MRCDPLS/FdD_Equipo_07/Proyecto/MóduloMecánico/Certificados/Marcelo Alarcon Camones/CertificadosUnidos-Marcelo.pdf

Marcelo Alarcón

Introduction to Sketching

April 28, 2026

Marcelo Alarcón

Introduction to Part Studios

April 28, 2026

Marcelo Alarcón

April 28, 2026

Introduction to Onshape Assemblies

Marcelo Alarcón

April 28, 2026

Detailed Drawings

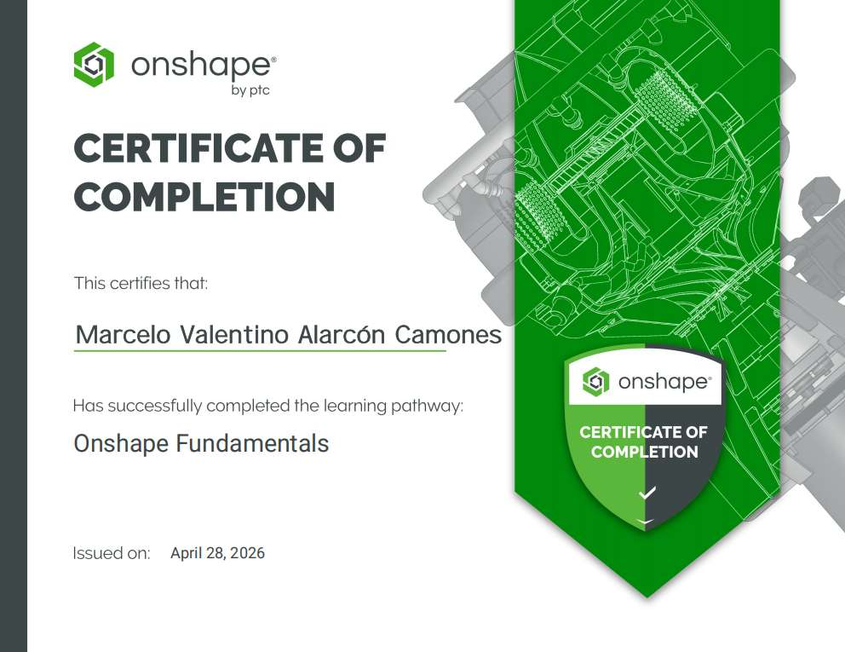
[picture p44: page 5]
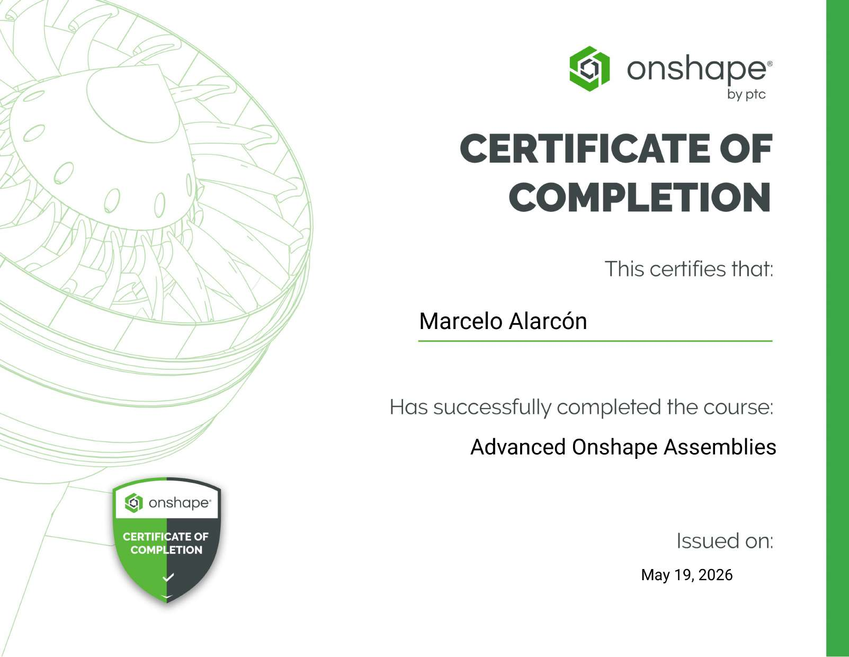
[picture p45: page 6]
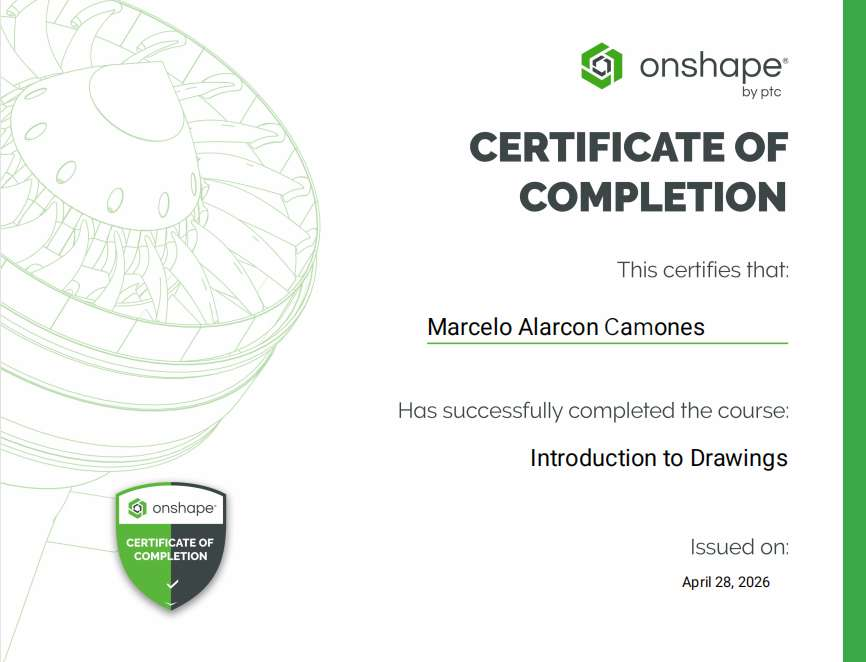
[picture p46: page 7]
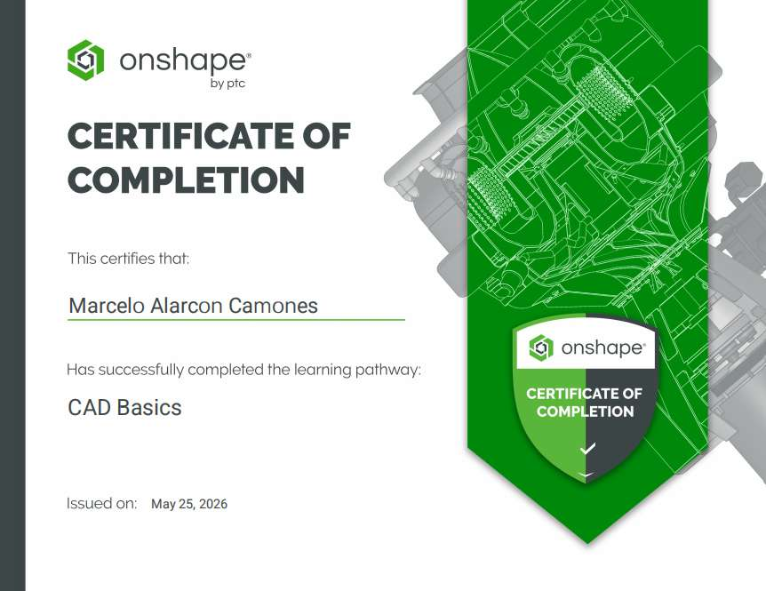
[picture p47: page 8]
