MRCDPLS/FdD_Equipo_07/Proyecto/MóduloMecánico/Certificados/Mariluz Quispe Garcia/CertificadosUnidos-Mariluz.pdf

Mariluz Quispe Garcia

Introduction to Sketching

April 28, 2026

Mariluz Quispe Garcia

Introduction to Part Studios

April 28, 2026

Mariluz Quispe Garcia

April 28, 2026

Introduction to Onshape Assemblies

Mariluz Quispe Garcia

April 28, 2026

Detailed Drawings

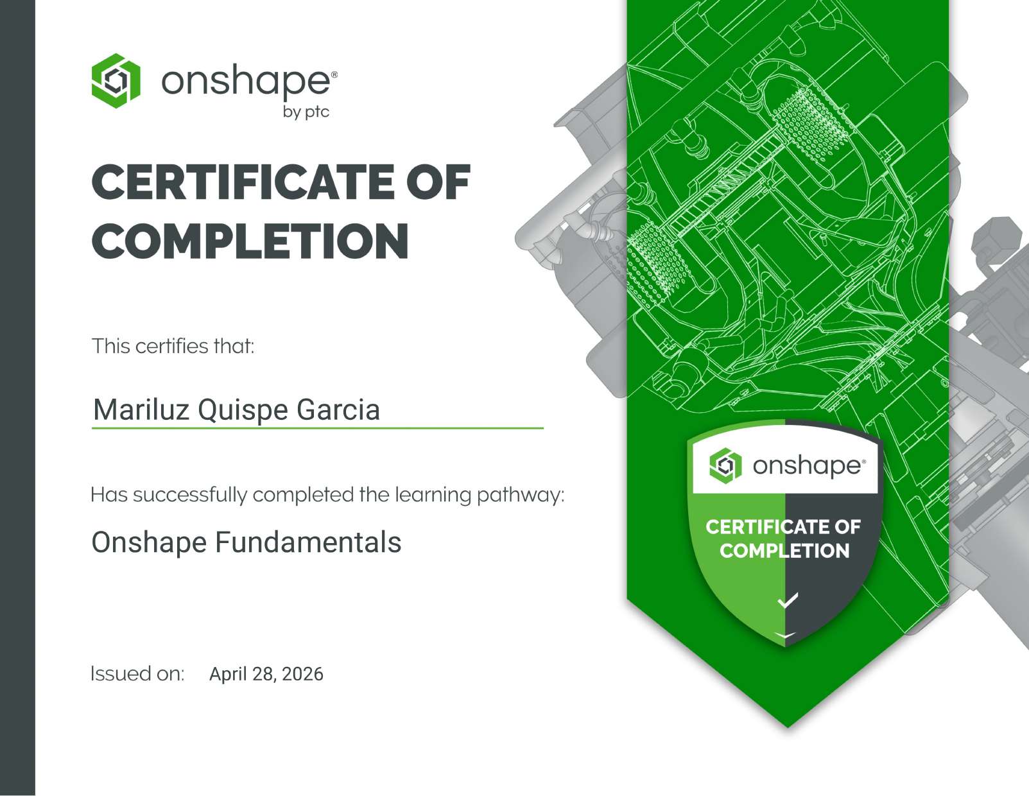
[picture p48: page 5]
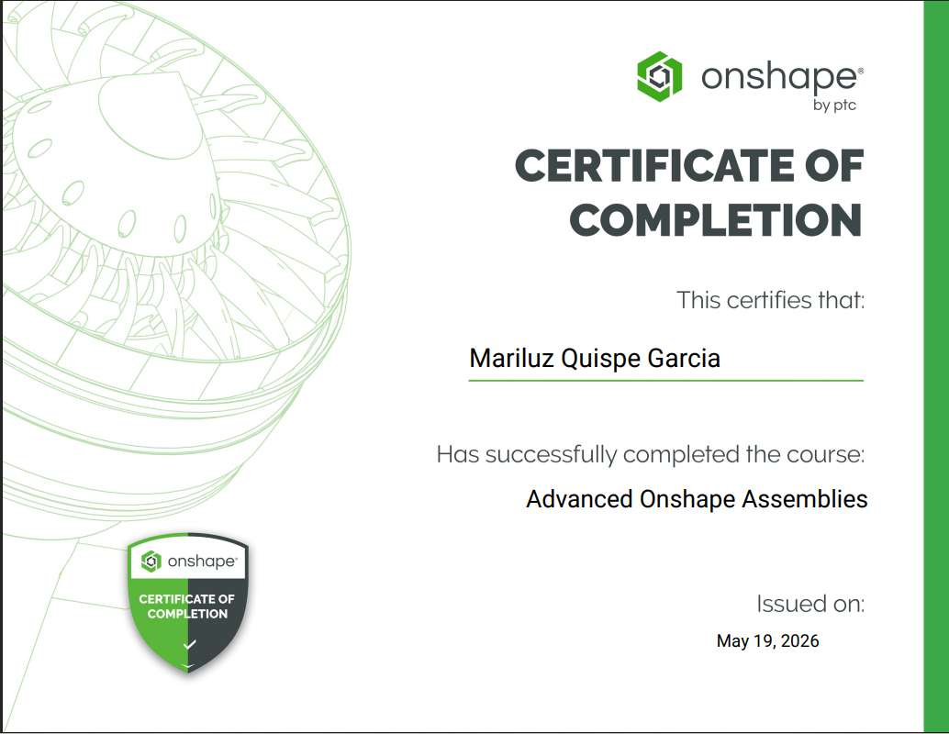
[picture p49: page 6]

Mariluz Quispe Garcia

April 28, 2026

Introduction to Drawings

Mariluz Quispe Garcia

CAD Basics

May 25, 2026
