MRCDPLS/FdD_Equipo_07/Proyecto/MóduloMecánico/Certificados/Rebeca Cerdan Dongo/CertificadosUnidos-Rebeca.pdf

Rebeca Milagros Cerdan Dongo

Introduction to Sketching

April 28, 2026

Rebeca Milagros Cerdan Dongo

Introduction to Part Studios

April 28, 2026

Rebeca Milagros Cerdan Dongo

April 28, 2026

Introduction to Onshape Assemblies

Rebeca Milagros Cerdan Dongo

April 28, 2026

Detailed Drawings

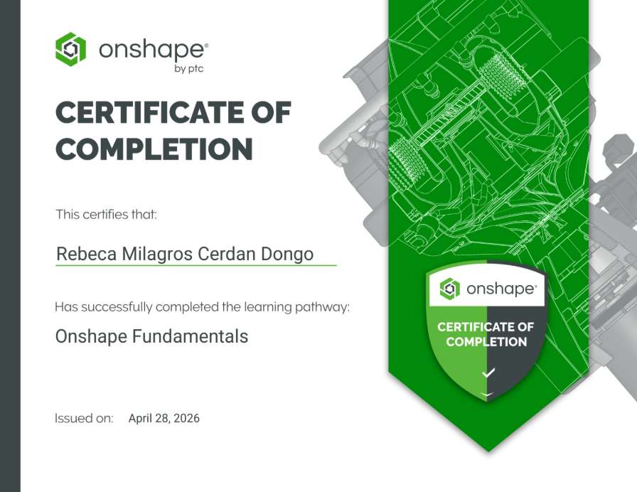
[picture p50: page 5]
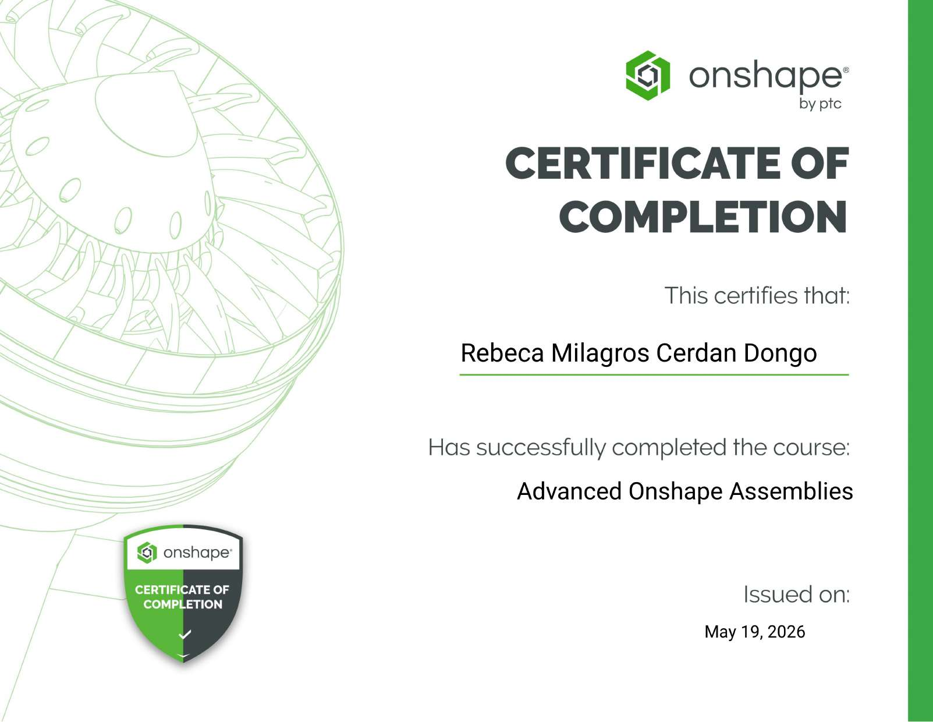
[picture p51: page 6]

Rebeca Milagros Cerdan Dongo

May 25, 2026

Introduction to Drawings

Rebeca Milagros Cerdan Dongo

CAD Basics

May 25, 2026
