MRCDPLS/FdD_Equipo_07/Proyecto/MóduloMecánico/Certificados/Yakori Fernandez Rimarachin/CertificadosUnidos-Yakori.pdf

Yakori Siclali Fernandez Rimarachin

Introduction to Sketching

April 28, 2026

Yakori Siclali Fernandez Rimarachin

Introduction to Part Studios

April 28, 2026

Yakori Siclali Fernandez Rimarachin

April 28, 2026

Introduction to Onshape Assemblies

Yakori Siclali Fernandez Rimarachin

April 28, 2026

Detailed Drawings

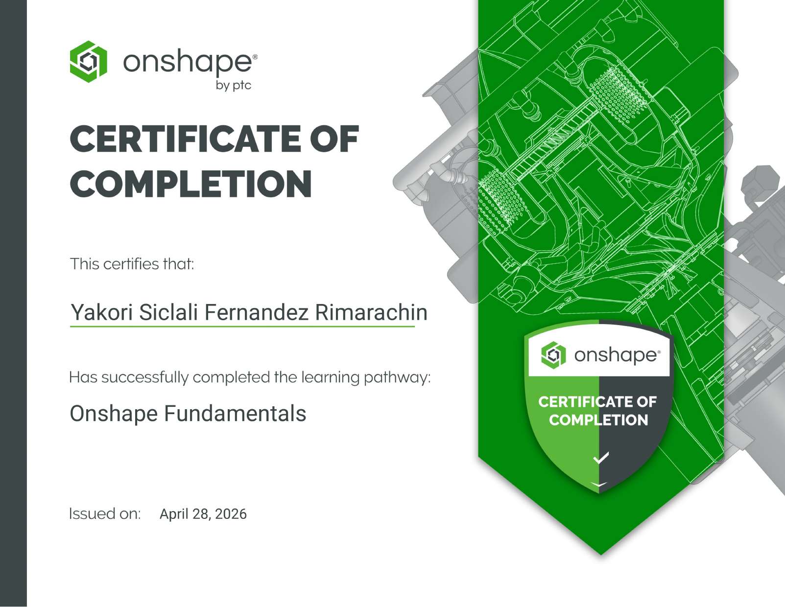
[picture p52: page 5]
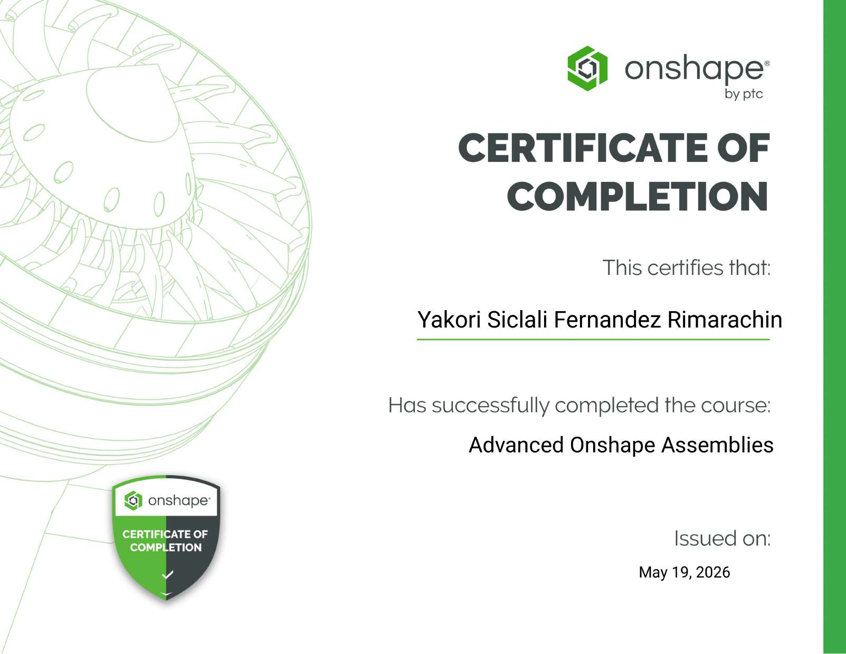
[picture p53: page 6]

Yakori Siclali Fernandez Rimarachin

May 25, 2026

Introduction to Drawings

Yakori Siclali Fernandez Rimarachin

CAD Basics

May 25, 2026
