MRCDPLS/FdD_Equipo_07/FundDiseño/Presentaciones de Proyecto/AVANCE DE PROYECTO 1.pdf

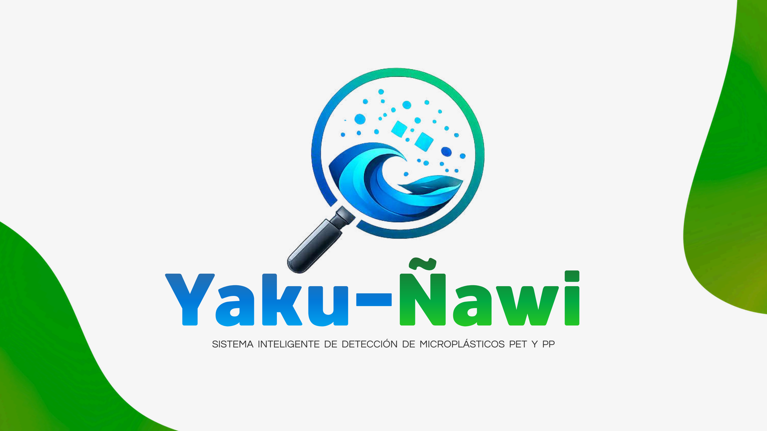
[picture p150: page 1]

# Yaku-Ñawi

## SISTEMA INTELIGENTE DE DETECCIÓN DE MICROPLÁSTICOS PET Y PP


# PROBLEMÁTICA

# La acumulación de microplásticos en cuerpos de agua amenaza los

ecosistemas acuáticos y la salud humana.

millones | 40 %

# De los residuos plásticos no recibe una gestión adecuada

## De toneladas de plástico se liberan al ambiente cada año

80 %

# Más del

# de las muestras en playas peruanas contienen microplásticos

52

residuos-noticia/#google_vignette

https://gestion.pe/mundo/cada-ano-se-liberan-mas-de-52-millones-detoneladas-de-plasticos-al-medioambiente-desechos-reino-unido-basura-

Geyer R, Jambeck JR, Law KL. Production, use, and fate of all plastics ever made. Sci Adv. 2017;3(7):e1700782. doi:10.1126/sciadv.1700782 https://observatorio.ceplan.gob.pe/ficha/t53

# TECNOLOGÍA EXISTENTE


# ANÁLISIS DE PATENTES EXISTENTES

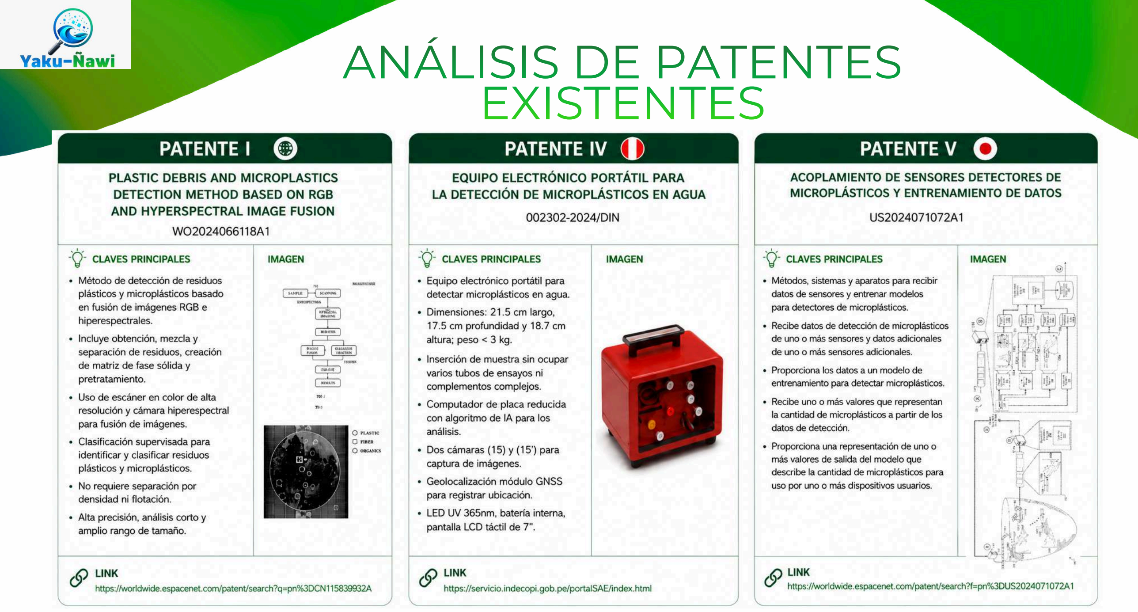
[picture p151: page 4]

# INVESTIGACIÓN ACADÉMICA

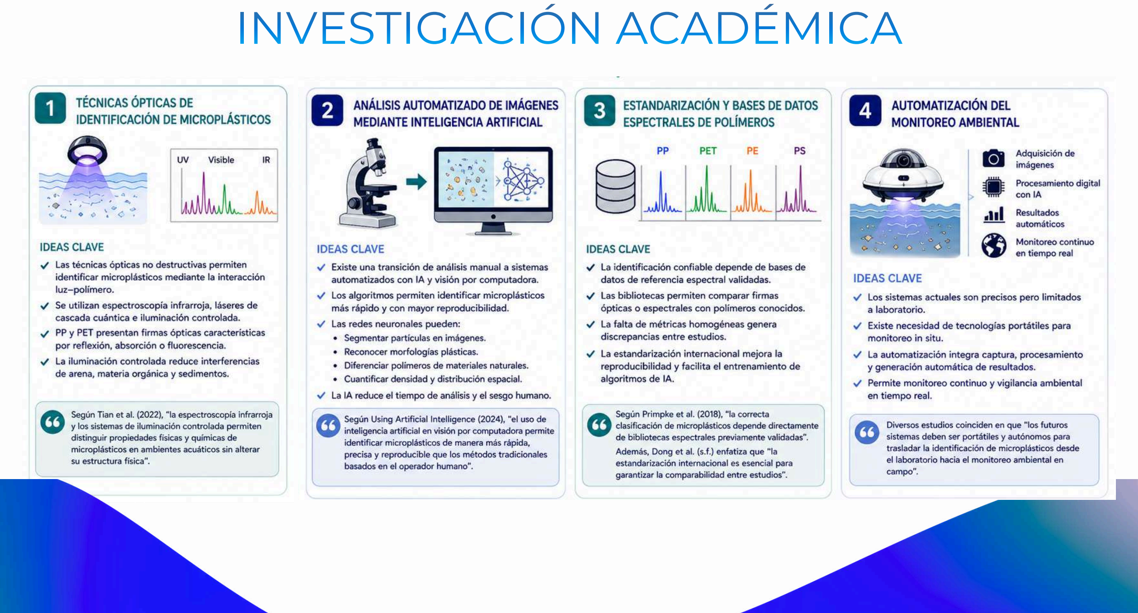
[picture p152: page 5]

# TESIS DE REPOSITORIOS


# Identificación automática de microplásticos

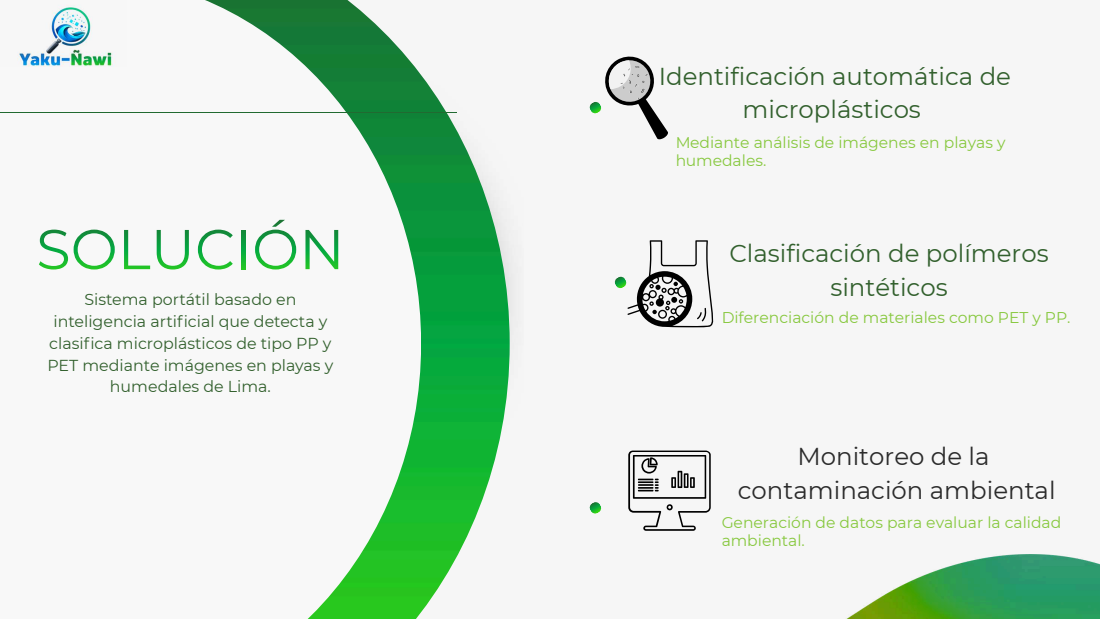
[picture p153: page 7]
SOLUCIÓN; sintéticos

Mediante análisis de imágenes en playas y
humedales.

Clasificación de polímeros

Sistema portátil basado en
inteligencia artificial que detecta y
clasifica microplásticos de tipo PP y
PET mediante imágenes en playas y

Diferenciación de materiales como PET y PP.

humedales de Lima.

Monitoreo de la
contaminación ambiental

Generación de datos para evaluar la calidad
ambiental.

# PROPUESTA DE VALOR

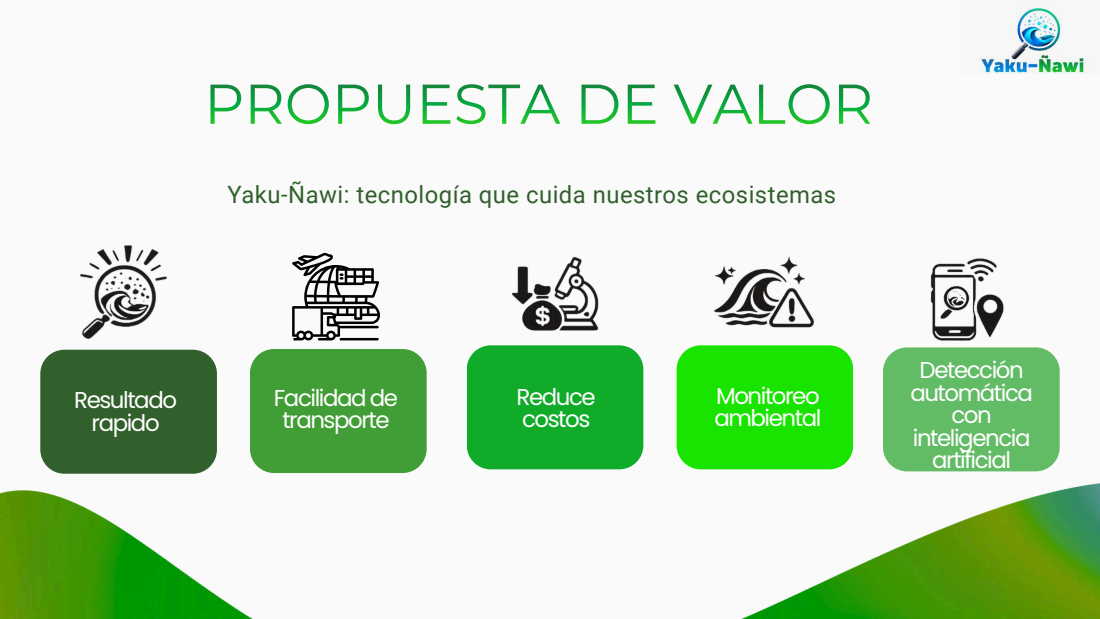
[picture p154: page 8]
Resultado rapido; Facilidadde transporte; Reduce costos; Monitoreo ambiental; Detección automática con inteligencia artificial

Yaku-Ñawi: tecnología que cuida nuestros ecosistemas

# LISTA DE EXIGENCIAS

## FUNCIÓN PRINCIPAL

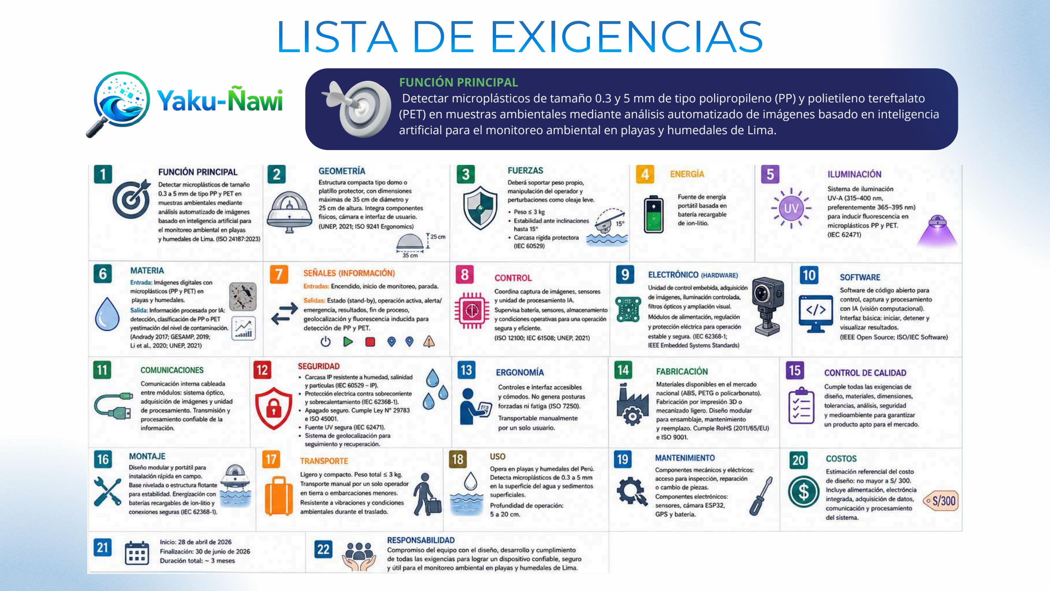
[picture p155: page 9]

Detectar microplásticos de tamaño 0.3 y 5 mm de tipo polipropileno (PP) y polietileno tereftalato (PET) en muestras ambientales mediante análisis automatizado de imágenes basado en inteligencia artificial para el monitoreo ambiental en playas y humedales de Lima.

# IDEALIZACIÓN DE PRODUCTO

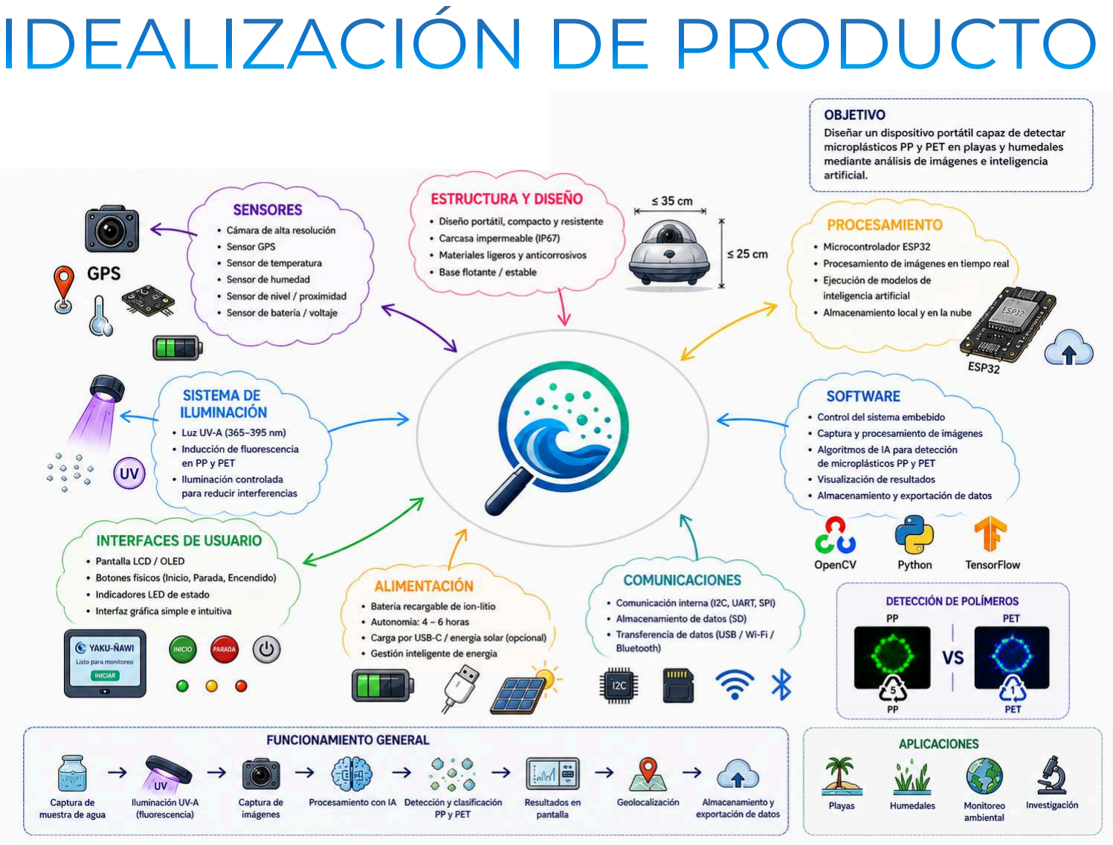
[picture p156: page 10]

# ESTRUCTURA DE FUNCIONES

# Caja Negra (Black Box)

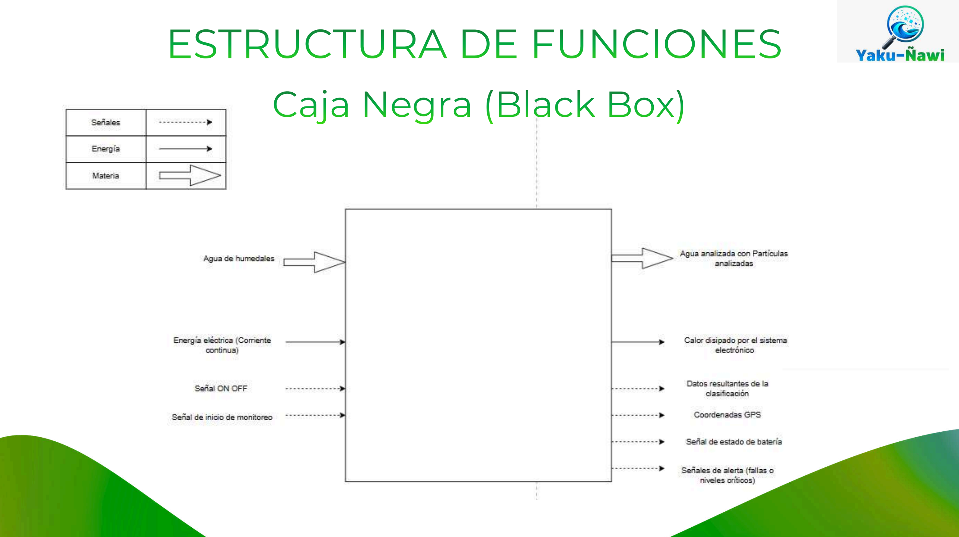
[picture p157: page 11]

# Secuencia de Operaciones

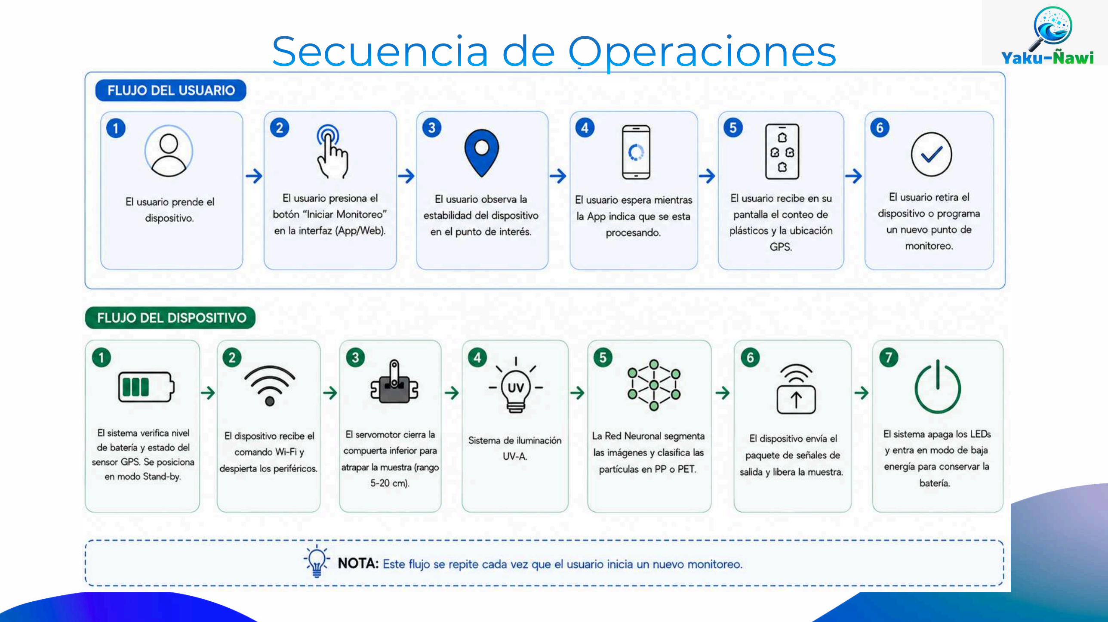
[picture p158: page 12]

# Caja Blanca

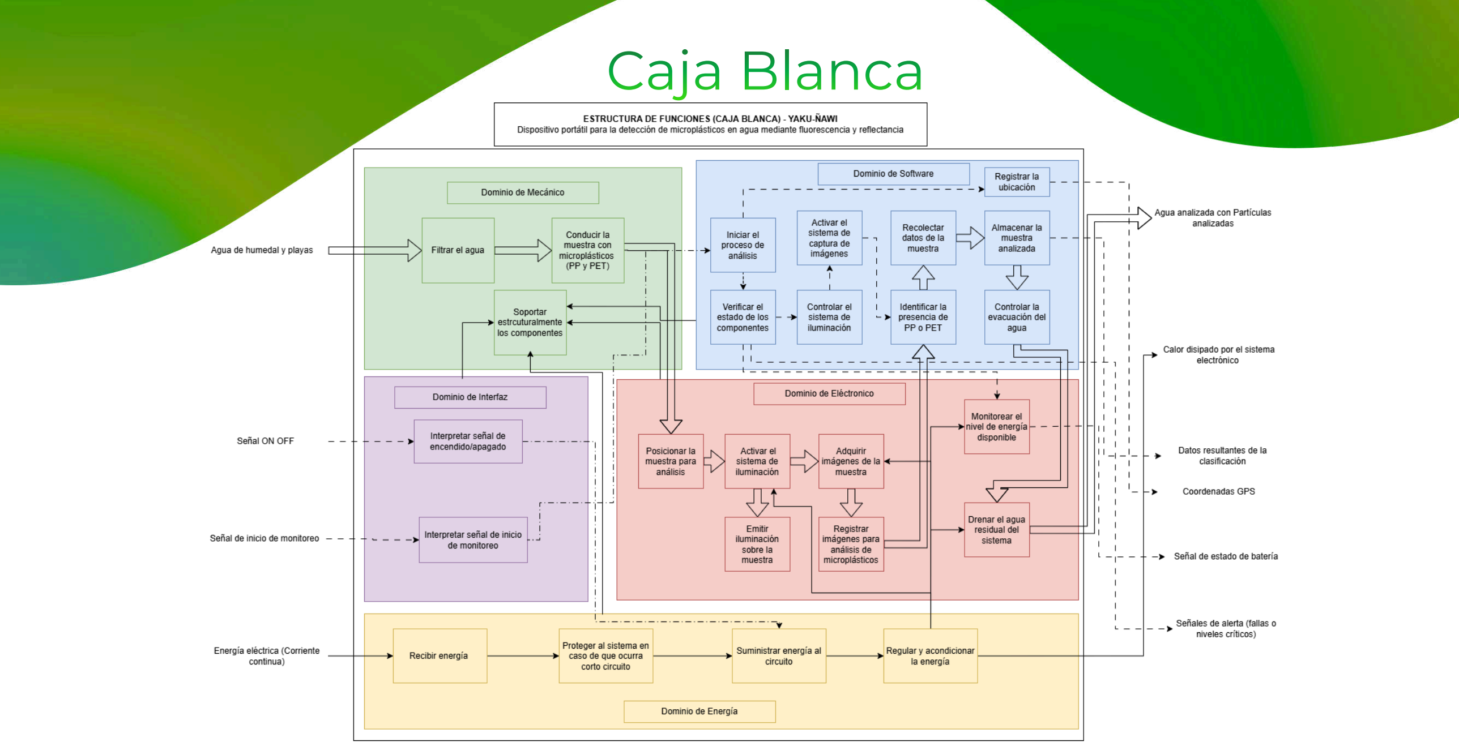
[picture p159: page 13]

# Estructura de Funciones Integradas

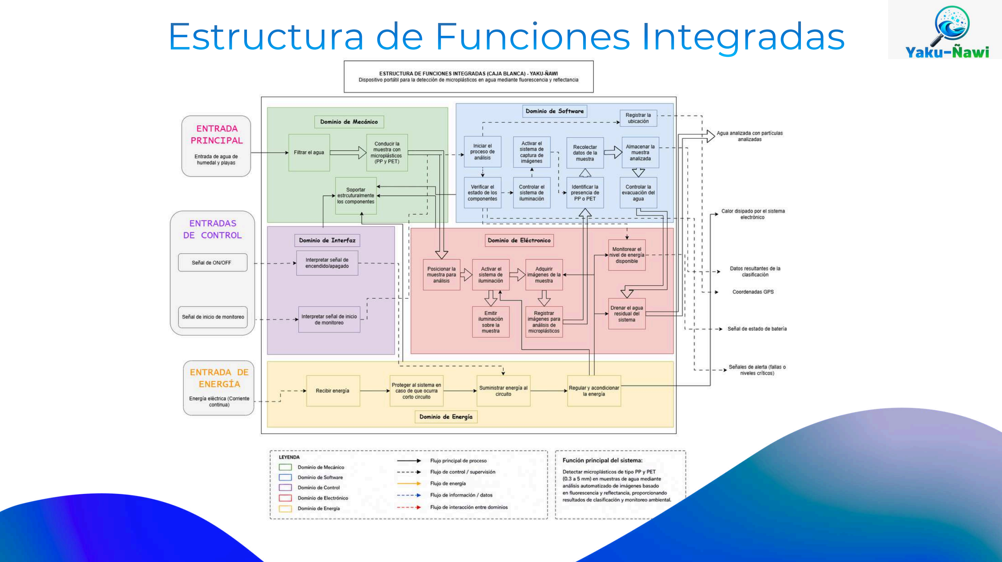
[picture p160: page 14]
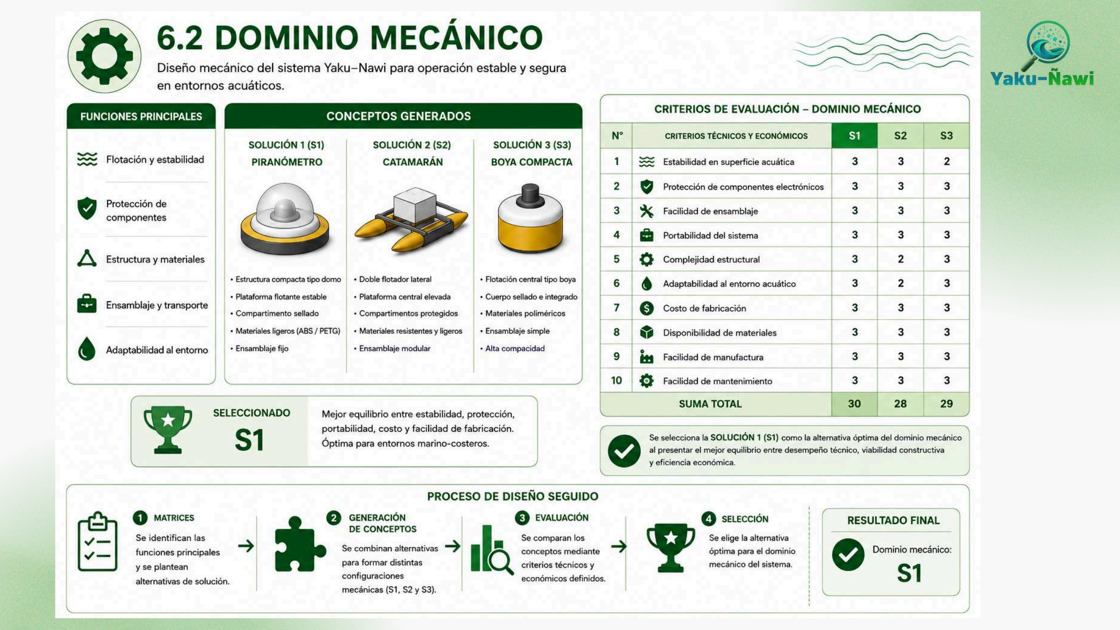
[picture p161: page 16]
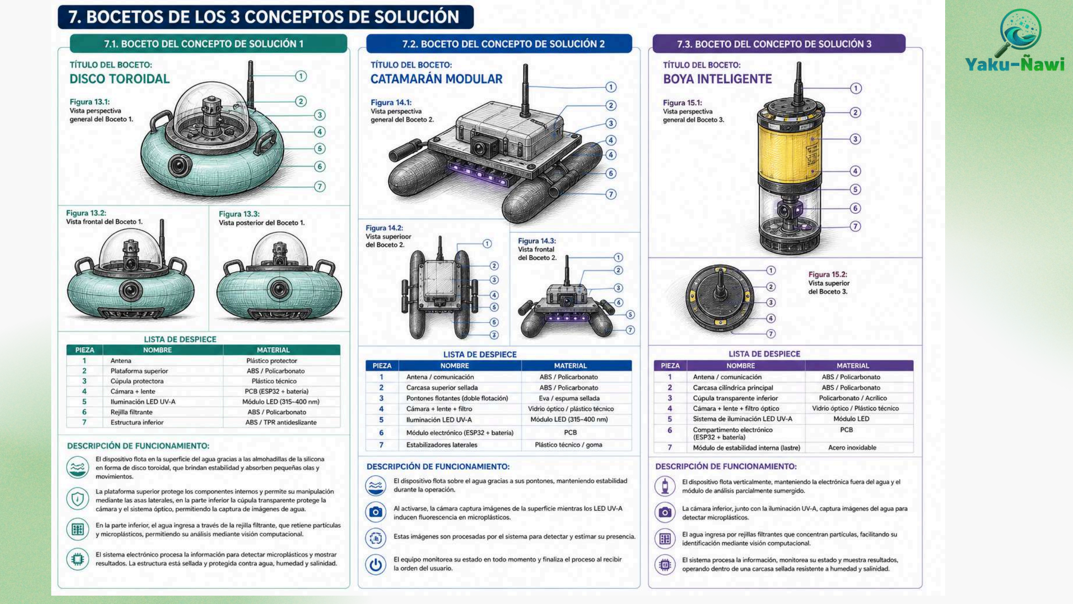
[picture p162: page 20]
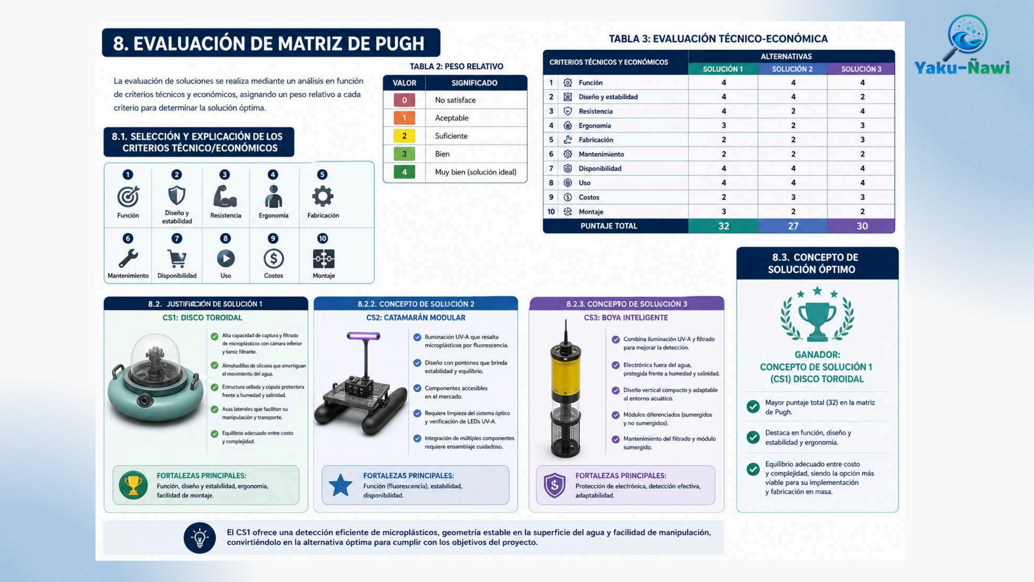
[picture p163: page 21]

# PÚBLICO OBJETIVO

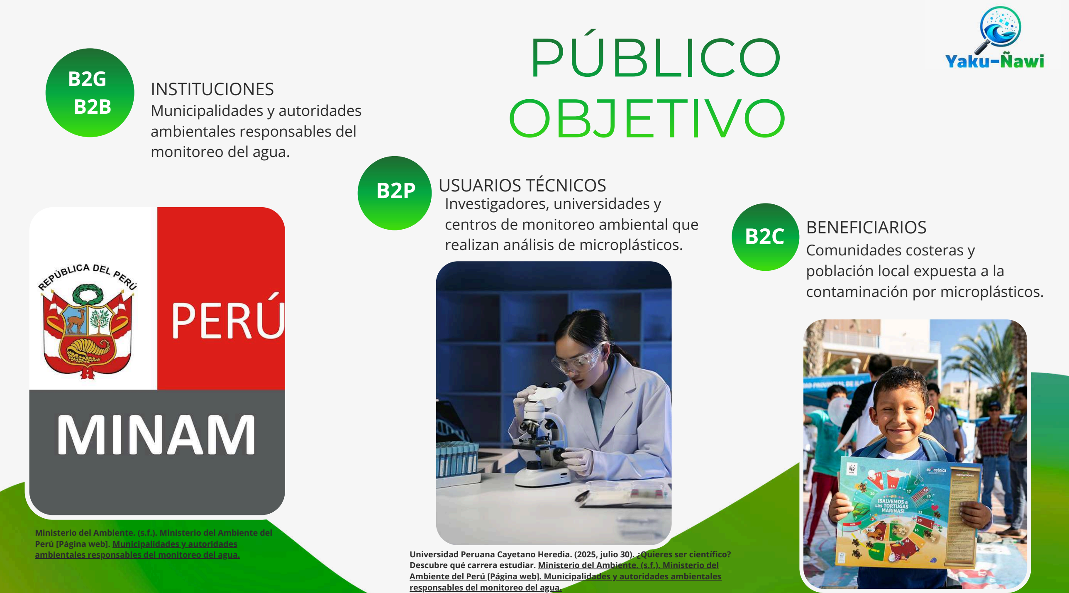
[picture p164: page 22]

# INSTITUCIONES B2G

B2B Municipalidades y autoridades ambientales responsables del monitoreo del agua.

B2P

# Investigadores, universidades y centros de monitoreo ambiental que

realizan análisis de microplásticos.

# USUARIOS TÉCNICOS

# BENEFICIARIOS

# Comunidades costeras y población local expuesta a la

contaminación por microplásticos.

B2C

Ministerio del Ambiente. (s.f.). Ministerio del Ambiente del
Perú [Página web]. Municipalidades y autoridades
ambientales responsables del monitoreo del agua. (https://www.gob.pe/minam) | Universidad Peruana Cayetano Heredia. (2025, julio 30). ¿Quieres ser científico?
| Descubre qué carrera estudiar. Ministerio del Ambiente. (s.f.). Ministerio del
| Ambiente del Perú [Página web]. Municipalidades y autoridades ambientales
| responsables del monitoreo del agua. (https://blogs.cayetano.edu.pe/pregrado/que-carrera-estudiar-ser-cientifico/)

# MODELO DE NEGOCIO

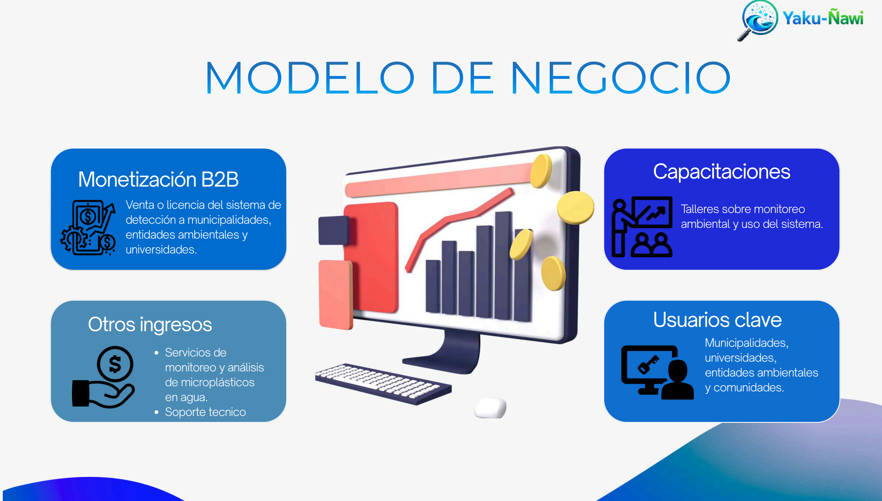
[picture p165: page 23]

Monetización B2B | Capacitaciones

# Otros ingresos

## Venta o licencia del sistema de

detección a municipalidades,

## entidades ambientales y

universidades.

## Talleres sobre monitoreo

ambiental y uso del sistema.

## Servicios de monitoreo y análisis de microplásticos

en agua.

## Soporte tecnico

# Usuarios clave

Municipalidades,
universidades,

## entidades ambientales

y comunidades.

# EQUIPO


RebecaCerdan | MarceloAlarcon | Yakori Fernandez | MariluzQuispe | BrunoEvangelista
