MRCDPLS/FdD_Equipo_07/Recursos/Patentes/Patente 4-002302-2024DIN.pdf

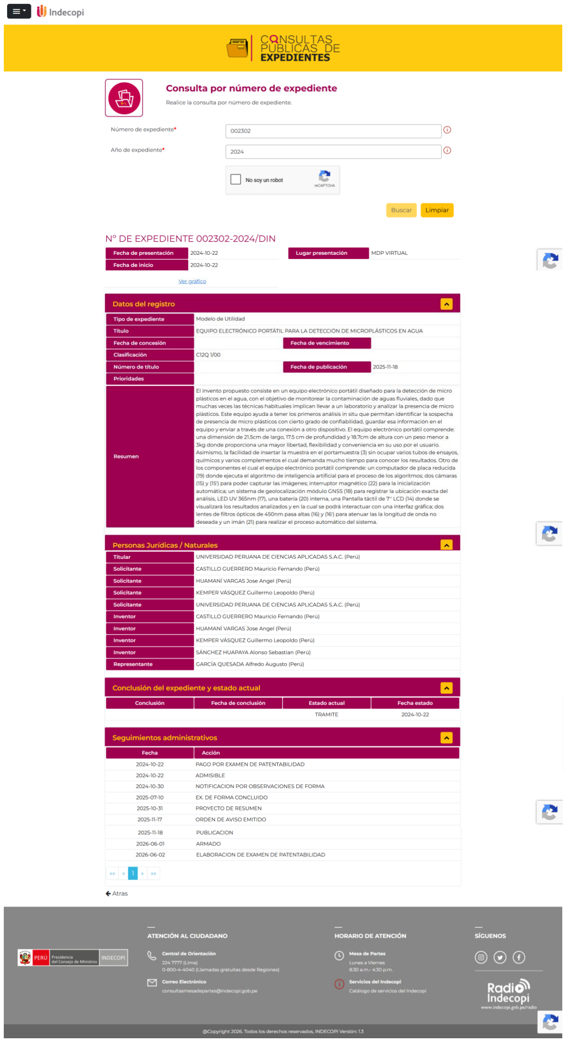
[picture p198: page 1]
