MRCDPLS/FdD_Equipo_07/Proyecto/MóduloMecánico/V3.0/Bocetos/Boceto_ YAKU ÑAWI.pdf

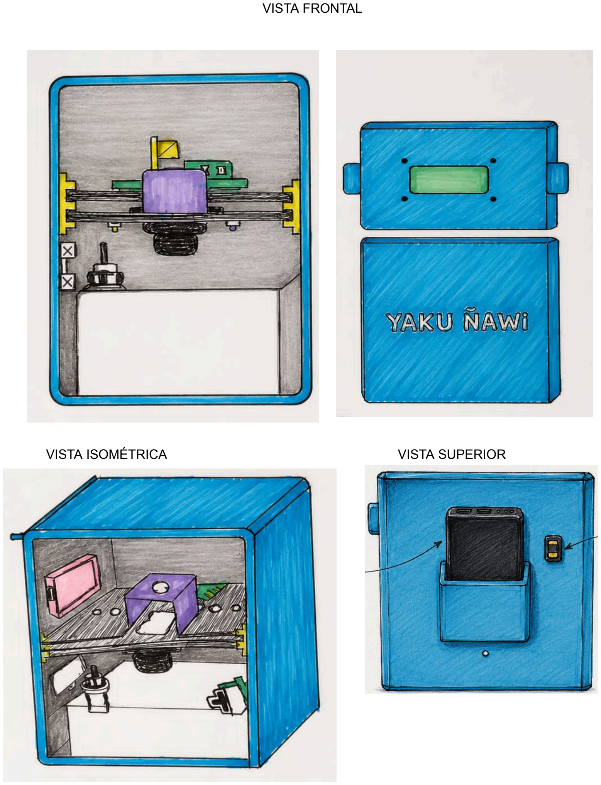
[picture p199: page 1]

VISTA FRONTAL

VISTA ISOMÉTRICA | VISTA SUPERIOR

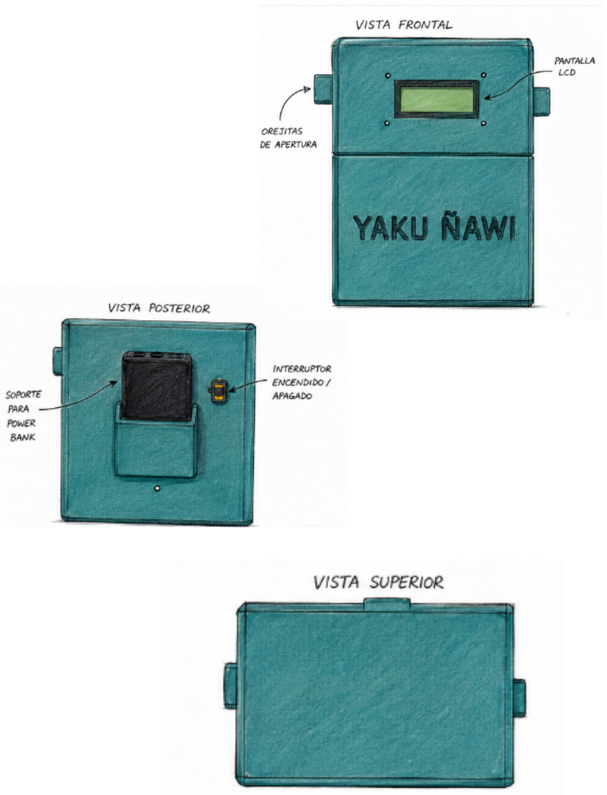
[picture p200: page 2]
