MRCDPLS/FdD_Equipo_07/Proyecto/MóduloMecánico/V2.0/Bocetos/BOCETOS VERSIÓN 2.pdf

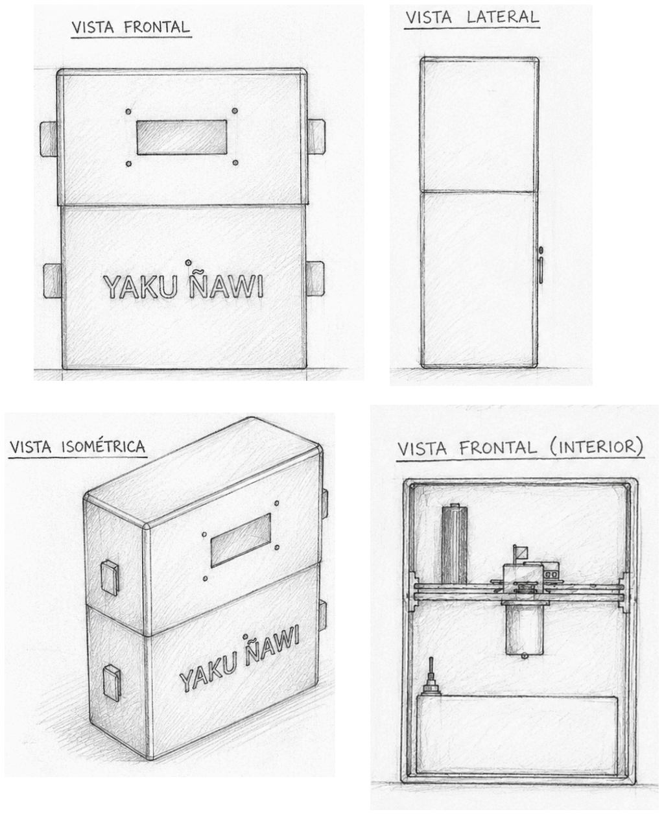
[picture p201: page 1]
