MRCDPLS/FdD_Equipo_07/Proyecto/MóduloMecánico/V1.0/Bocetos/BOCETO VERSIÓN 1.pdf

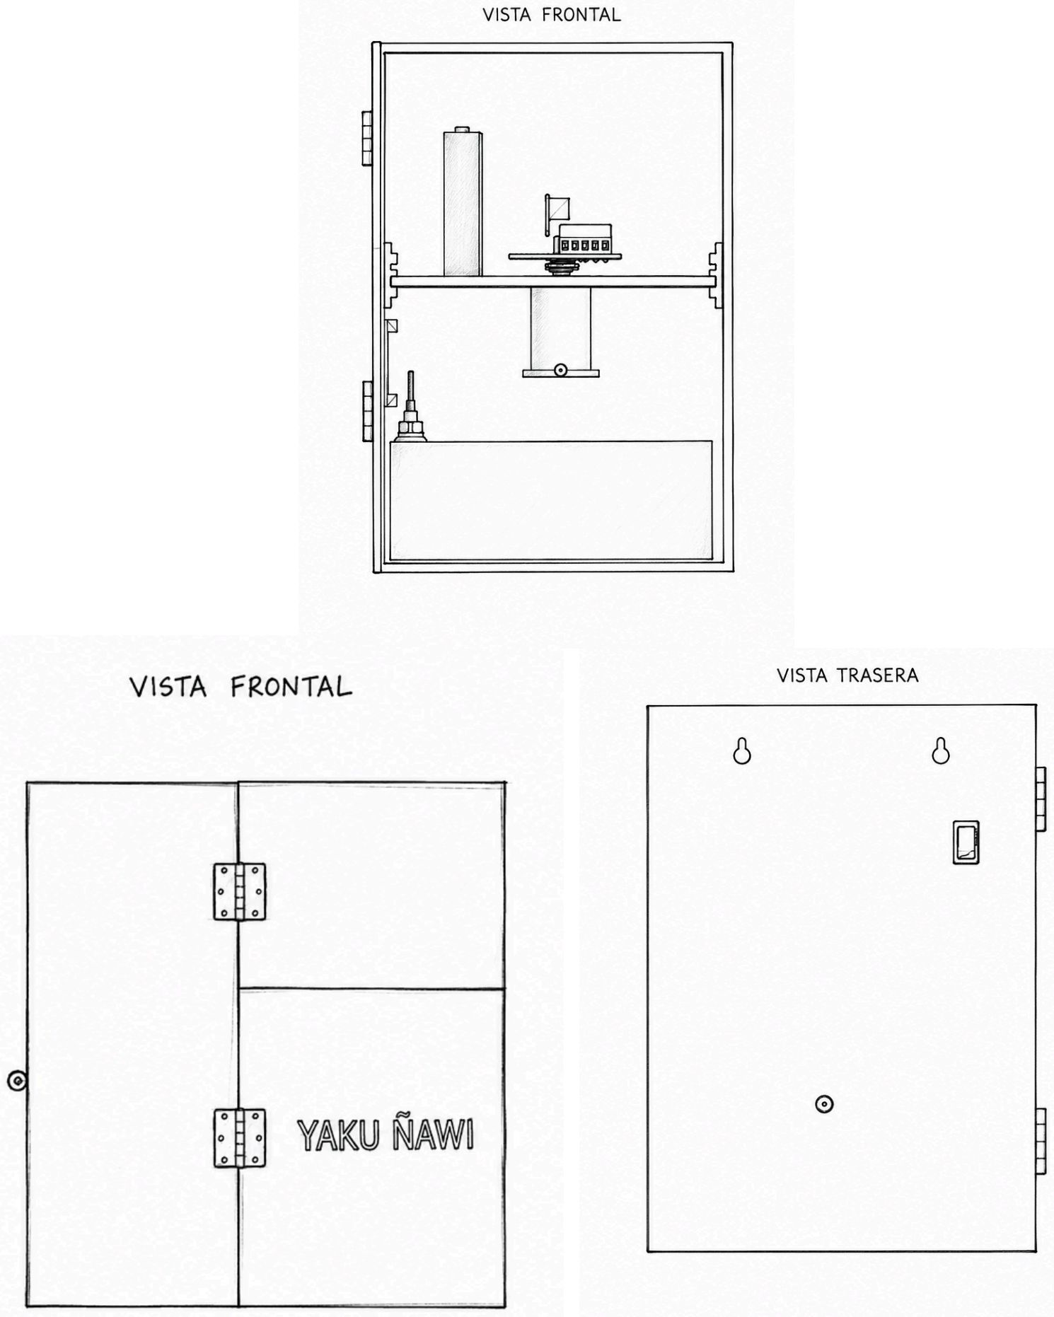
[picture p202: page 1]
