MRCDPLS/FdD_Equipo_07/Proyecto/MóduloSoftware/BoxPR_curve.png

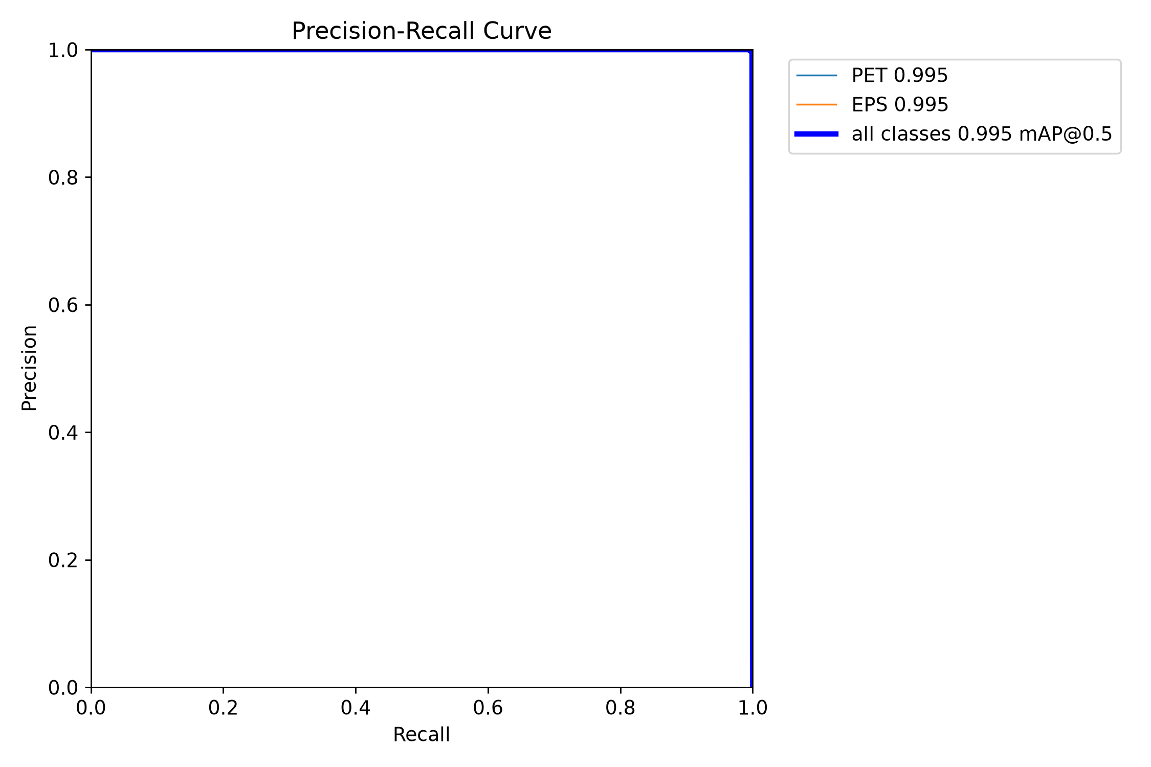
Proyecto/MóduloSoftware/BoxPR_curve.png
