MRCDPLS/FdD_Equipo_07/Proyecto/MóduloSoftware/confusion_matrix.png

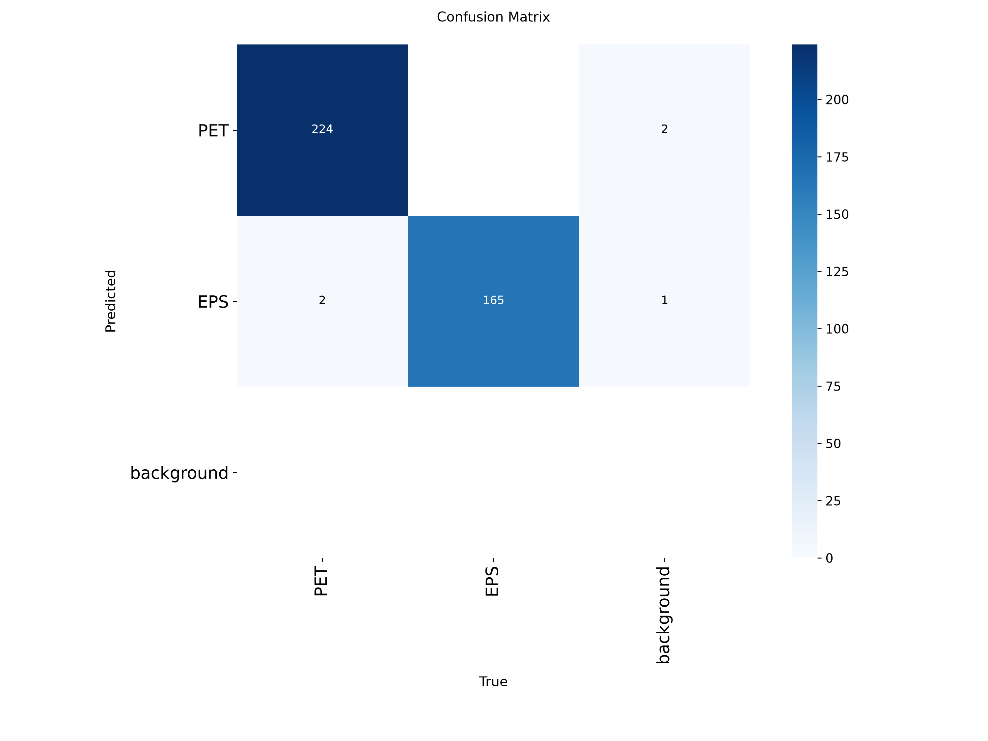
Proyecto/MóduloSoftware/confusion_matrix.png
