MRCDPLS/FdD_Equipo_07/Proyecto/MóduloSoftware/confusion_matrix_normalized.png

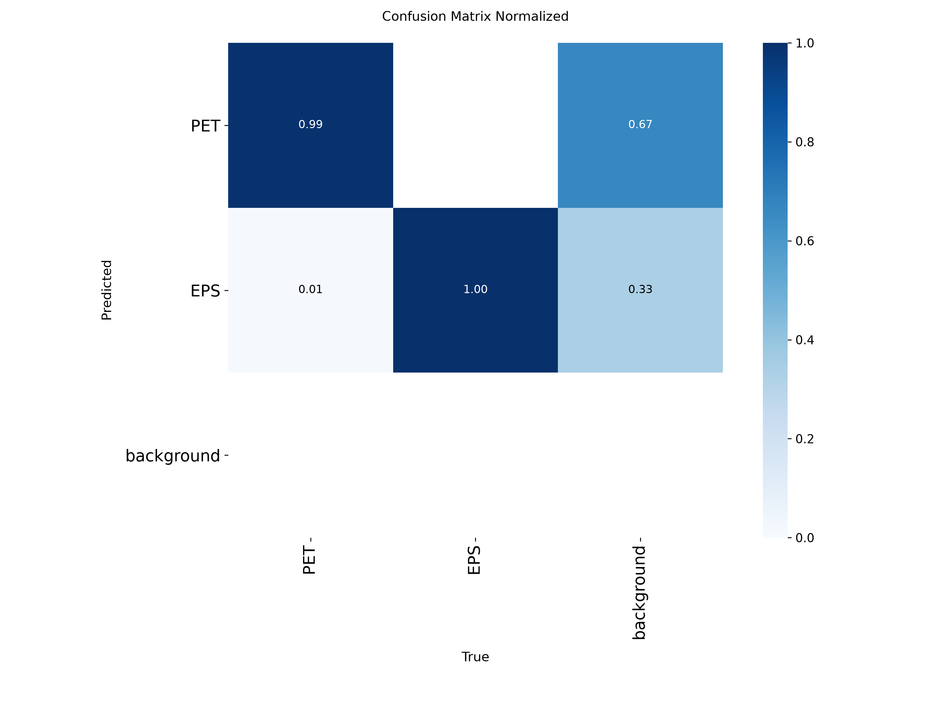
Proyecto/MóduloSoftware/confusion_matrix_normalized.png
