MRCDPLS/FdD_Equipo_07/Proyecto/MóduloSoftware/labels.jpg

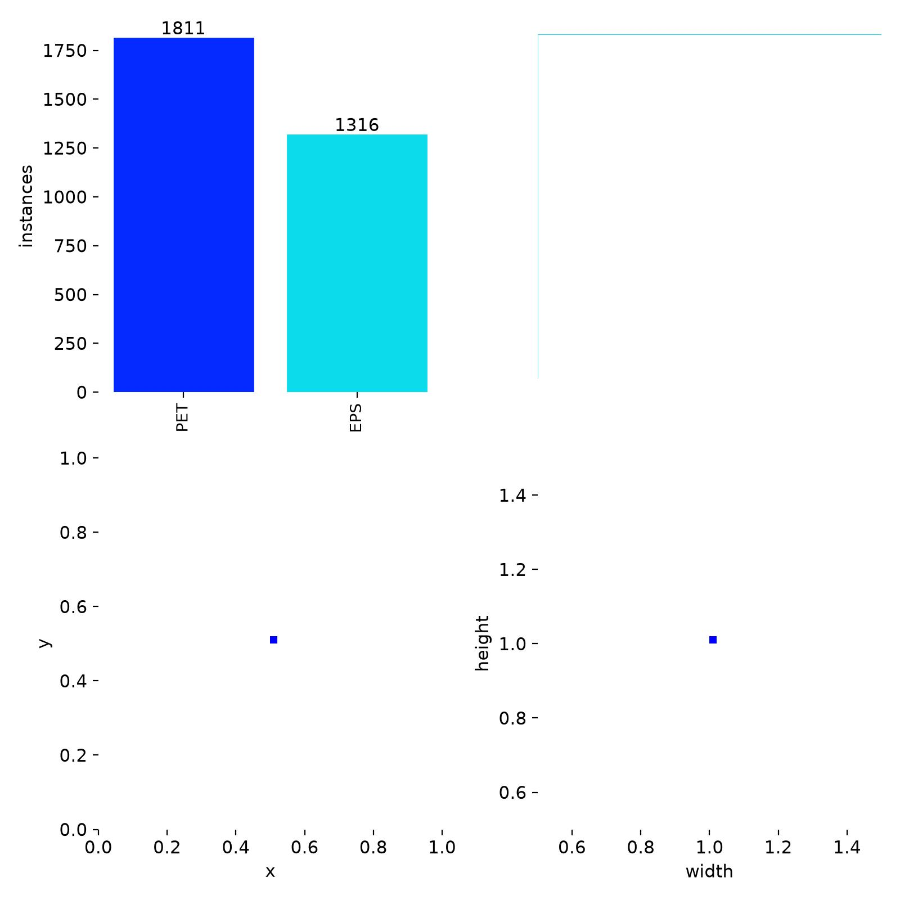
Proyecto/MóduloSoftware/labels.jpg
