MRCDPLS/FdD_Equipo_07/Proyecto/MóduloSoftware/train_batch0.jpg

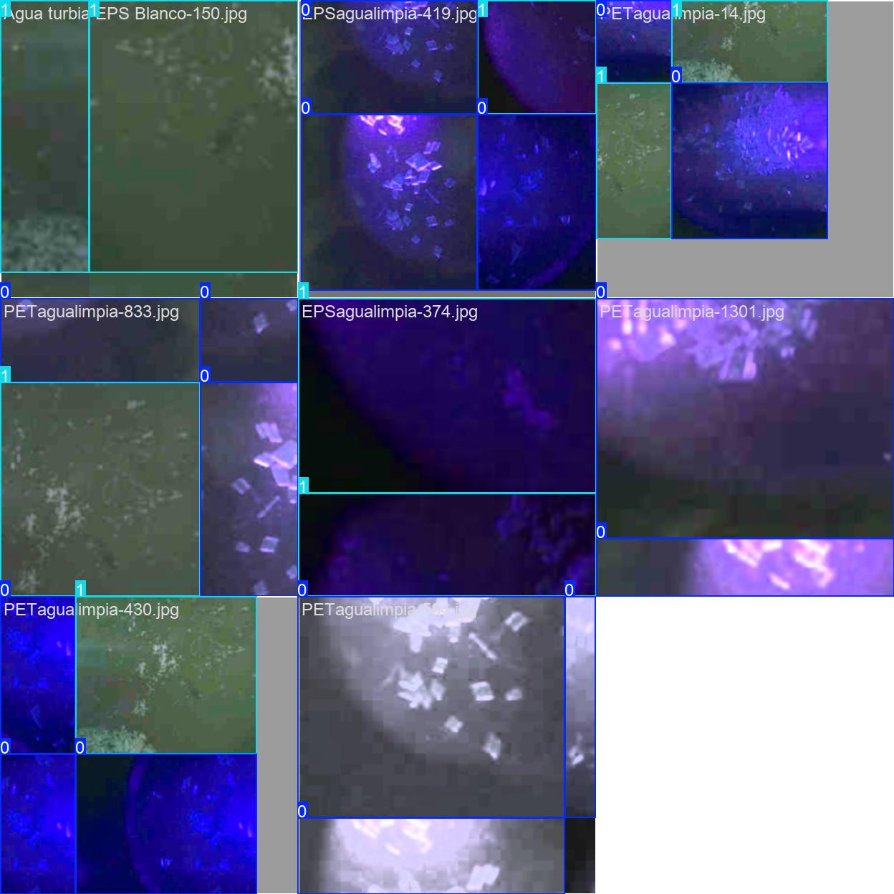
Proyecto/MóduloSoftware/train_batch0.jpg
