MRCDPLS/FdD_Equipo_07/Proyecto/MóduloSoftware/train_batch1.jpg

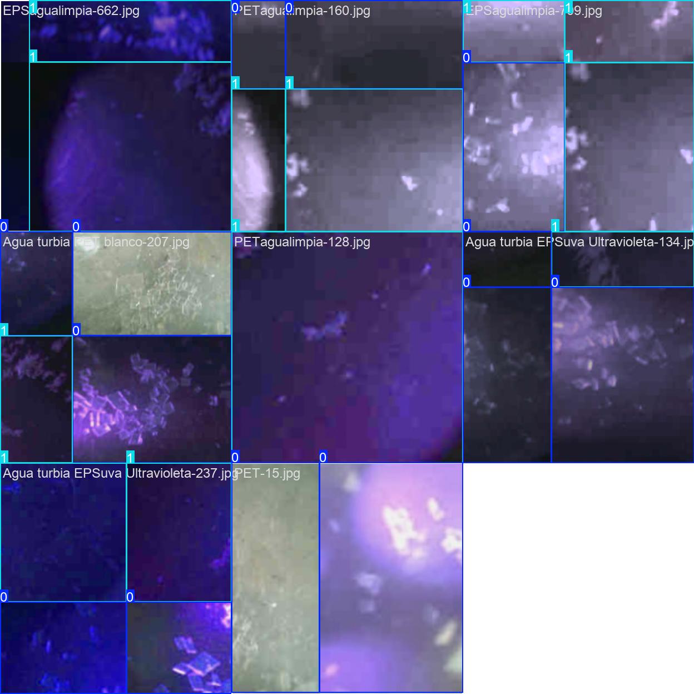
Proyecto/MóduloSoftware/train_batch1.jpg
