MRCDPLS/FdD_Equipo_07/Proyecto/MóduloSoftware/train_batch2.jpg

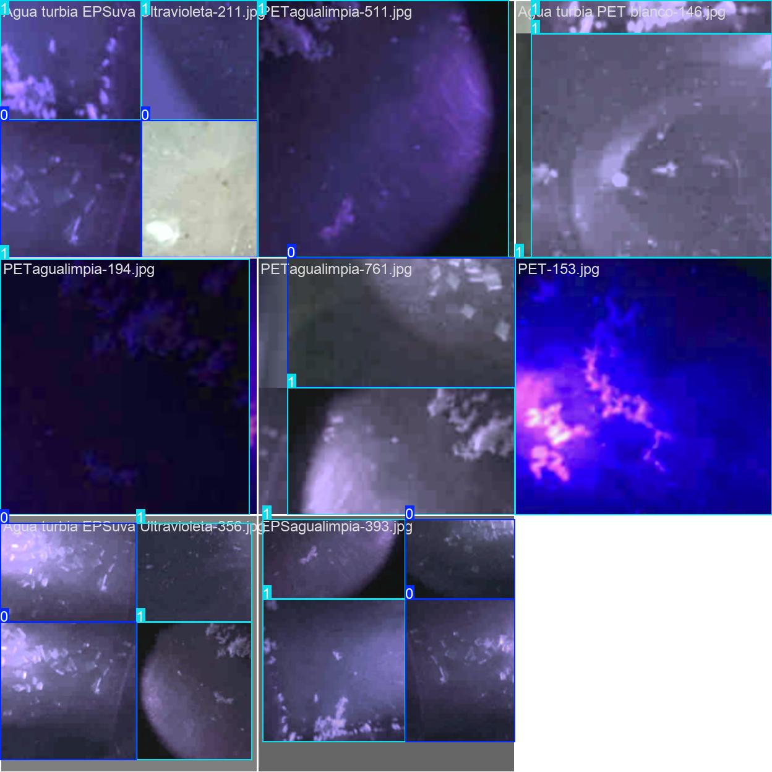
Proyecto/MóduloSoftware/train_batch2.jpg
