MRCDPLS/FdD_Equipo_07/Proyecto/MóduloSoftware/val_batch2_labels.jpg

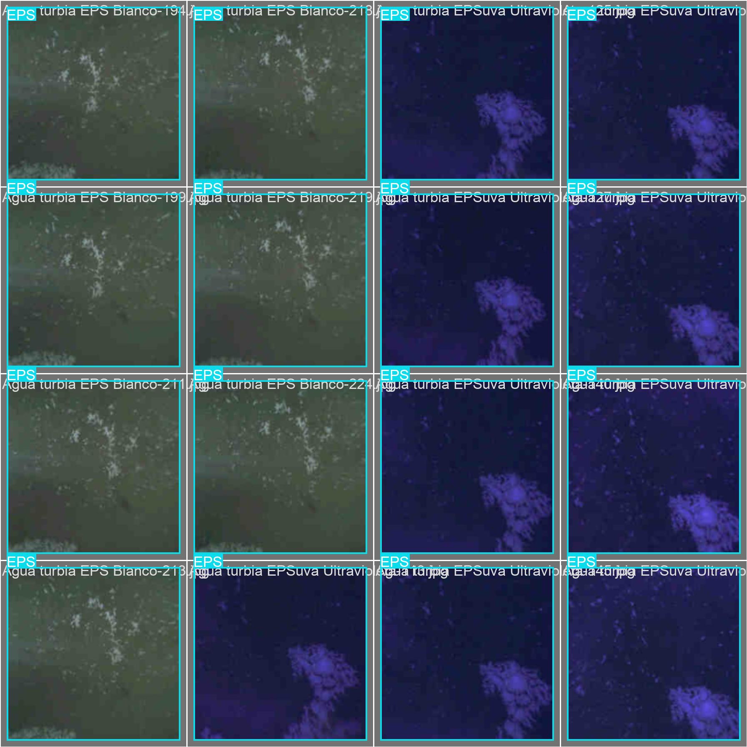
Proyecto/MóduloSoftware/val_batch2_labels.jpg
