MRCDPLS/FdD_Equipo_07/Recursos/Imágenes/CAJA_PARTE TRASERA1.jpeg

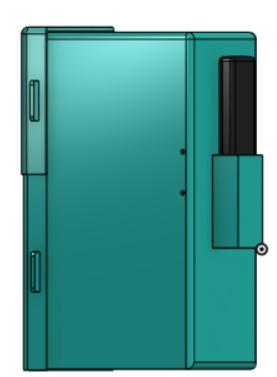
Recursos/Imágenes/CAJA_PARTE TRASERA1.jpeg
