MRCDPLS/FdD_Equipo_07/Recursos/Imágenes/CAJA_PARTE TRASERA.jpeg

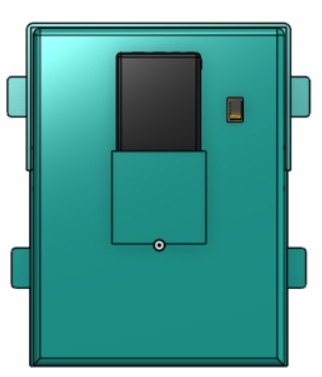
Recursos/Imágenes/CAJA_PARTE TRASERA.jpeg
