MRCDPLS/FdD_Equipo_07/Recursos/Imágenes/v3..jpeg

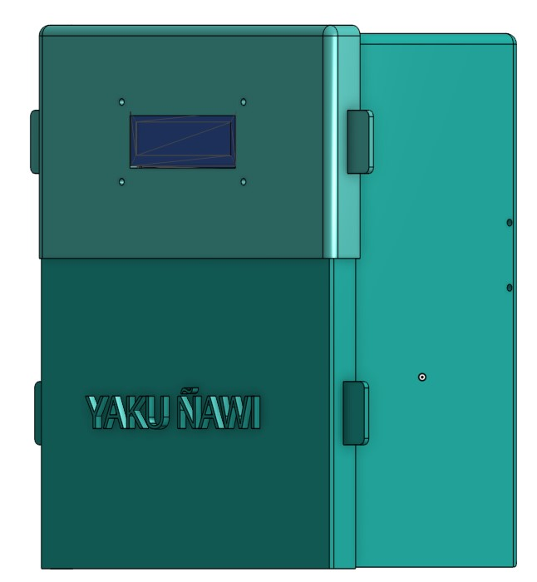
Recursos/Imágenes/v3..jpeg
