MRCDPLS/FdD_Equipo_07/Proyecto/MóduloElectrónico/VFINAL/Esquematico VFinal YAKU-ÑAWI.pdf

# CÁMARA OV3660

### MOSI

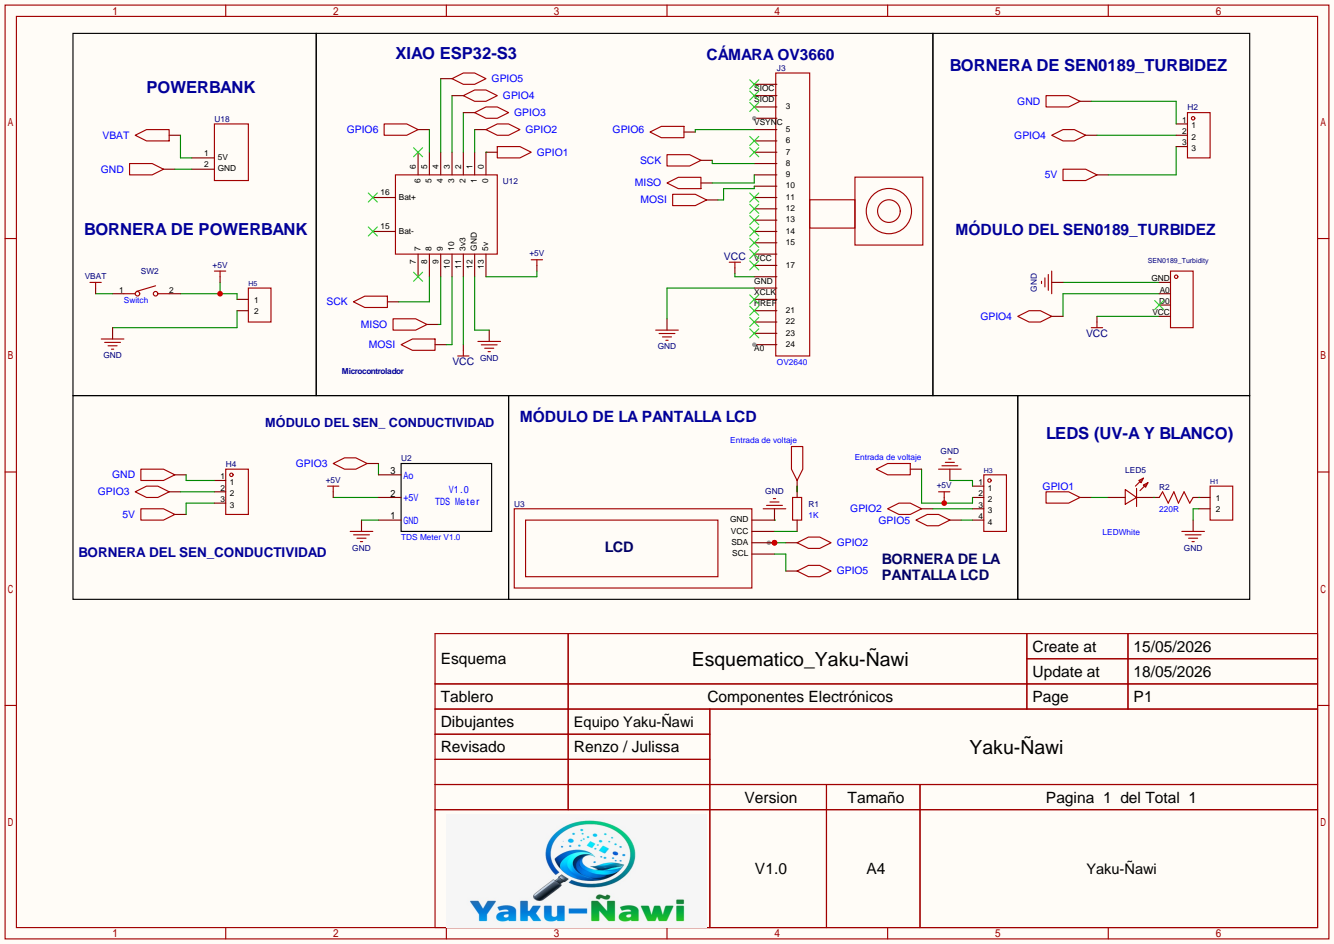
[picture p234: page 1]

MÓDULO DE LA PANTALLA LCD

LEDS (UV-A Y BLANCO) MÓDULO DEL SEN_ CONDUCTIVIDAD

Esquema | Esquematico_Yaku-Ñawi | Create at | 15/05/2026

Update at | 18/05/2026

Tablero | Componentes Electrónicos | Page | P1
Dibujantes | Equipo Yaku-Ñawi | Yaku-Ñawi
Revisado | Renzo / Julissa

Version | Tamaño | Pagina 1 del Total 1

V1.0 | A4 | Yaku-Ñawi
