MRCDPLS/FdD_Equipo_07/Proyecto/MóduloMecánico/V3.0/Onshape/Planos/V3_Cubierta de módulo de conductividad.pdf

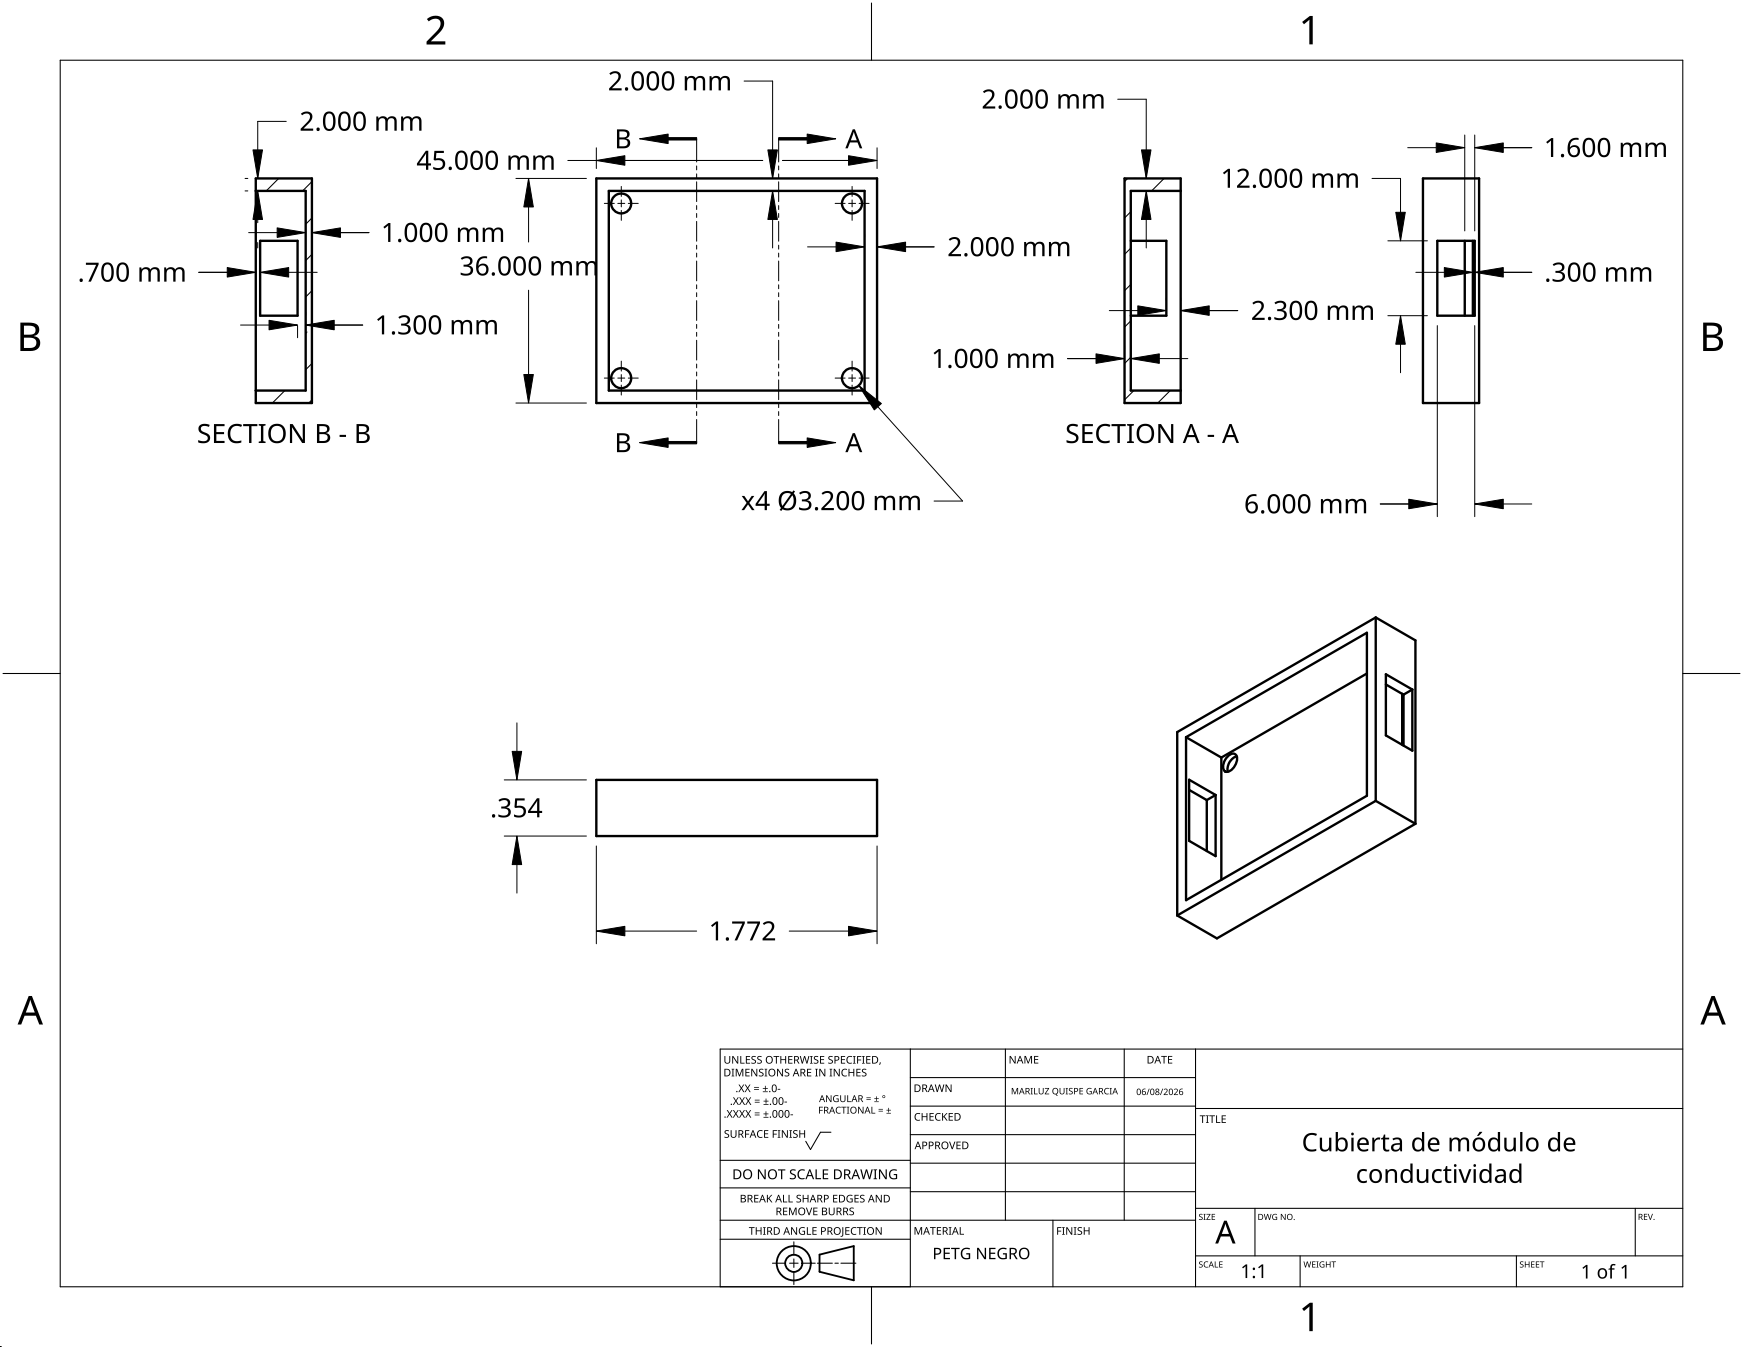
[picture p235: page 1]
