MRCDPLS/FdD_Equipo_07/Proyecto/MóduloMecánico/V3.0/Onshape/Planos/V3_Cubierta para camara.pdf

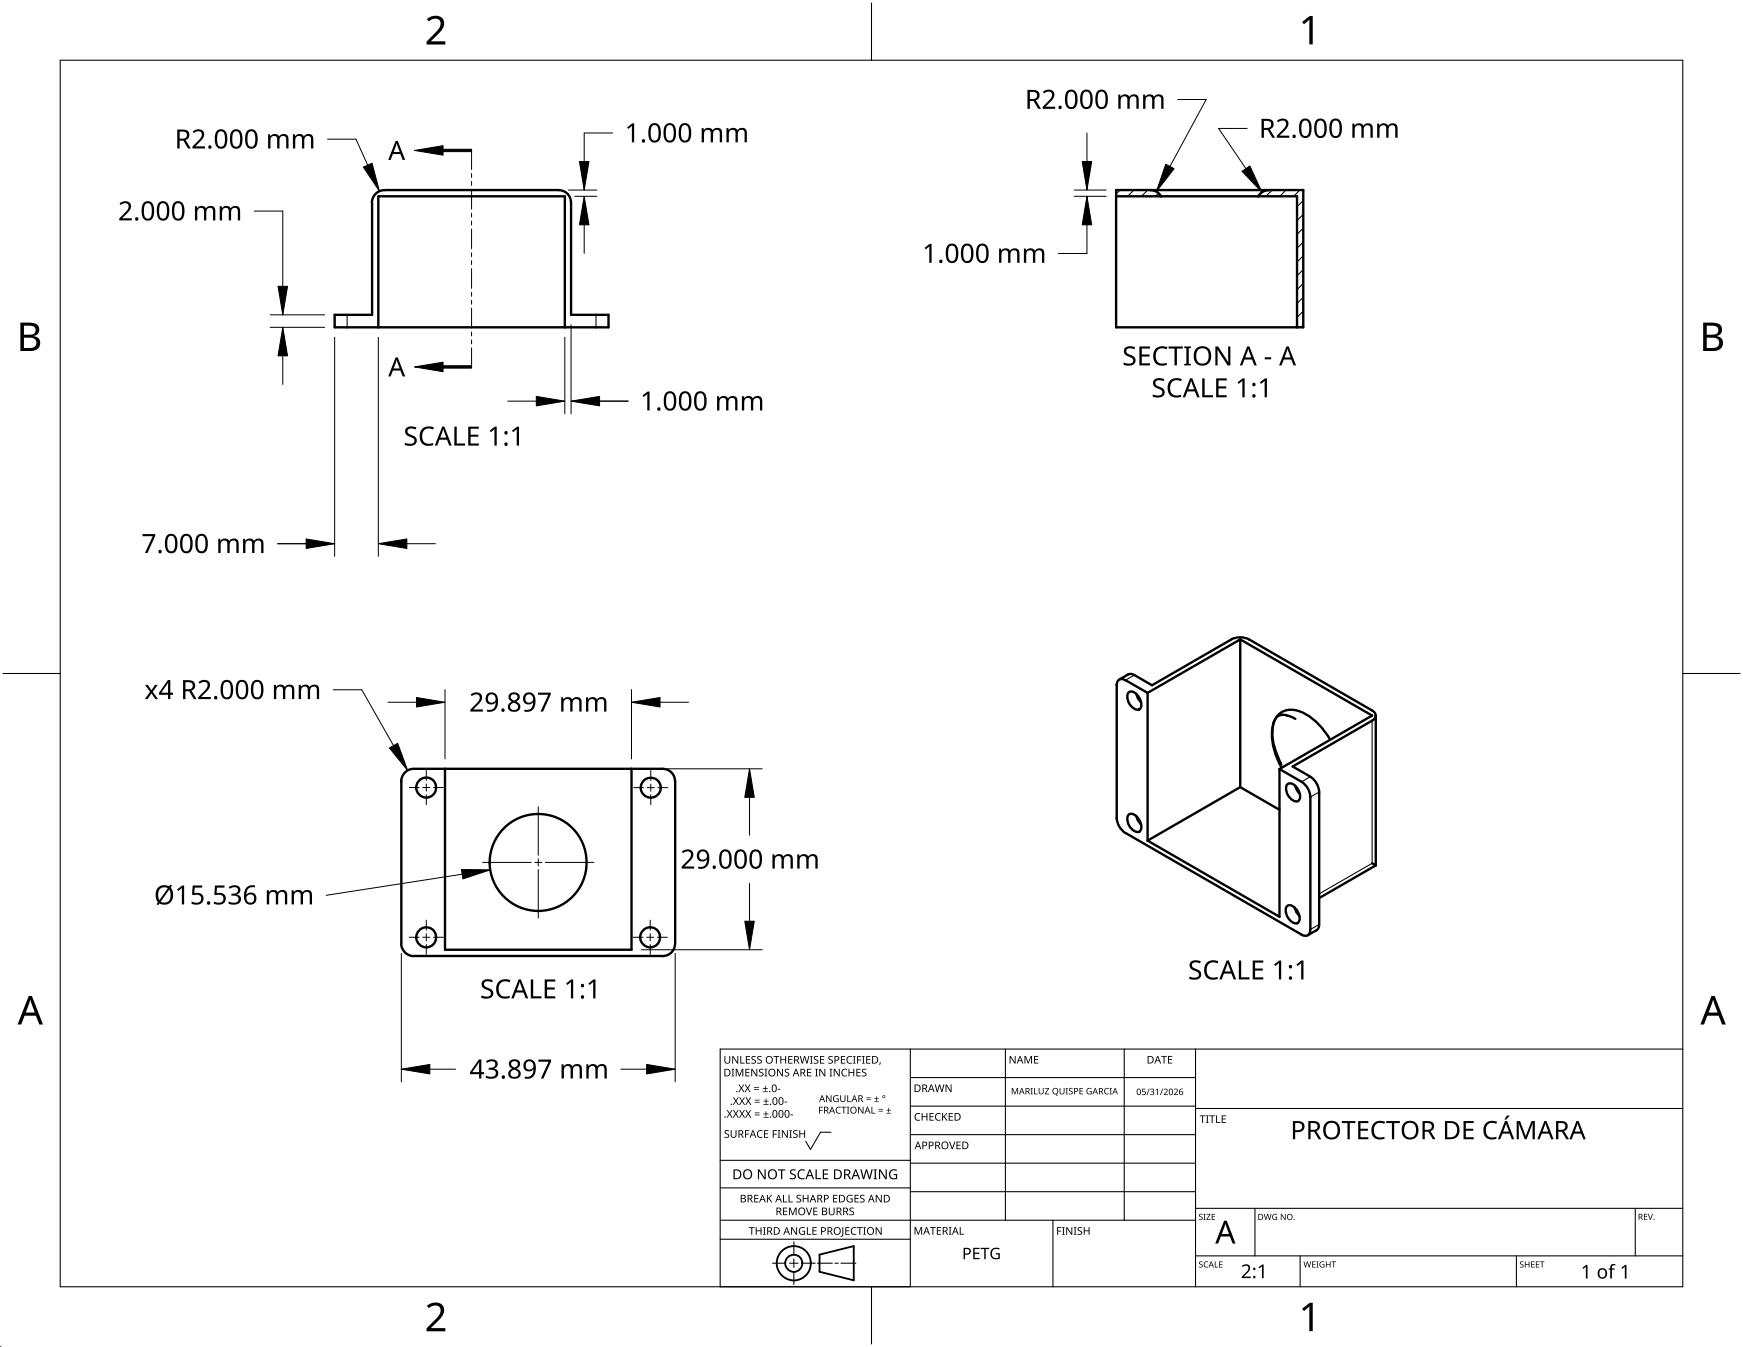
[picture p236: page 1]
