MRCDPLS/FdD_Equipo_07/Proyecto/MóduloMecánico/V3.0/Onshape/Planos/V3_Cubierta para pantalla led.pdf

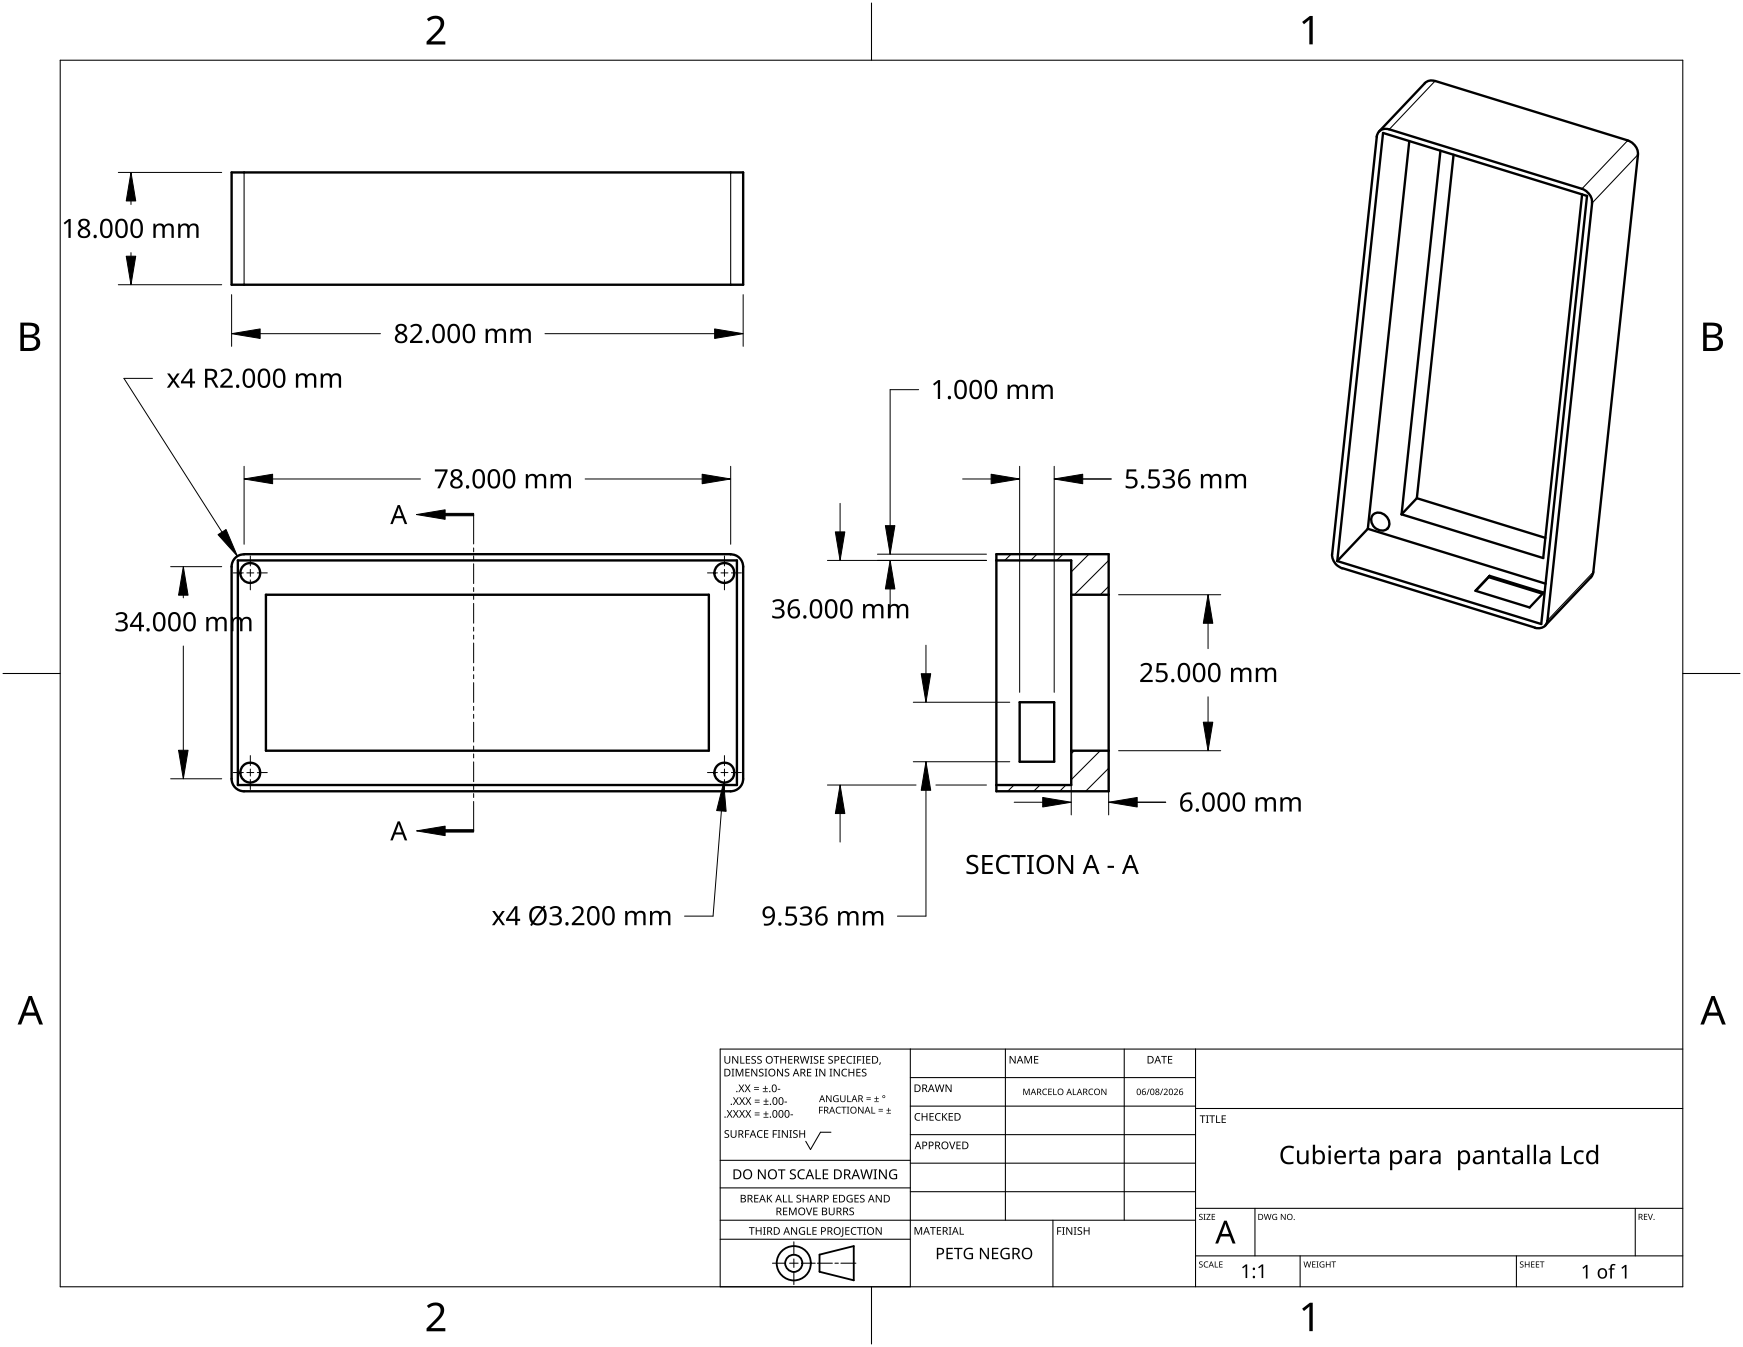
[picture p237: page 1]
