MRCDPLS/FdD_Equipo_07/Proyecto/MóduloMecánico/V3.0/Onshape/Planos/V3_placa 1.pdf

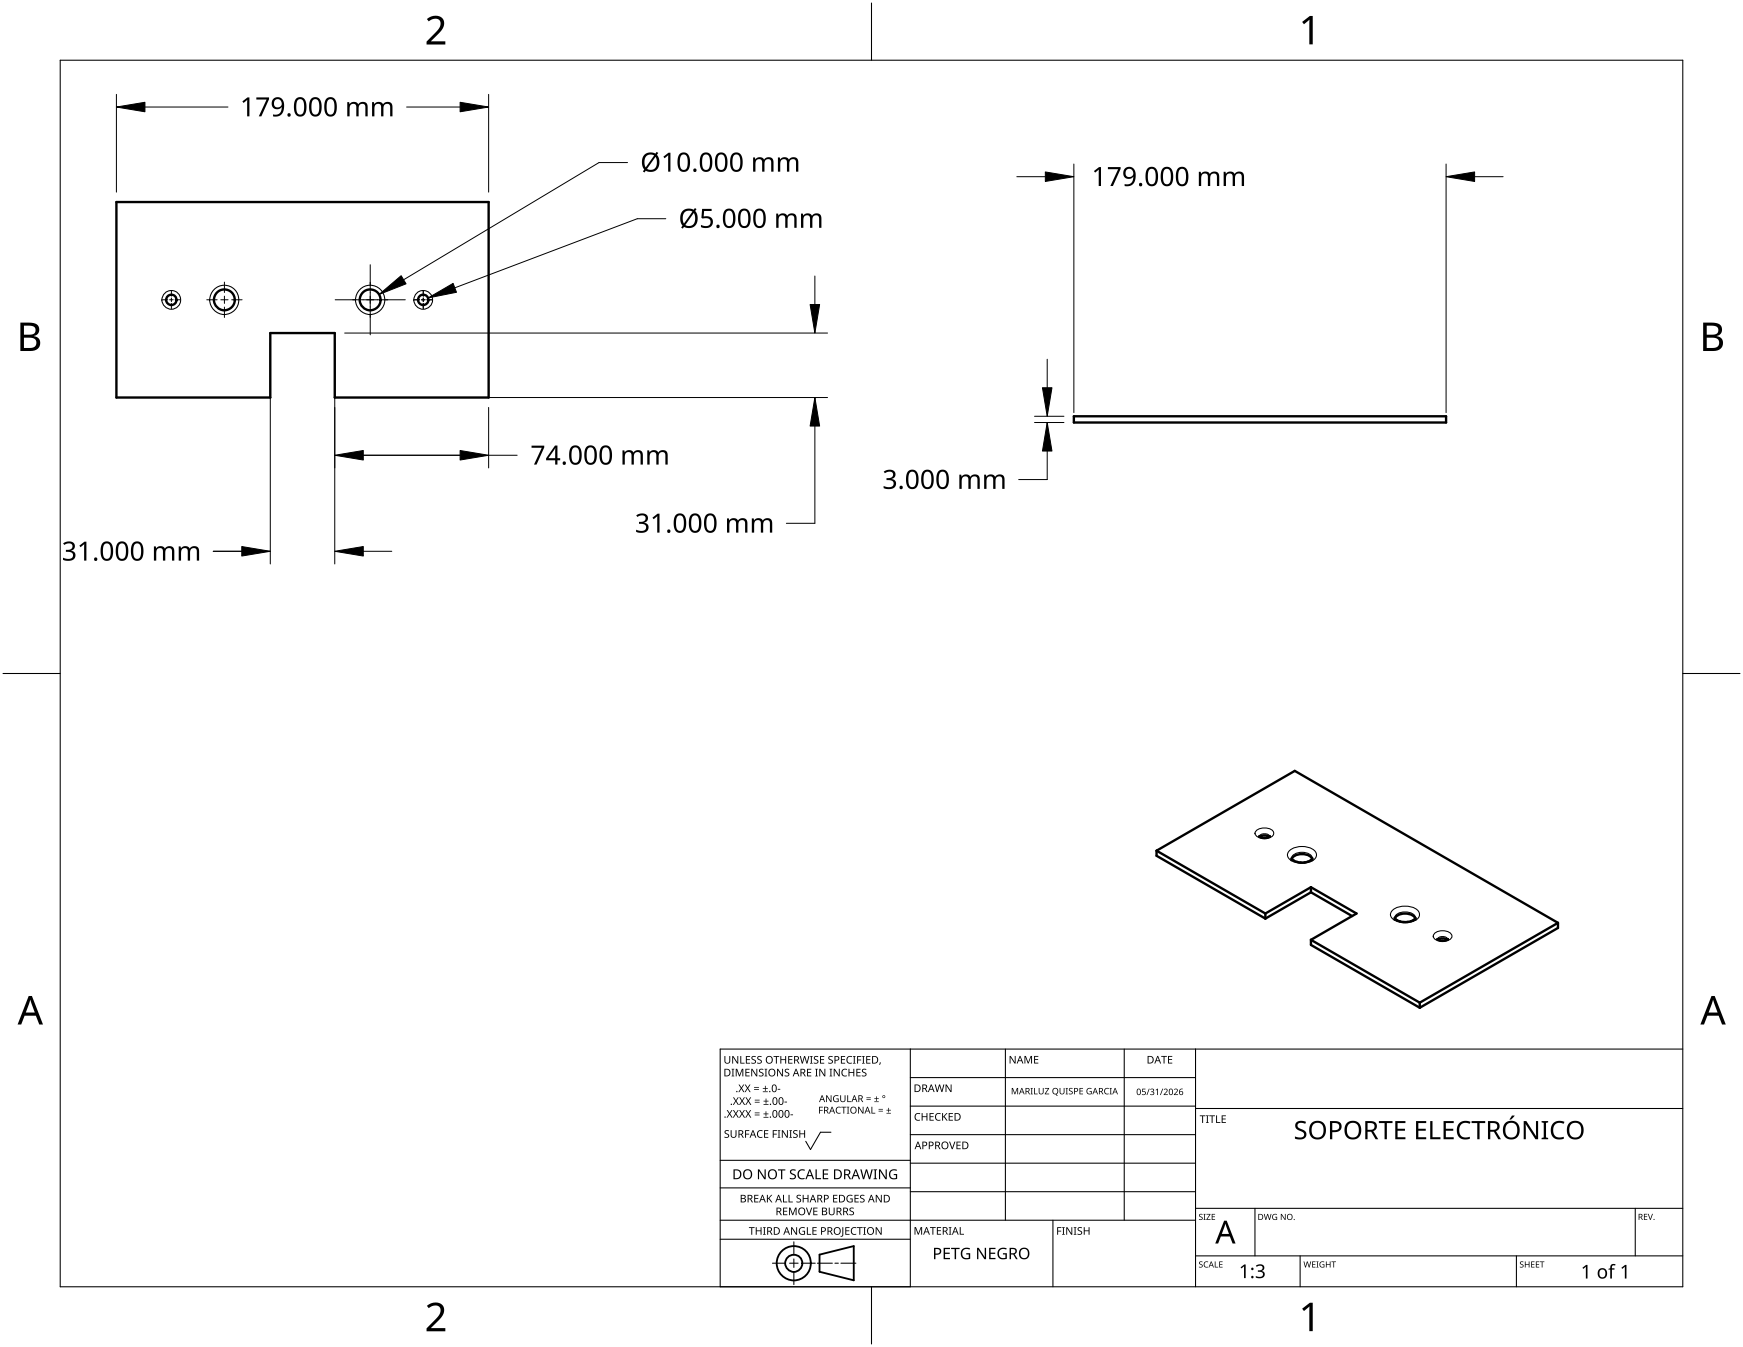
[picture p238: page 1]
