MRCDPLS/FdD_Equipo_07/Proyecto/MóduloMecánico/V3.0/Onshape/Planos/V3_Placa 2.pdf

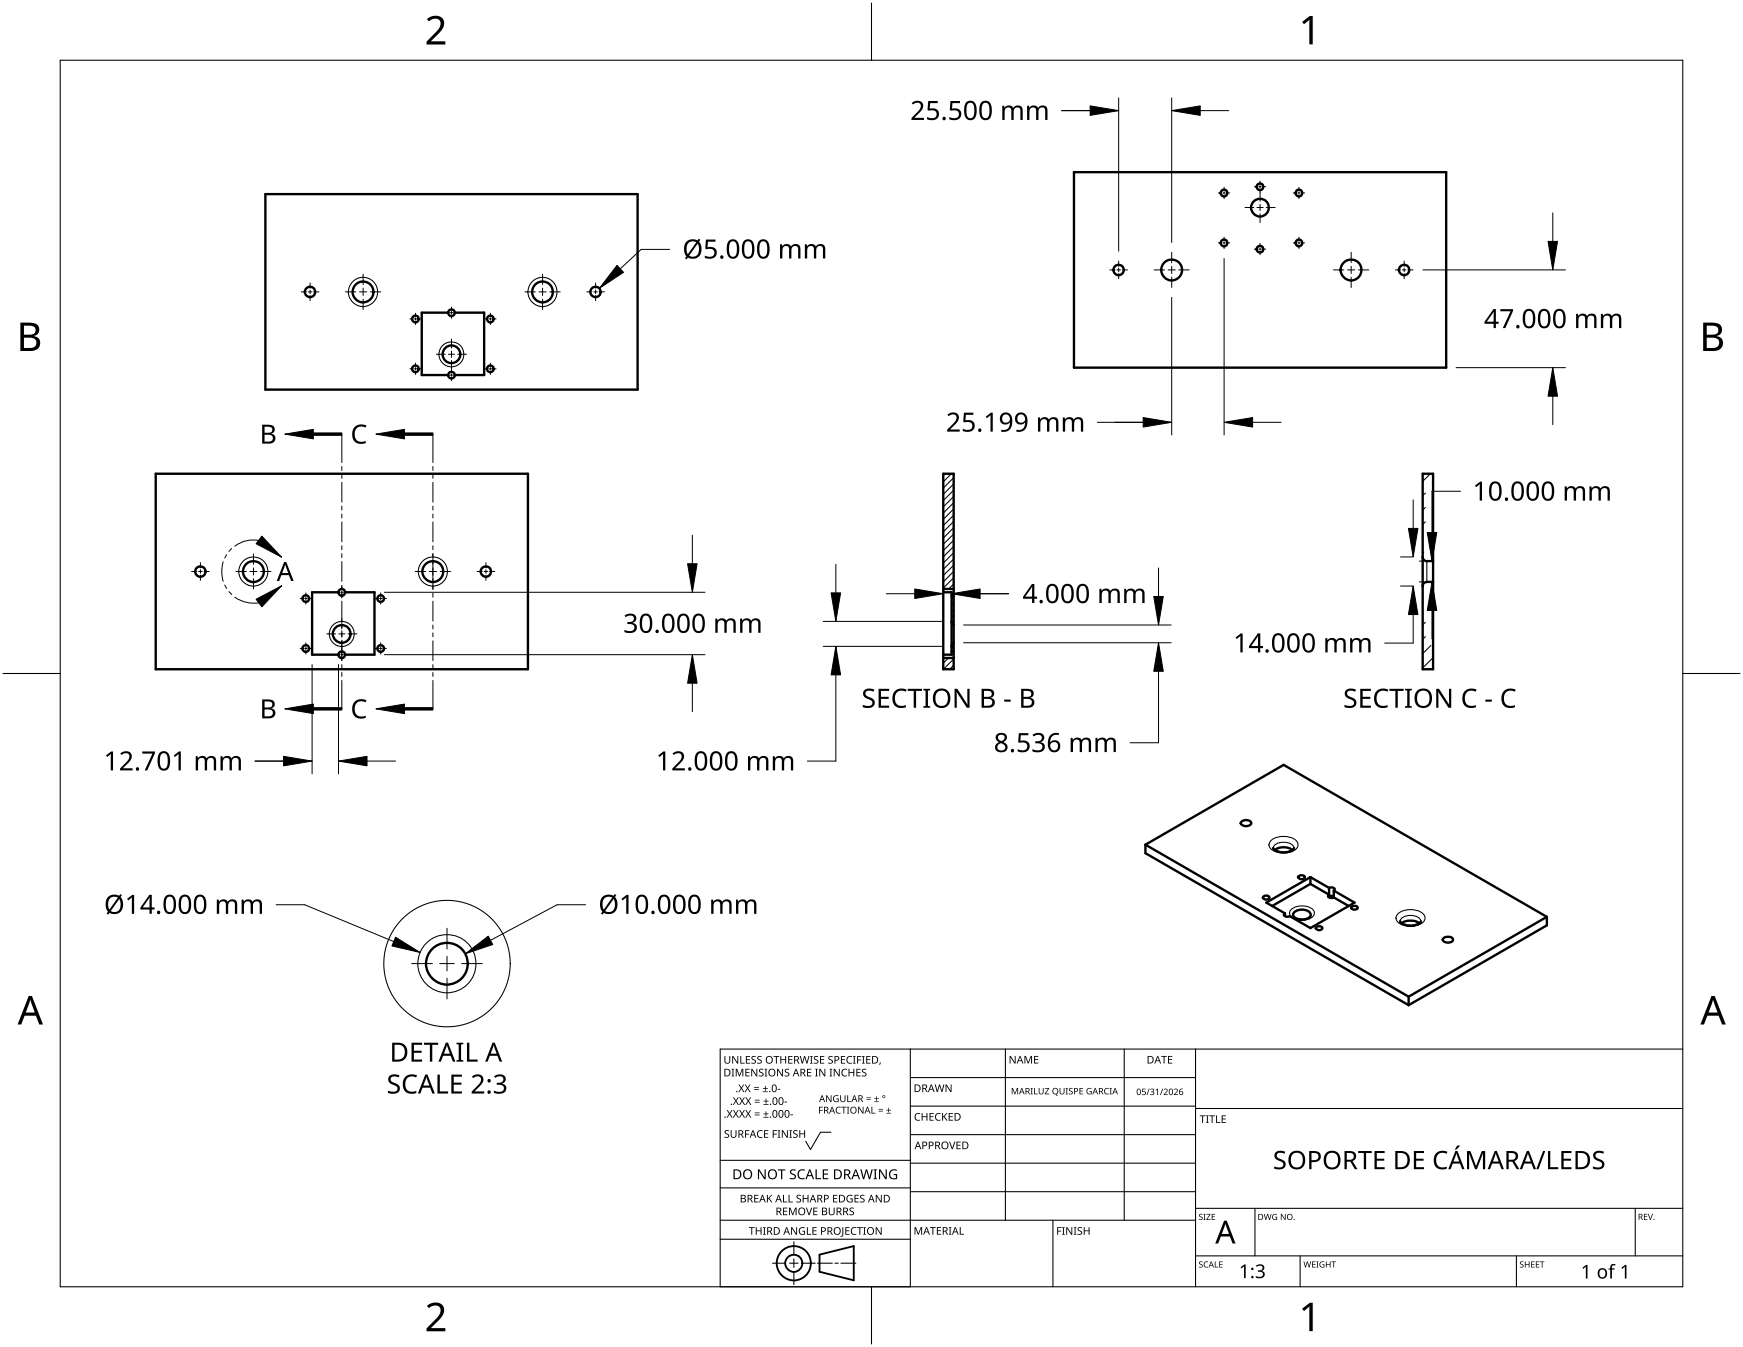
[picture p239: page 1]
