MRCDPLS/FdD_Equipo_07/Proyecto/MóduloMecánico/V3.0/Onshape/Planos/V3_Puerta superior.pdf

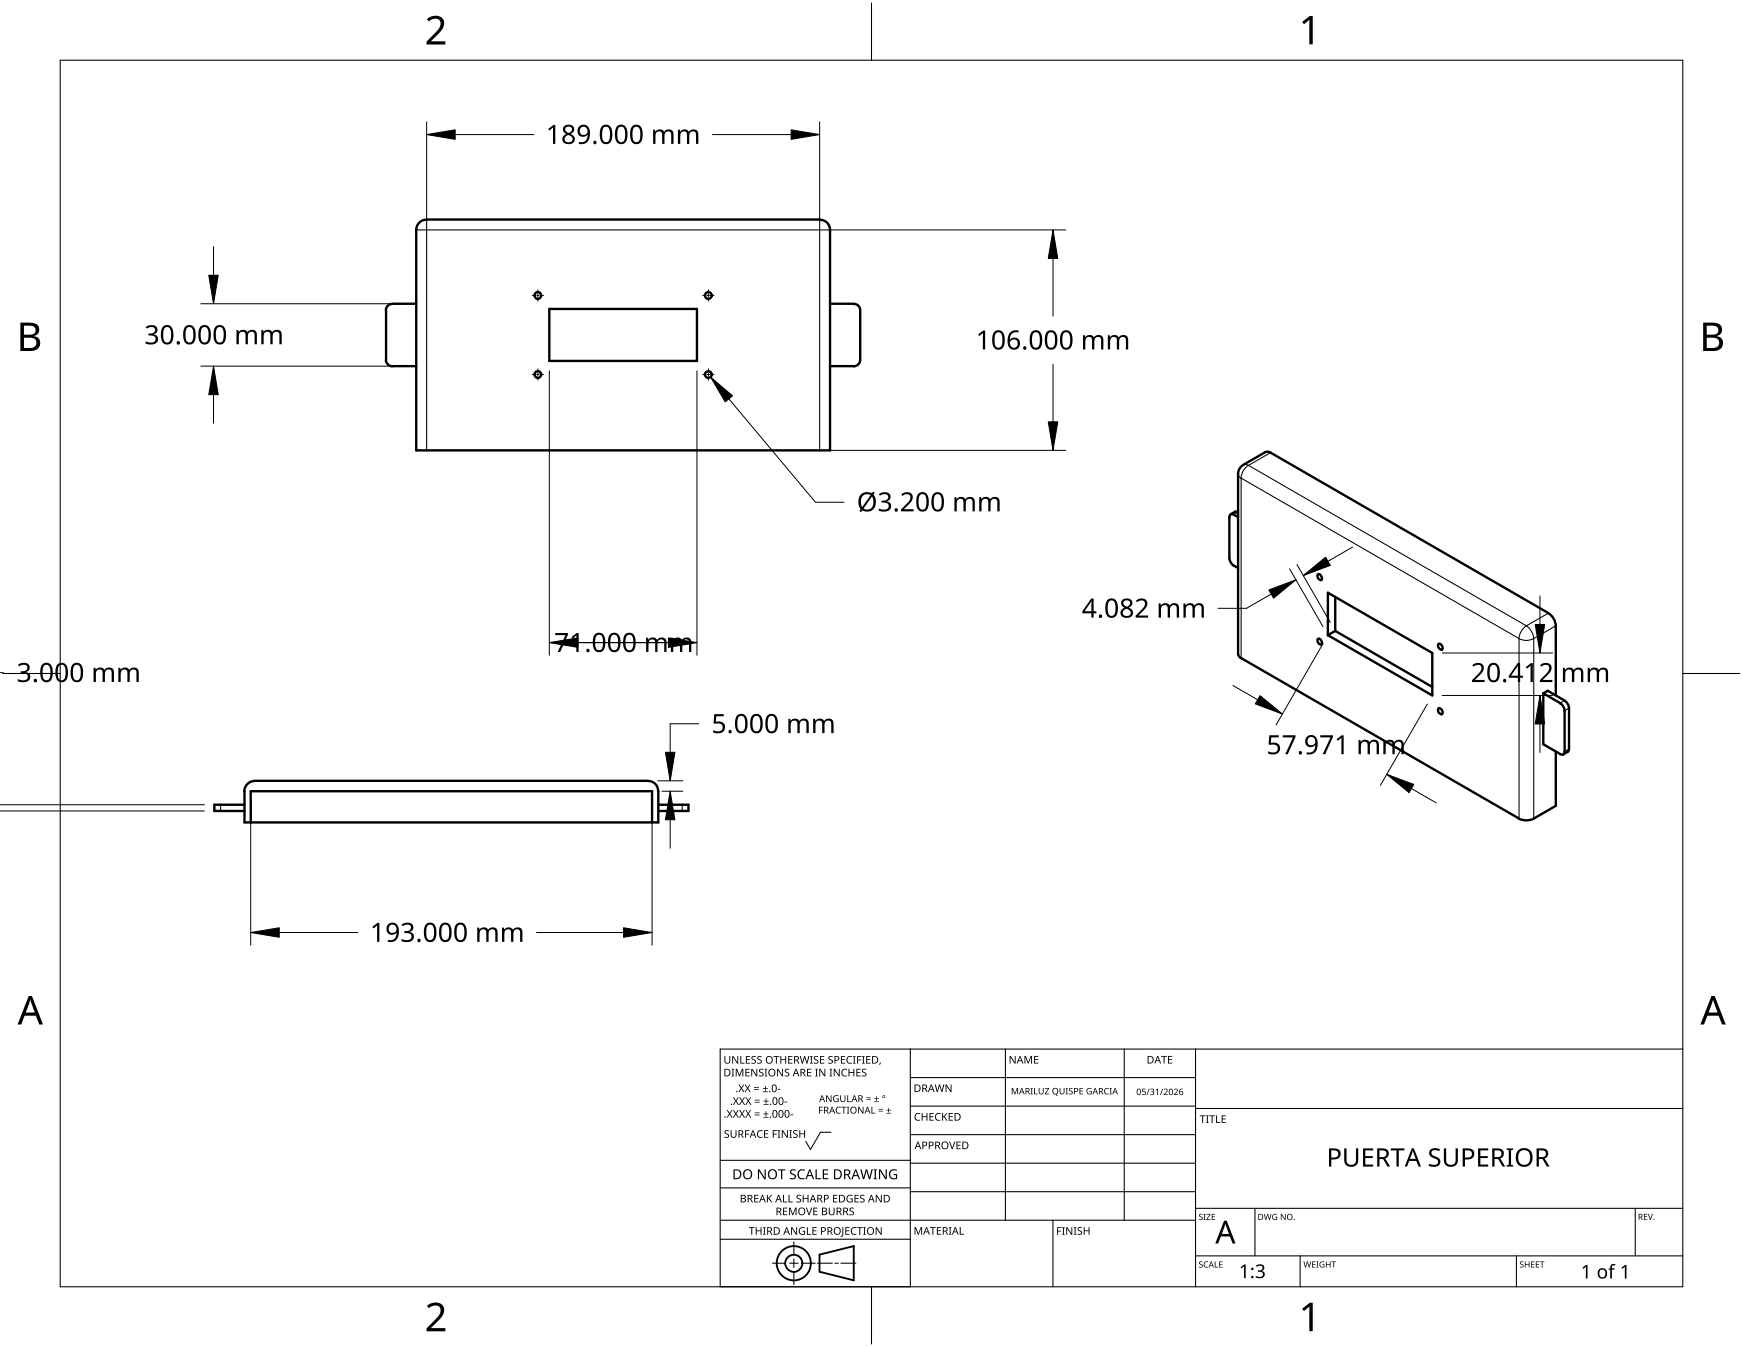
[picture p240: page 1]
