MRCDPLS/FdD_Equipo_07/Proyecto/MóduloMecánico/V3.0/Onshape/Planos/V3_Soporte de lente.pdf

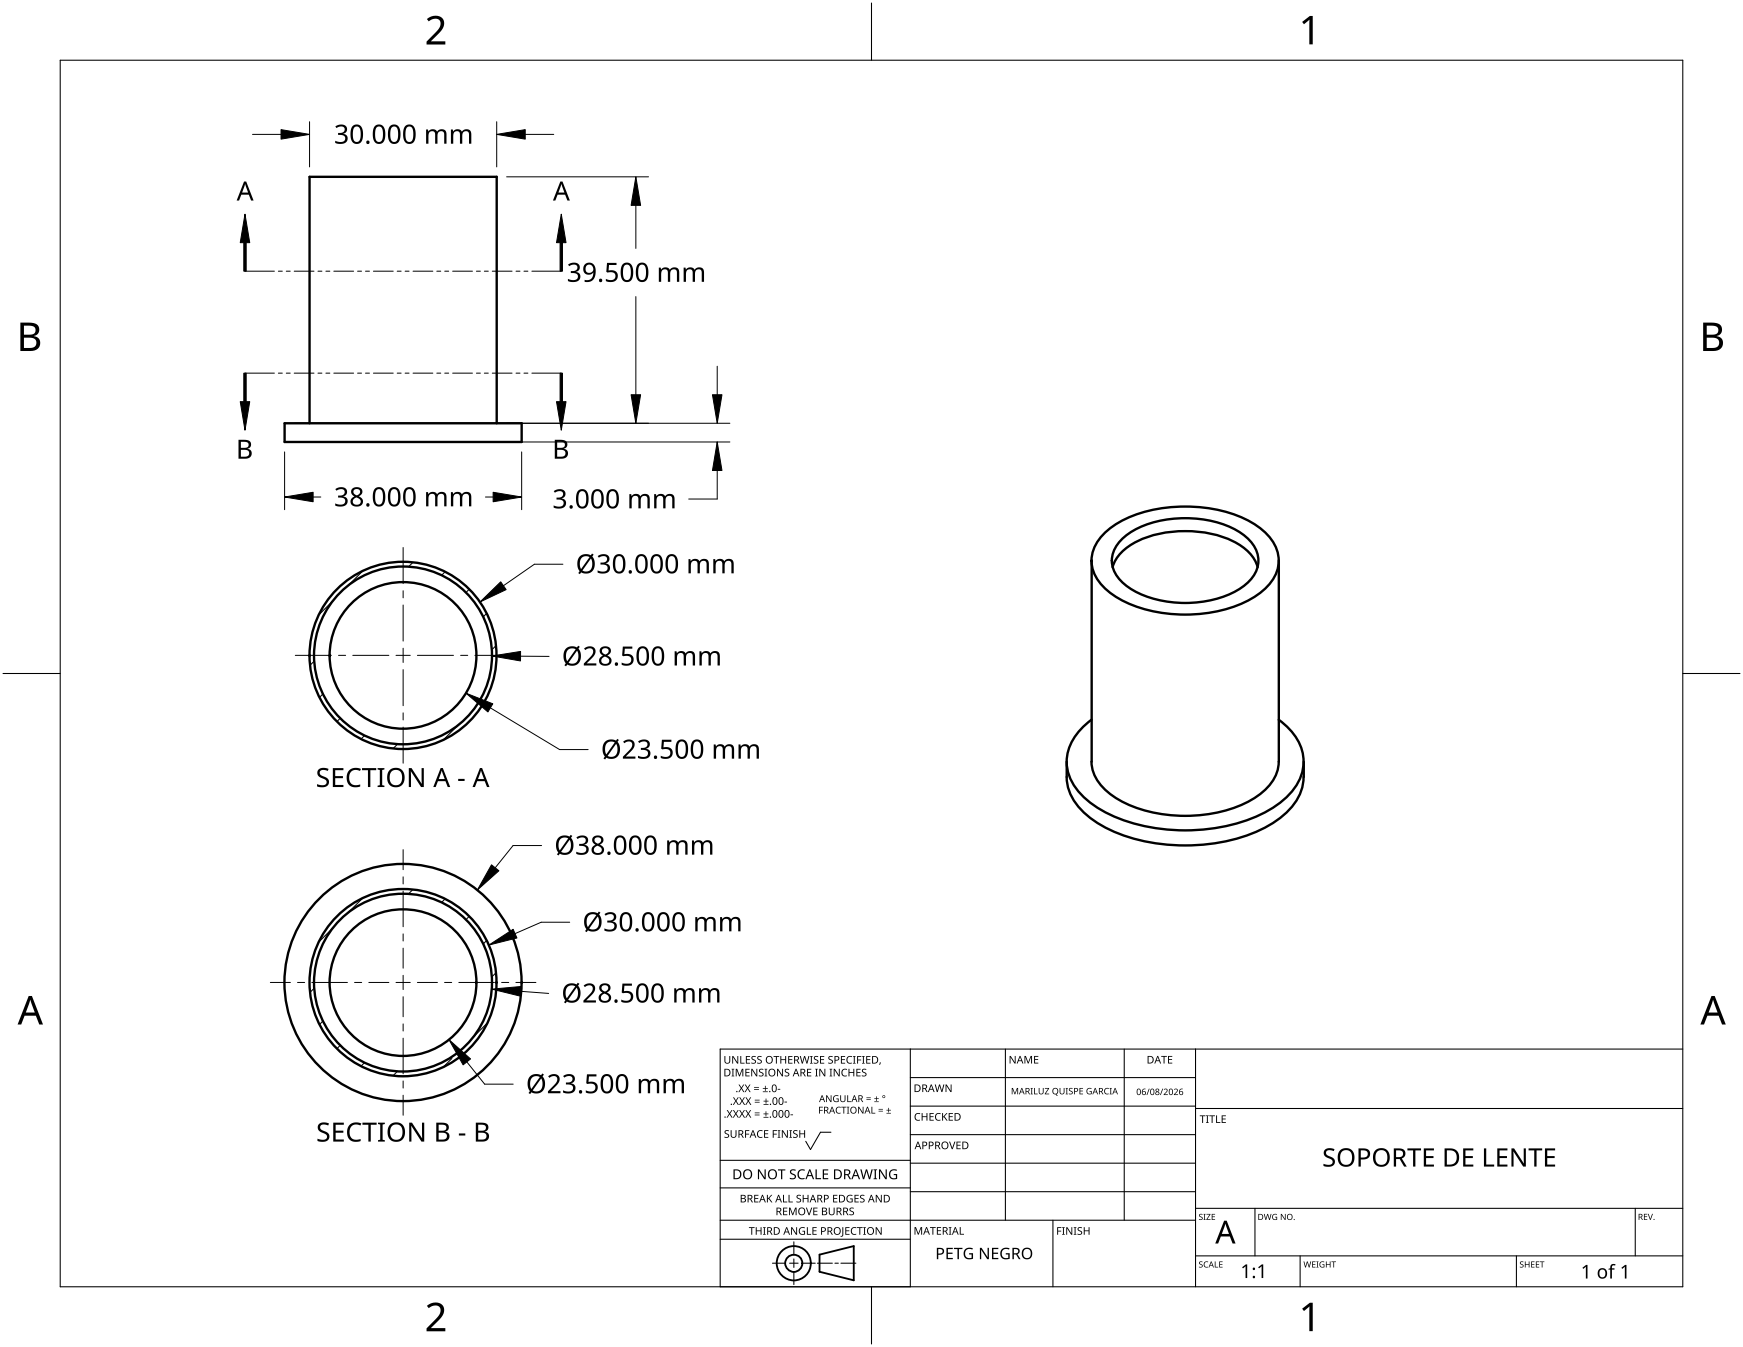
[picture p241: page 1]
