MRCDPLS/FdD_Equipo_07/Proyecto/MóduloMecánico/V3.0/Onshape/Planos/V3_Soporte de placa.pdf

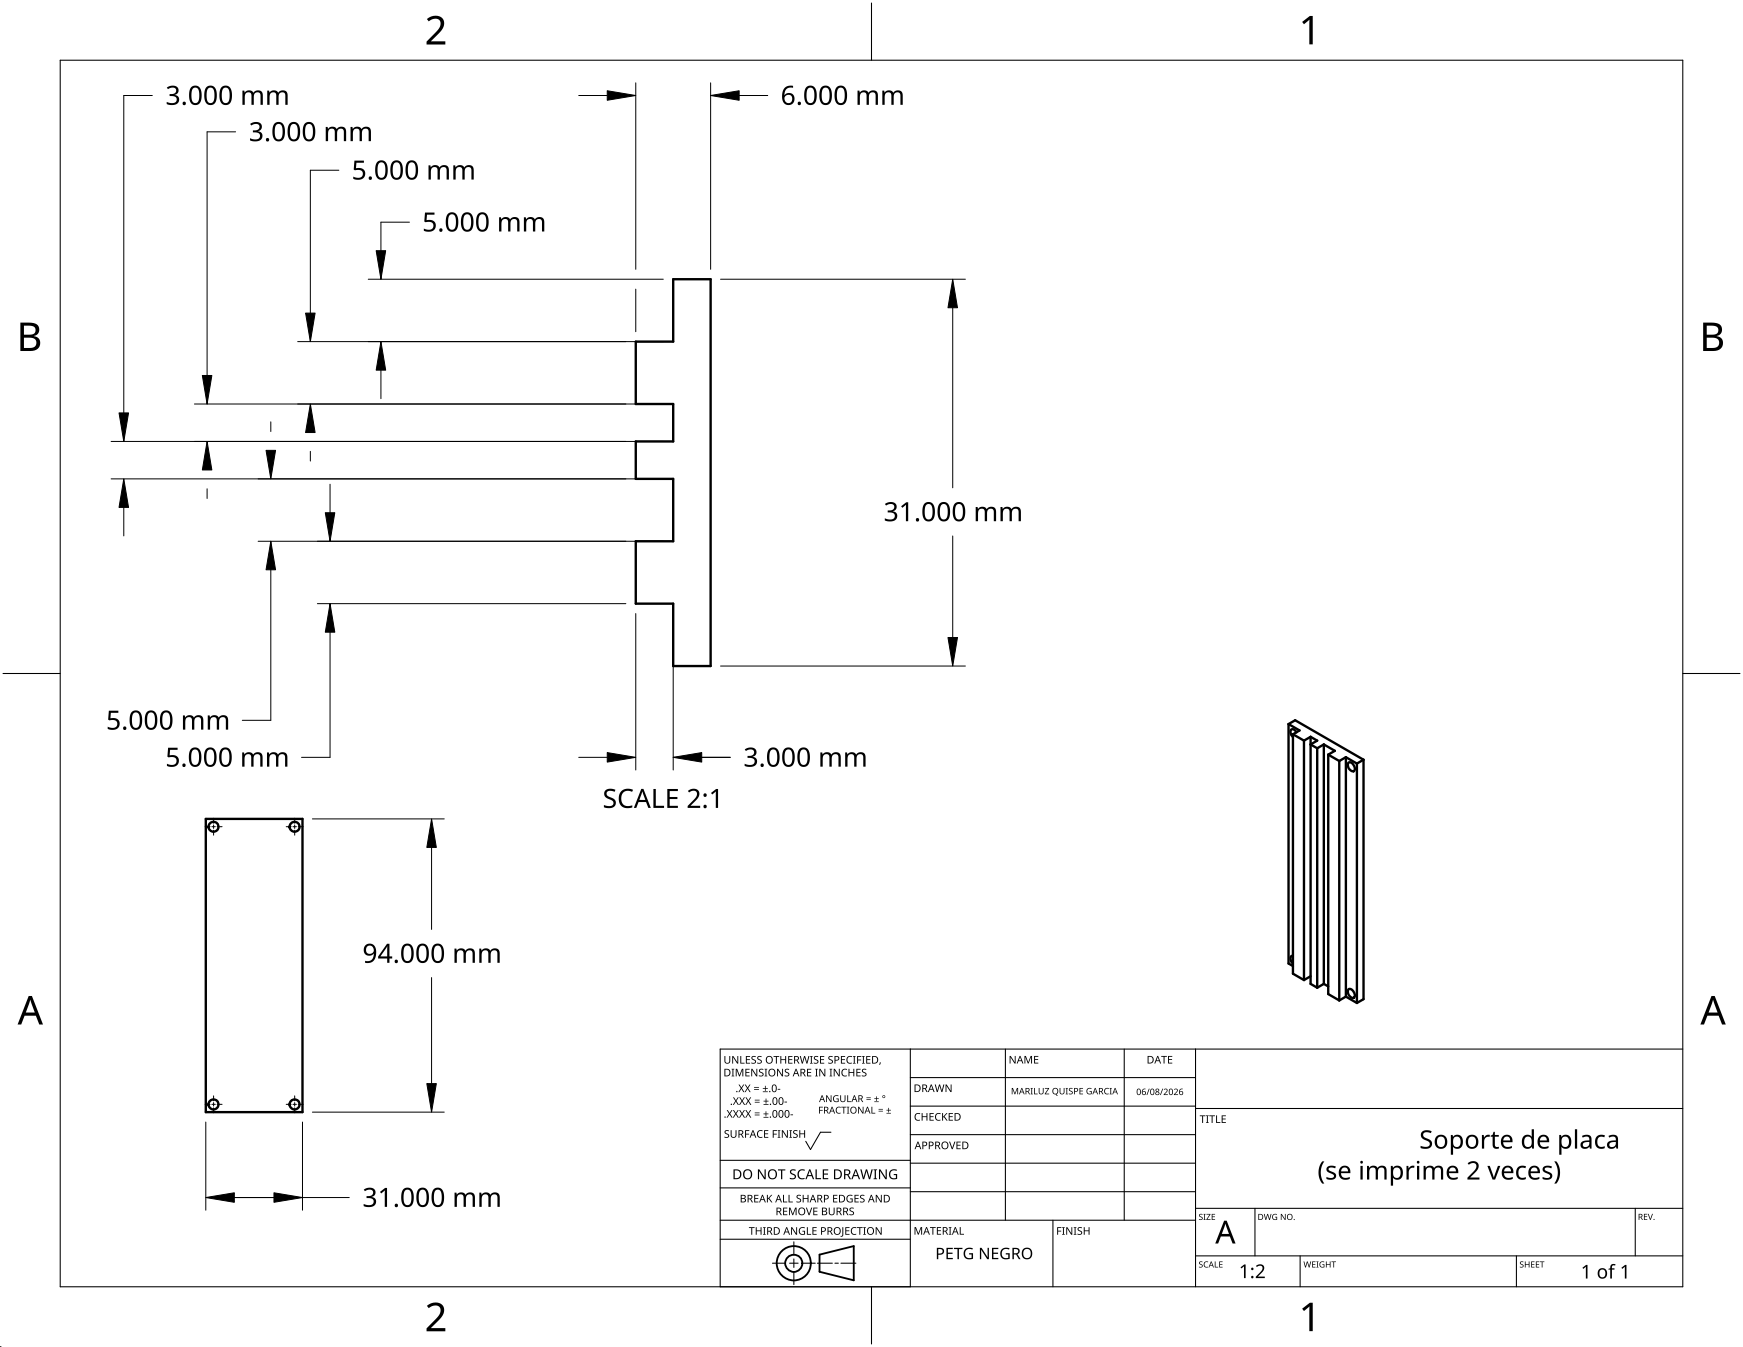
[picture p242: page 1]
