MRCDPLS/FdD_Equipo_07/Proyecto/MóduloMecánico/V3.0/Onshape/Planos/V3_Soporte para powerbank.pdf

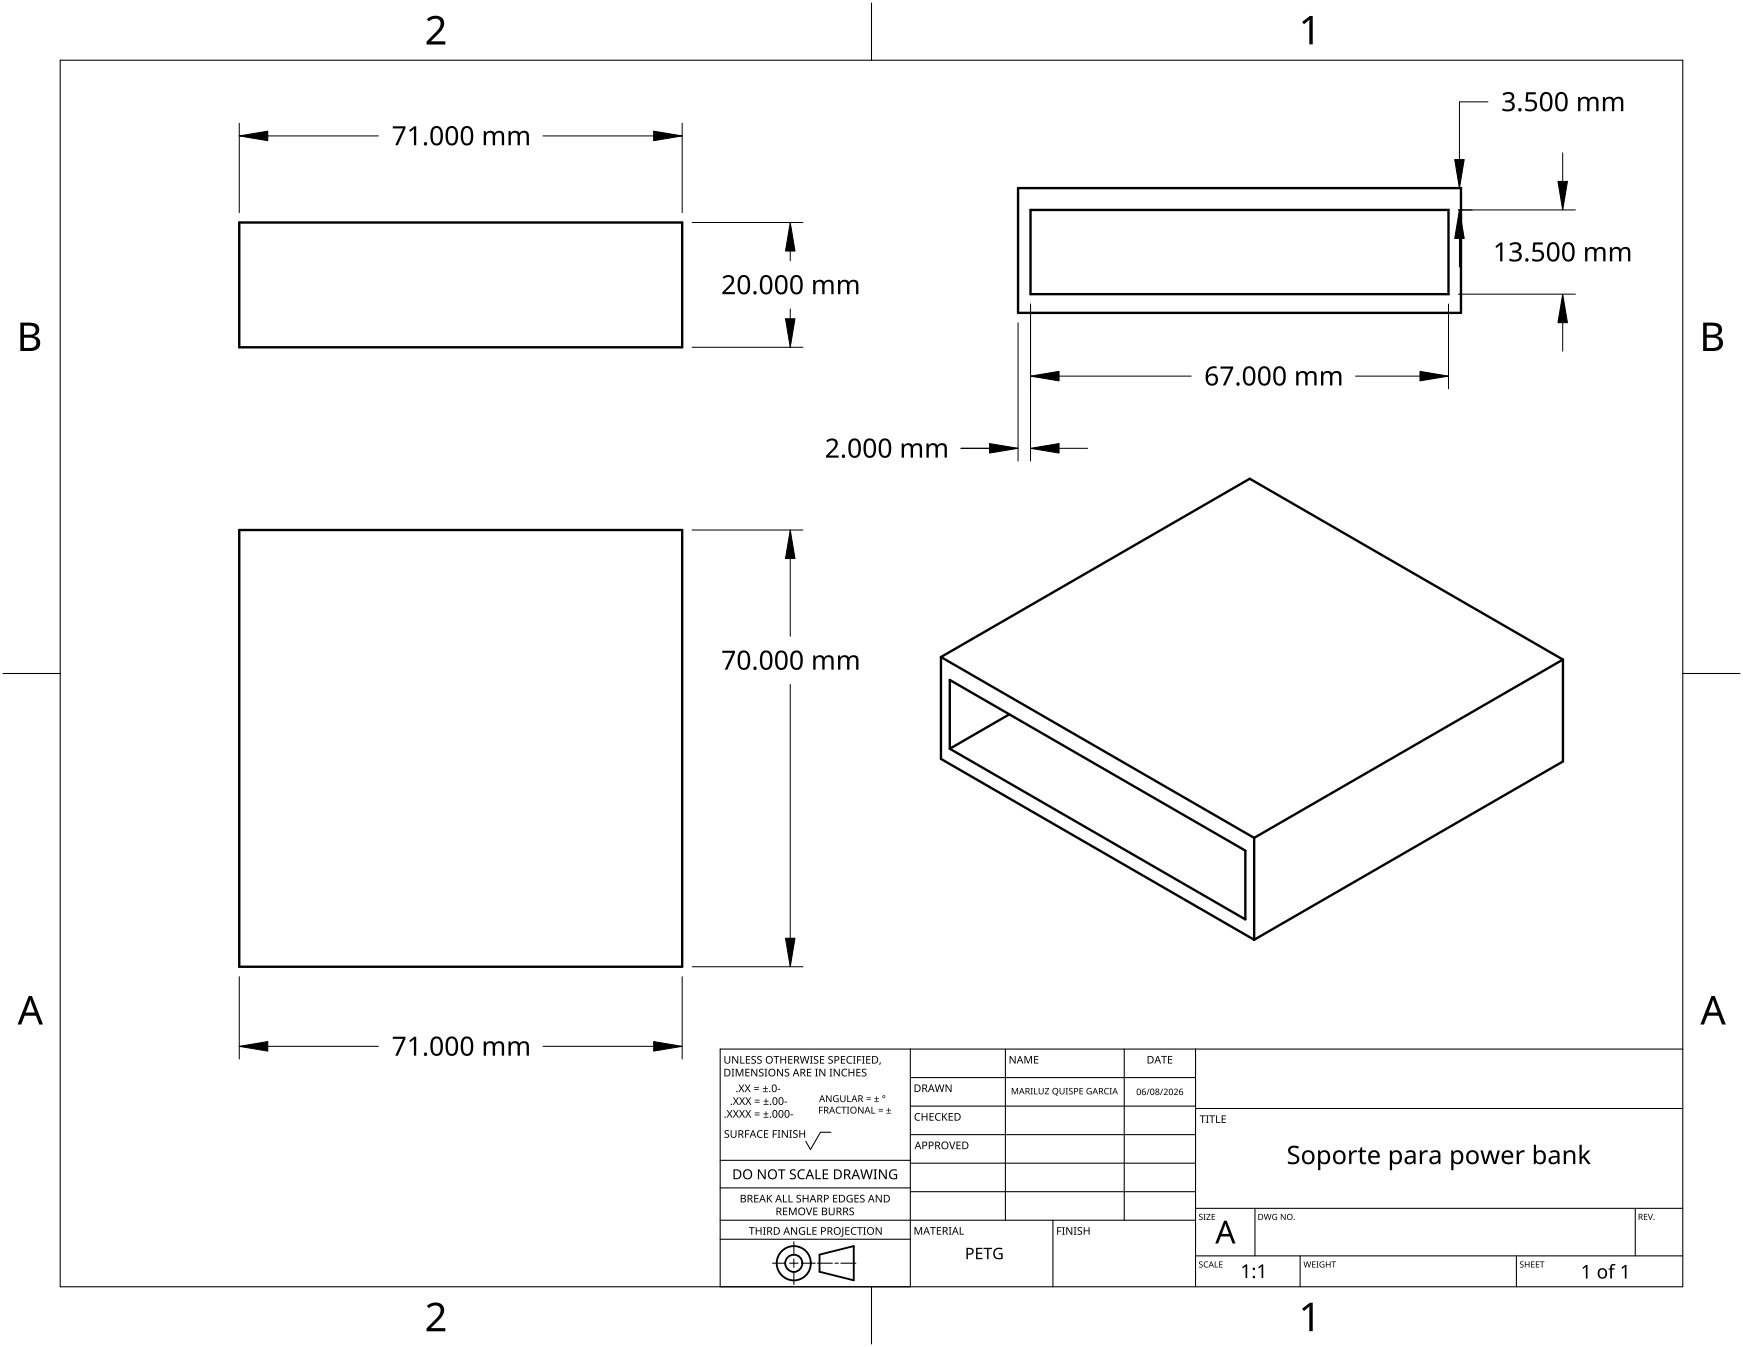
[picture p243: page 1]
