MRCDPLS/FdD_Equipo_07/Proyecto/MóduloMecánico/V3.0/Onshape/Planos/Borde_lat1_puerta_sup.pdf

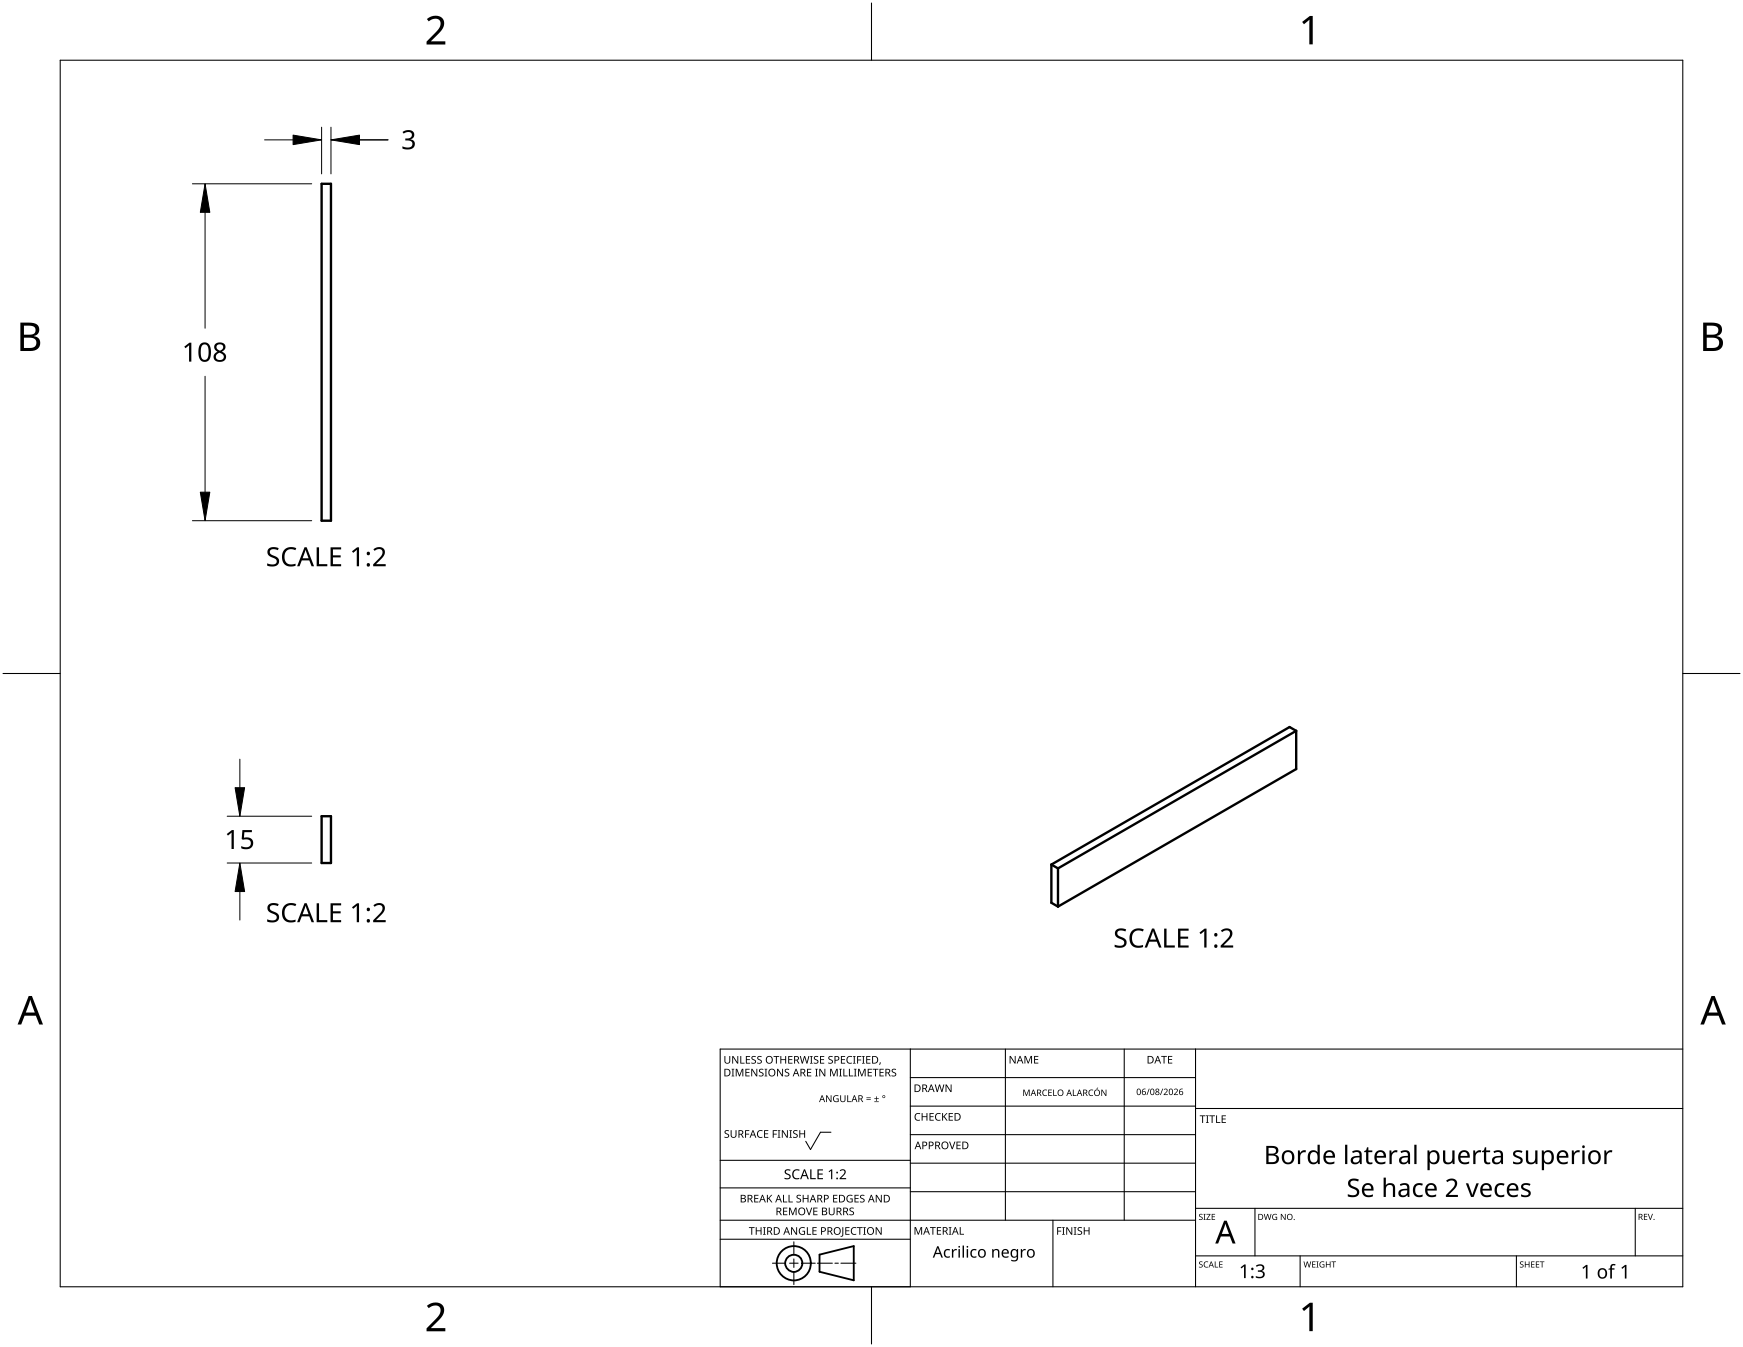
[picture p244: page 1]
