MRCDPLS/FdD_Equipo_07/Proyecto/MóduloMecánico/V3.0/Onshape/Planos/Borde_puerta_inf_1.pdf

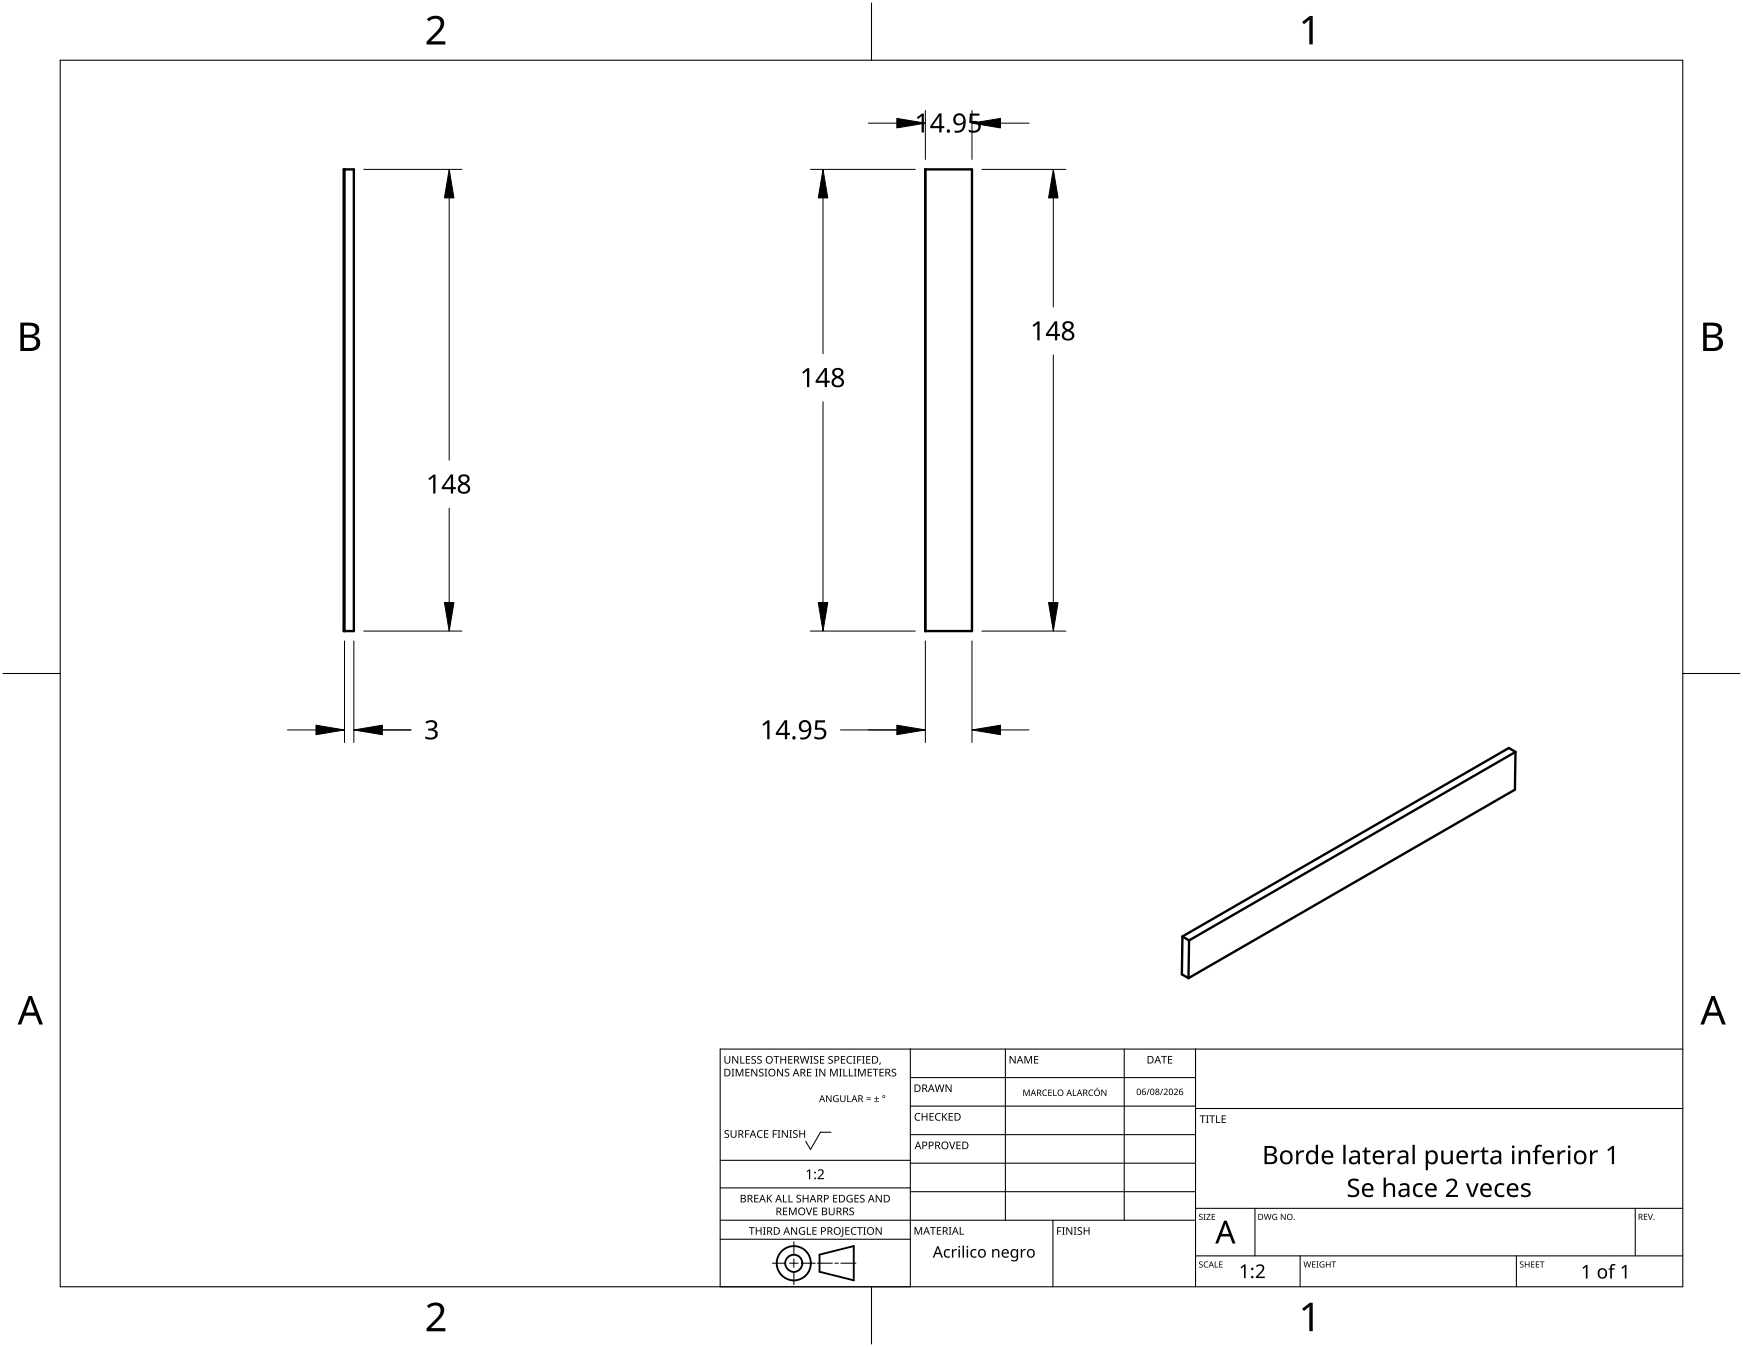
[picture p245: page 1]
