MRCDPLS/FdD_Equipo_07/Proyecto/MóduloMecánico/V3.0/Onshape/Planos/Borde_sup_puerta_sup.pdf

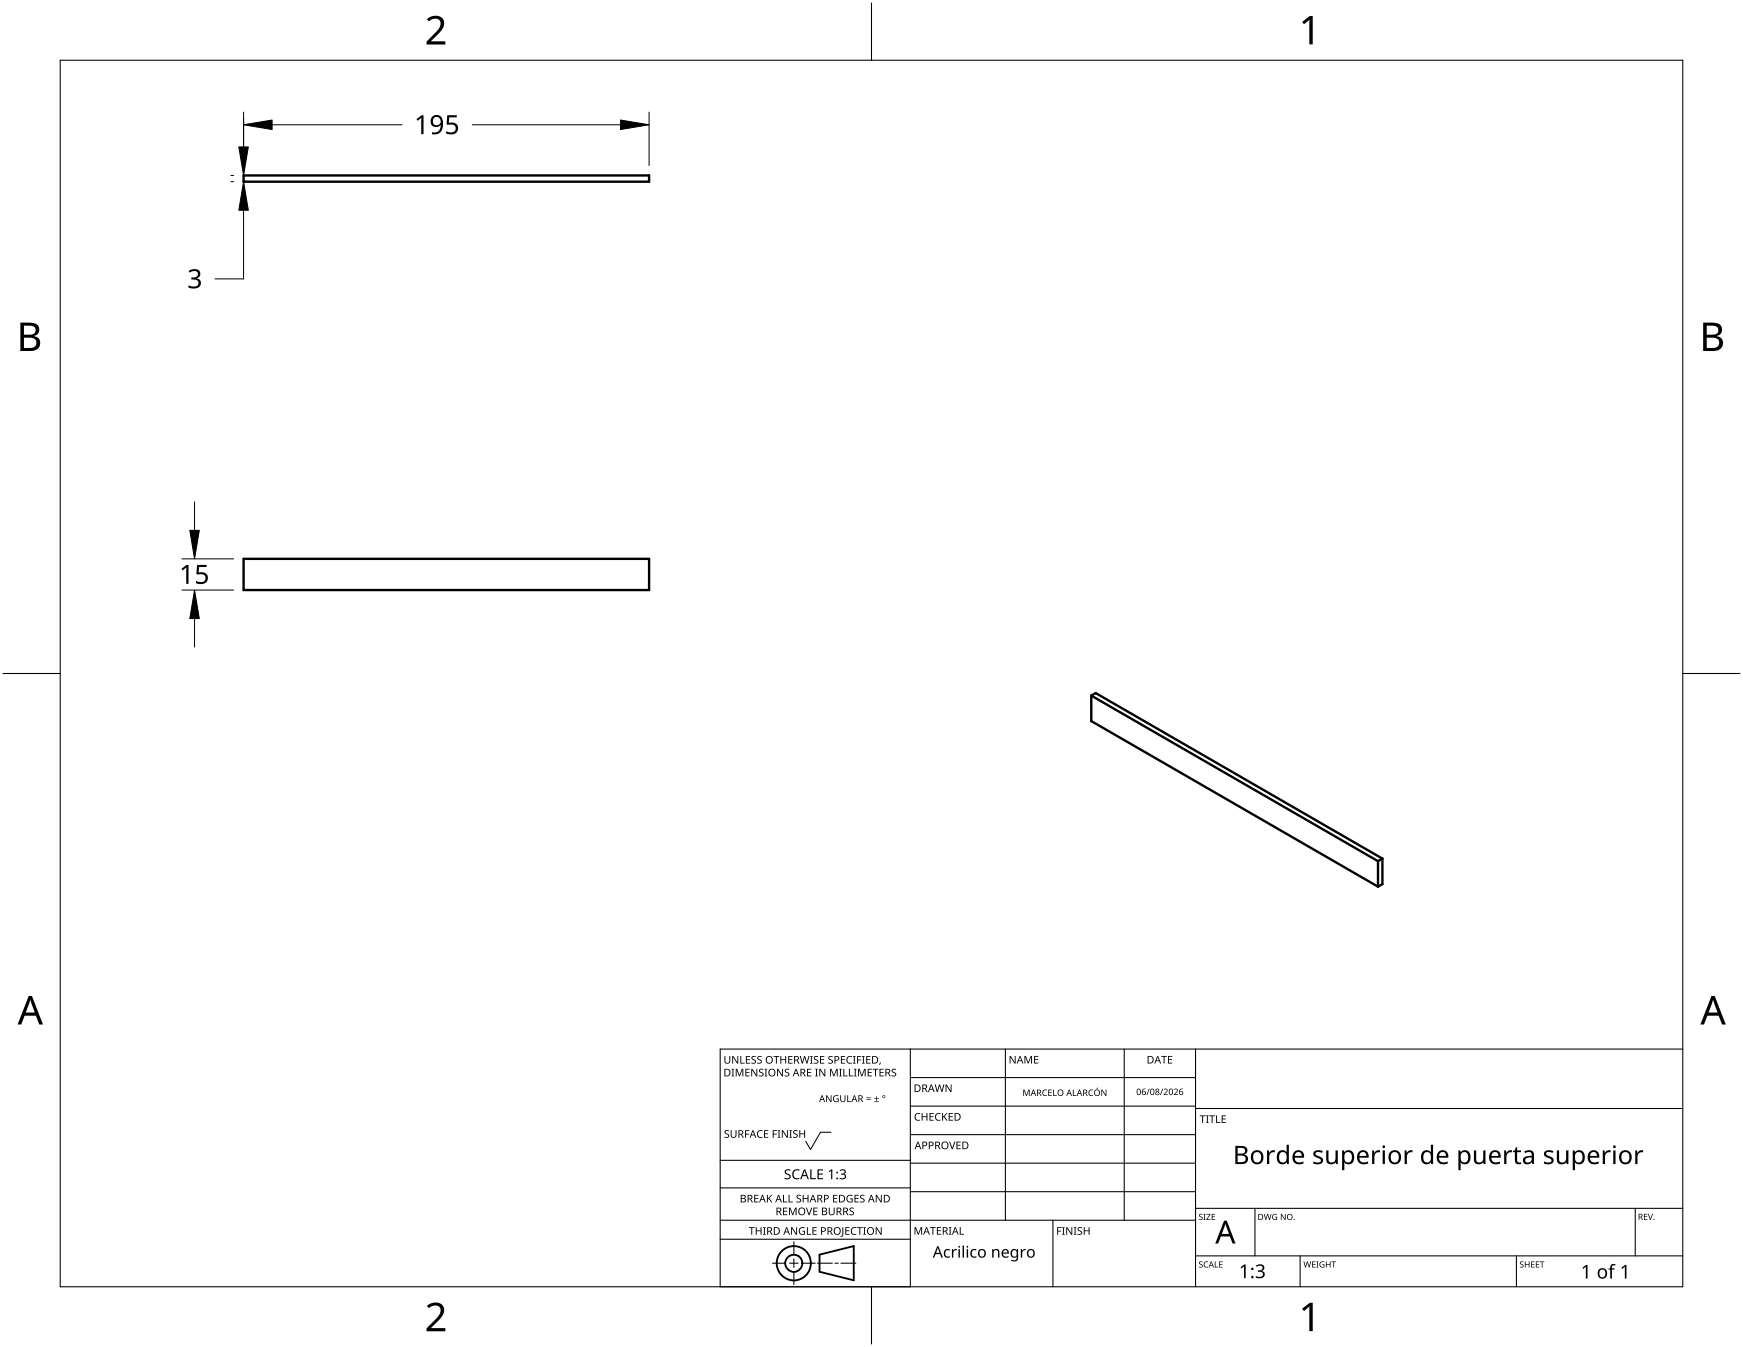
[picture p246: page 1]
