MRCDPLS/FdD_Equipo_07/Proyecto/MóduloMecánico/V3.0/Onshape/Planos/Fondo_drawing.pdf

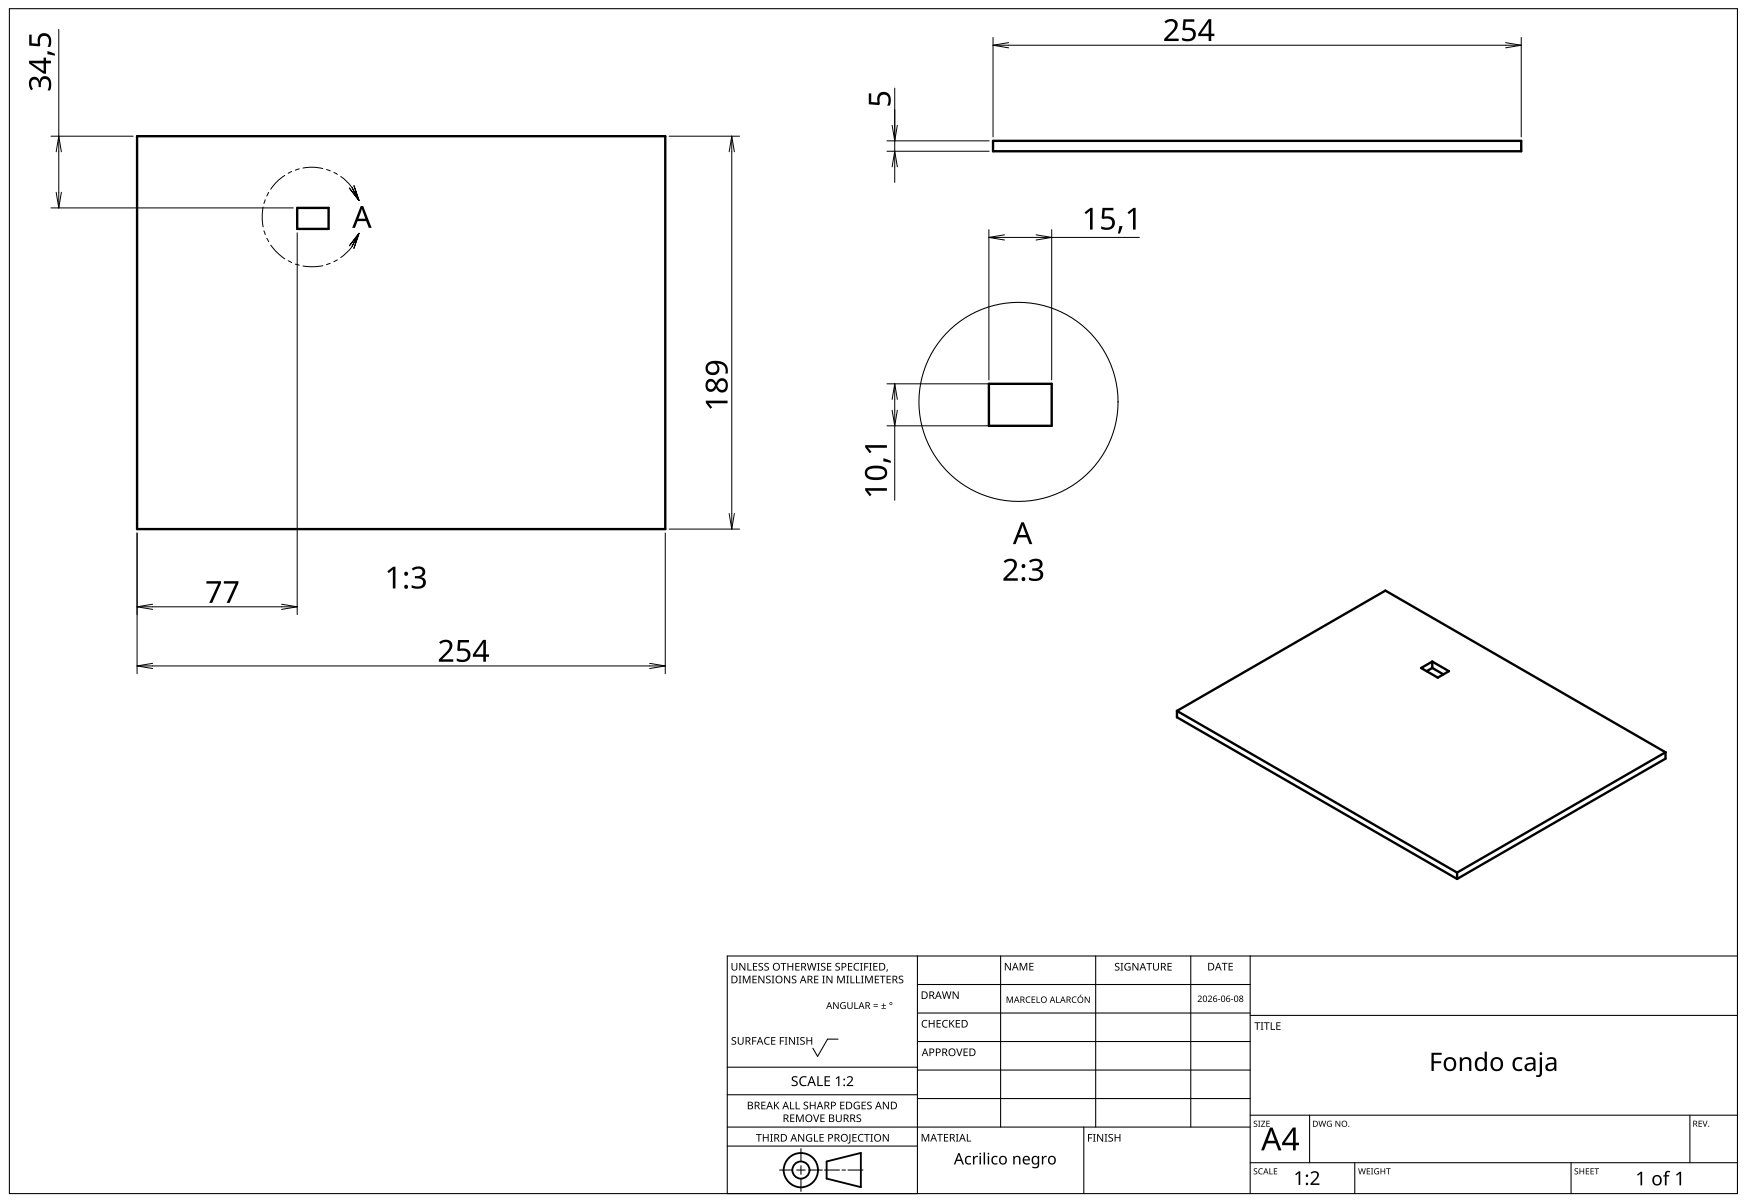
[picture p247: page 1]
