MRCDPLS/FdD_Equipo_07/Proyecto/MóduloMecánico/V3.0/Onshape/Planos/Lengueta 1.pdf

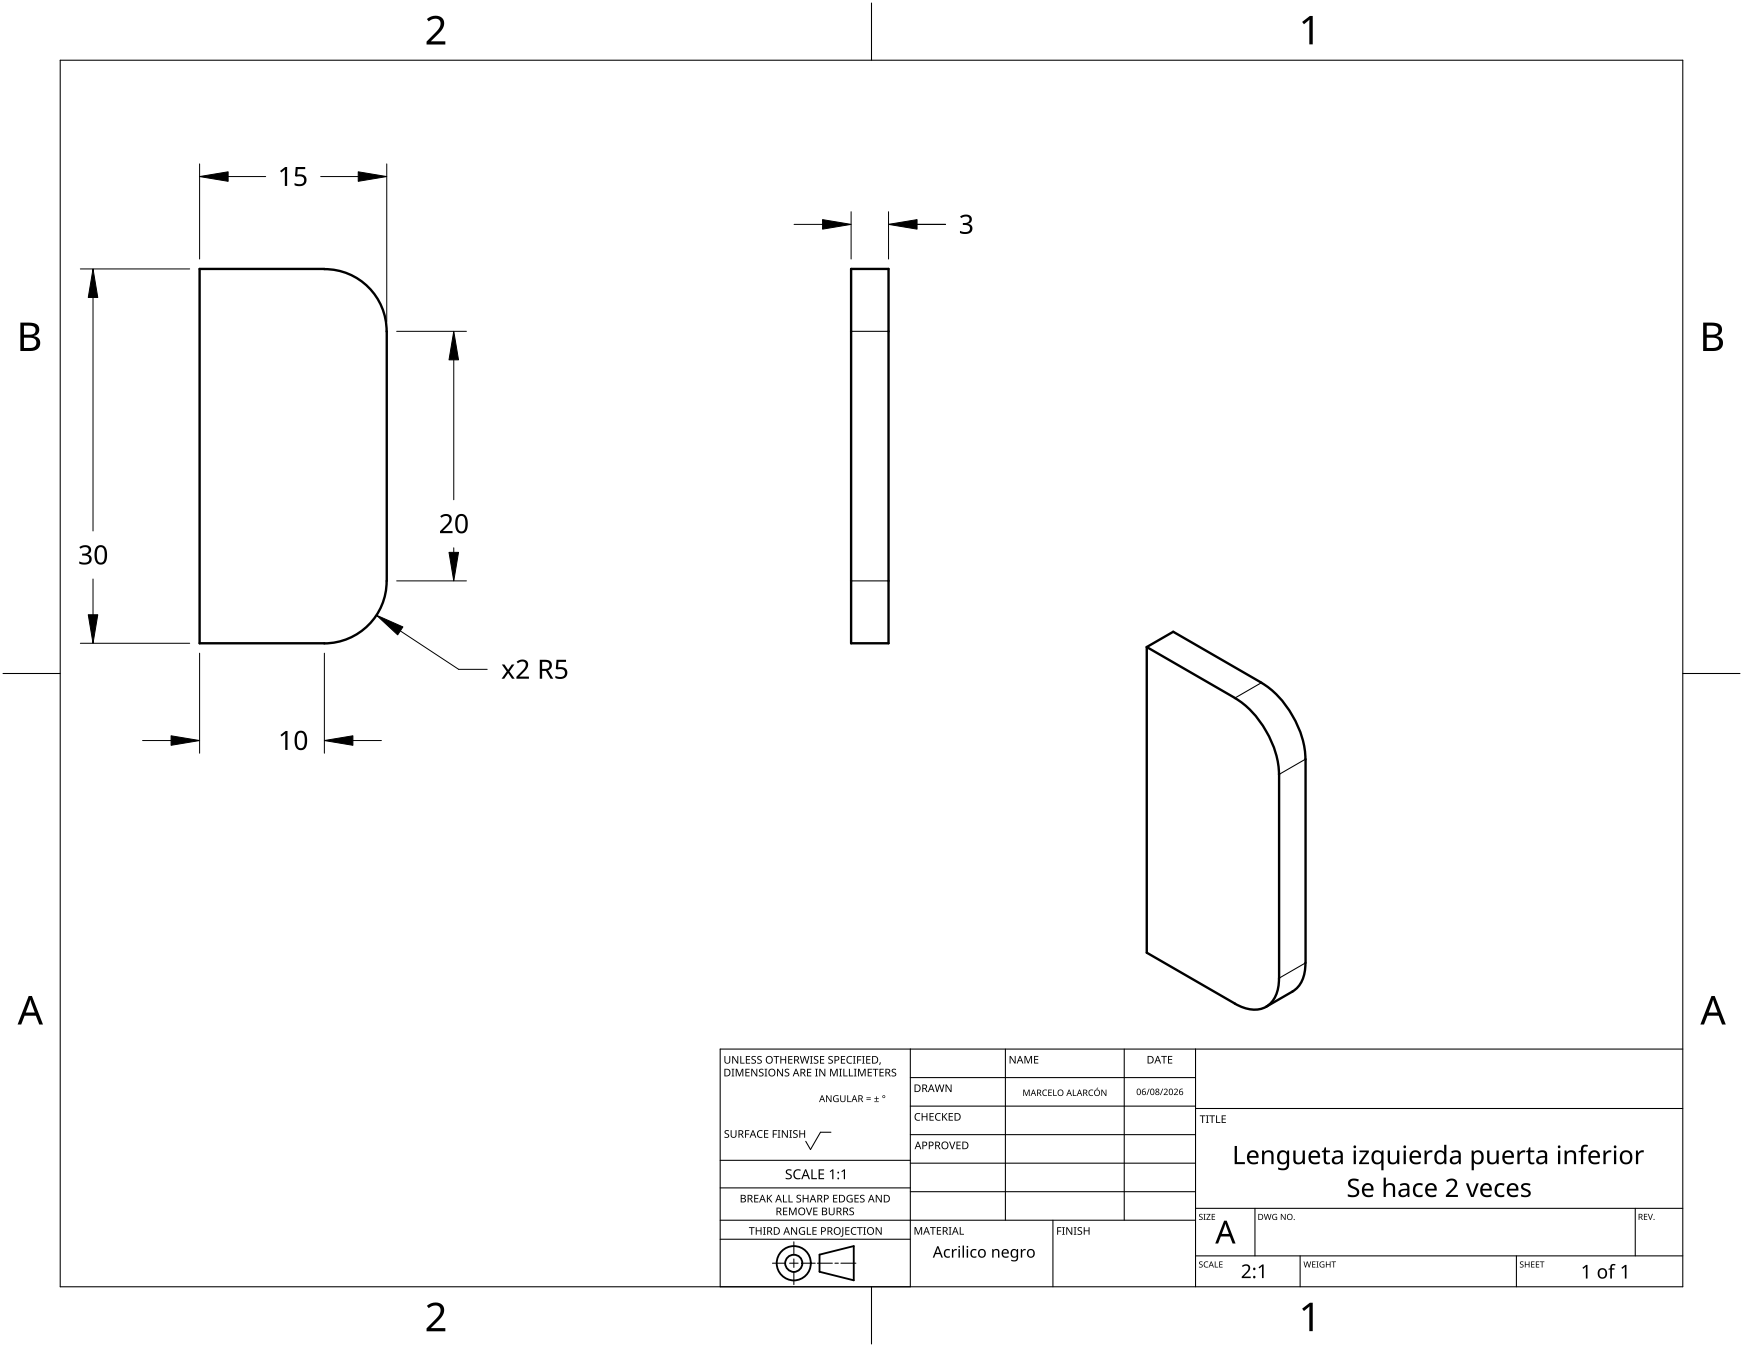
[picture p248: page 1]
