MRCDPLS/FdD_Equipo_07/Proyecto/MóduloMecánico/V3.0/Onshape/Planos/Pared superior e inf.pdf

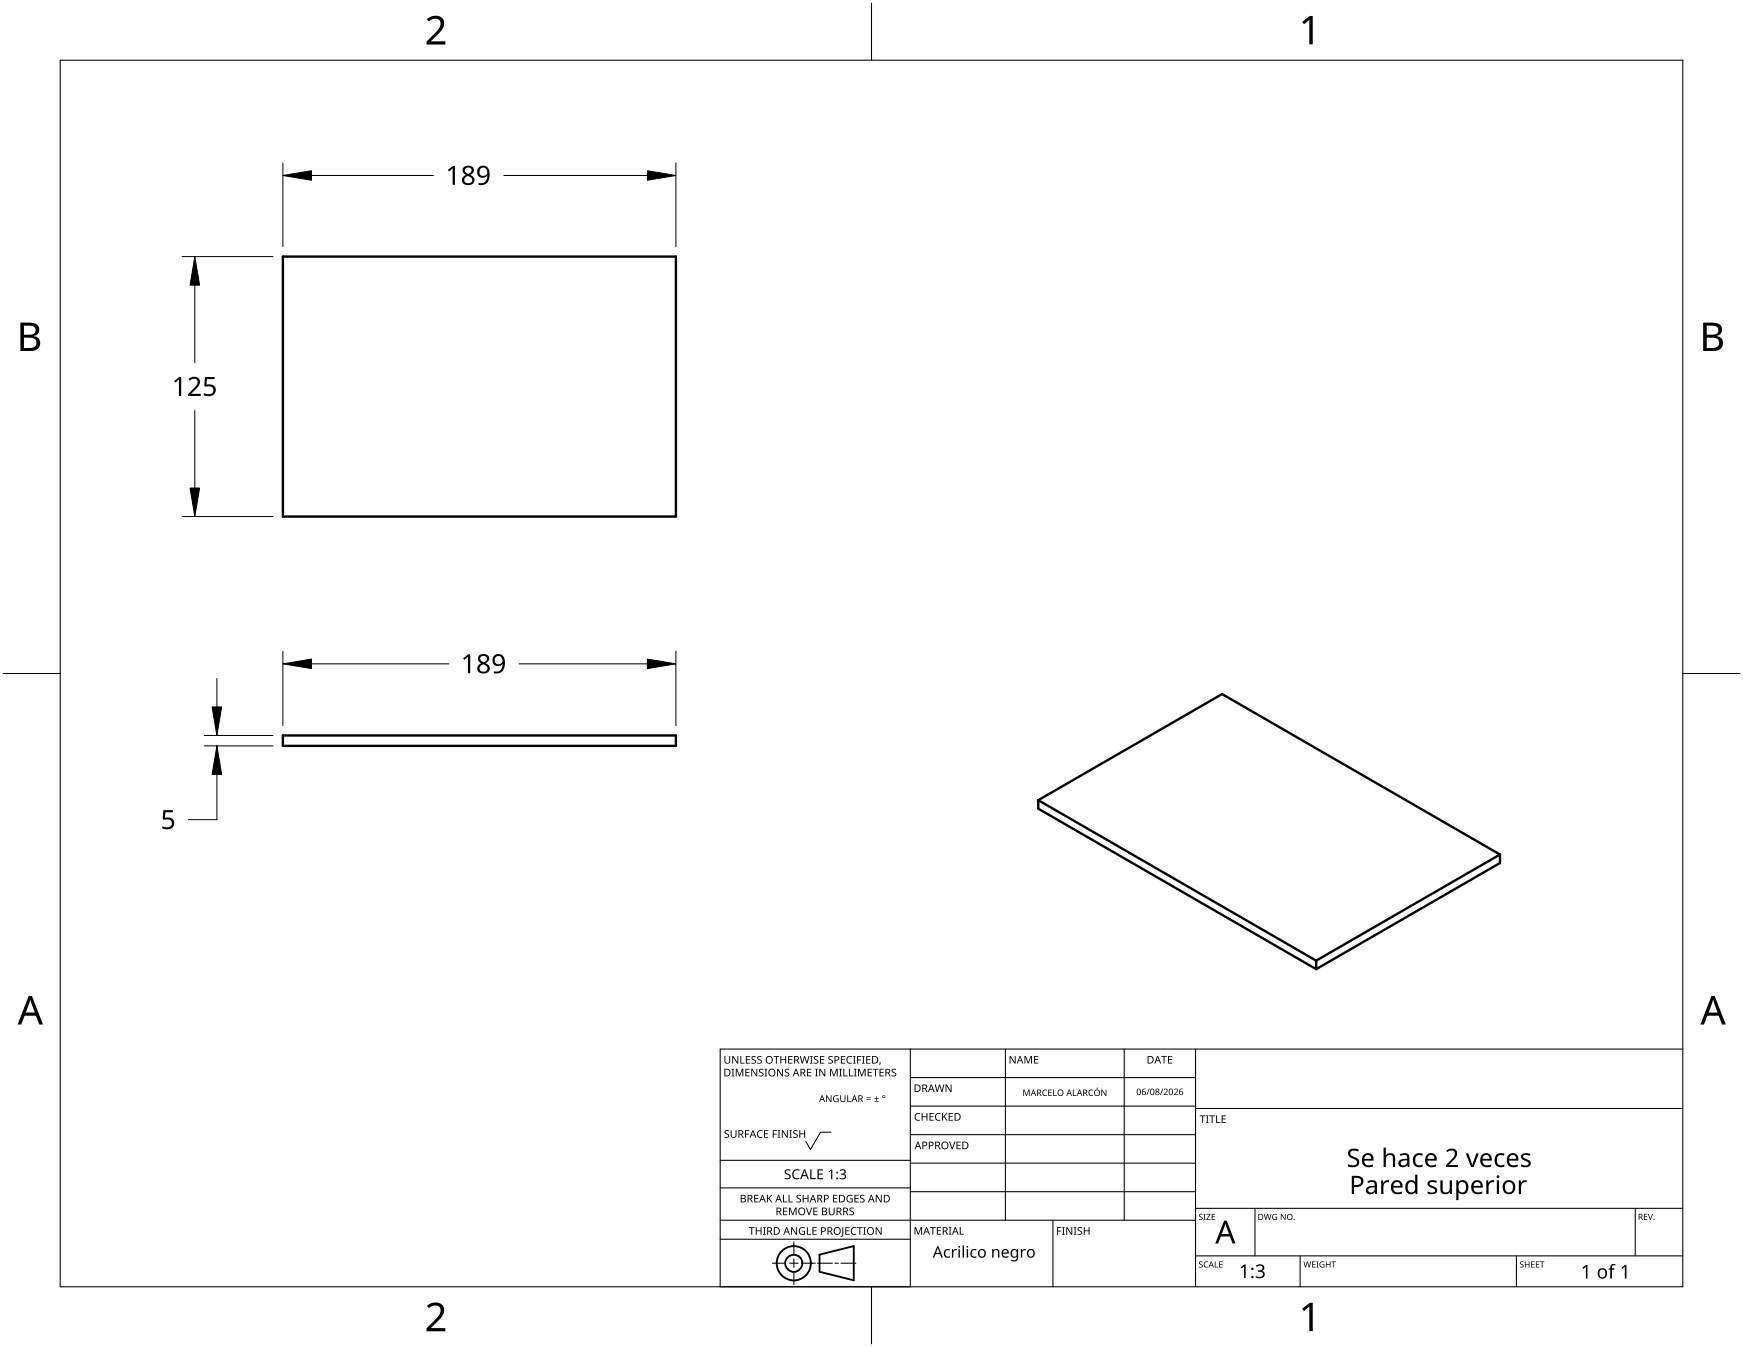
[picture p249: page 1]
