MRCDPLS/FdD_Equipo_07/Proyecto/MóduloMecánico/V3.0/Onshape/Planos/Paredes laterales.pdf

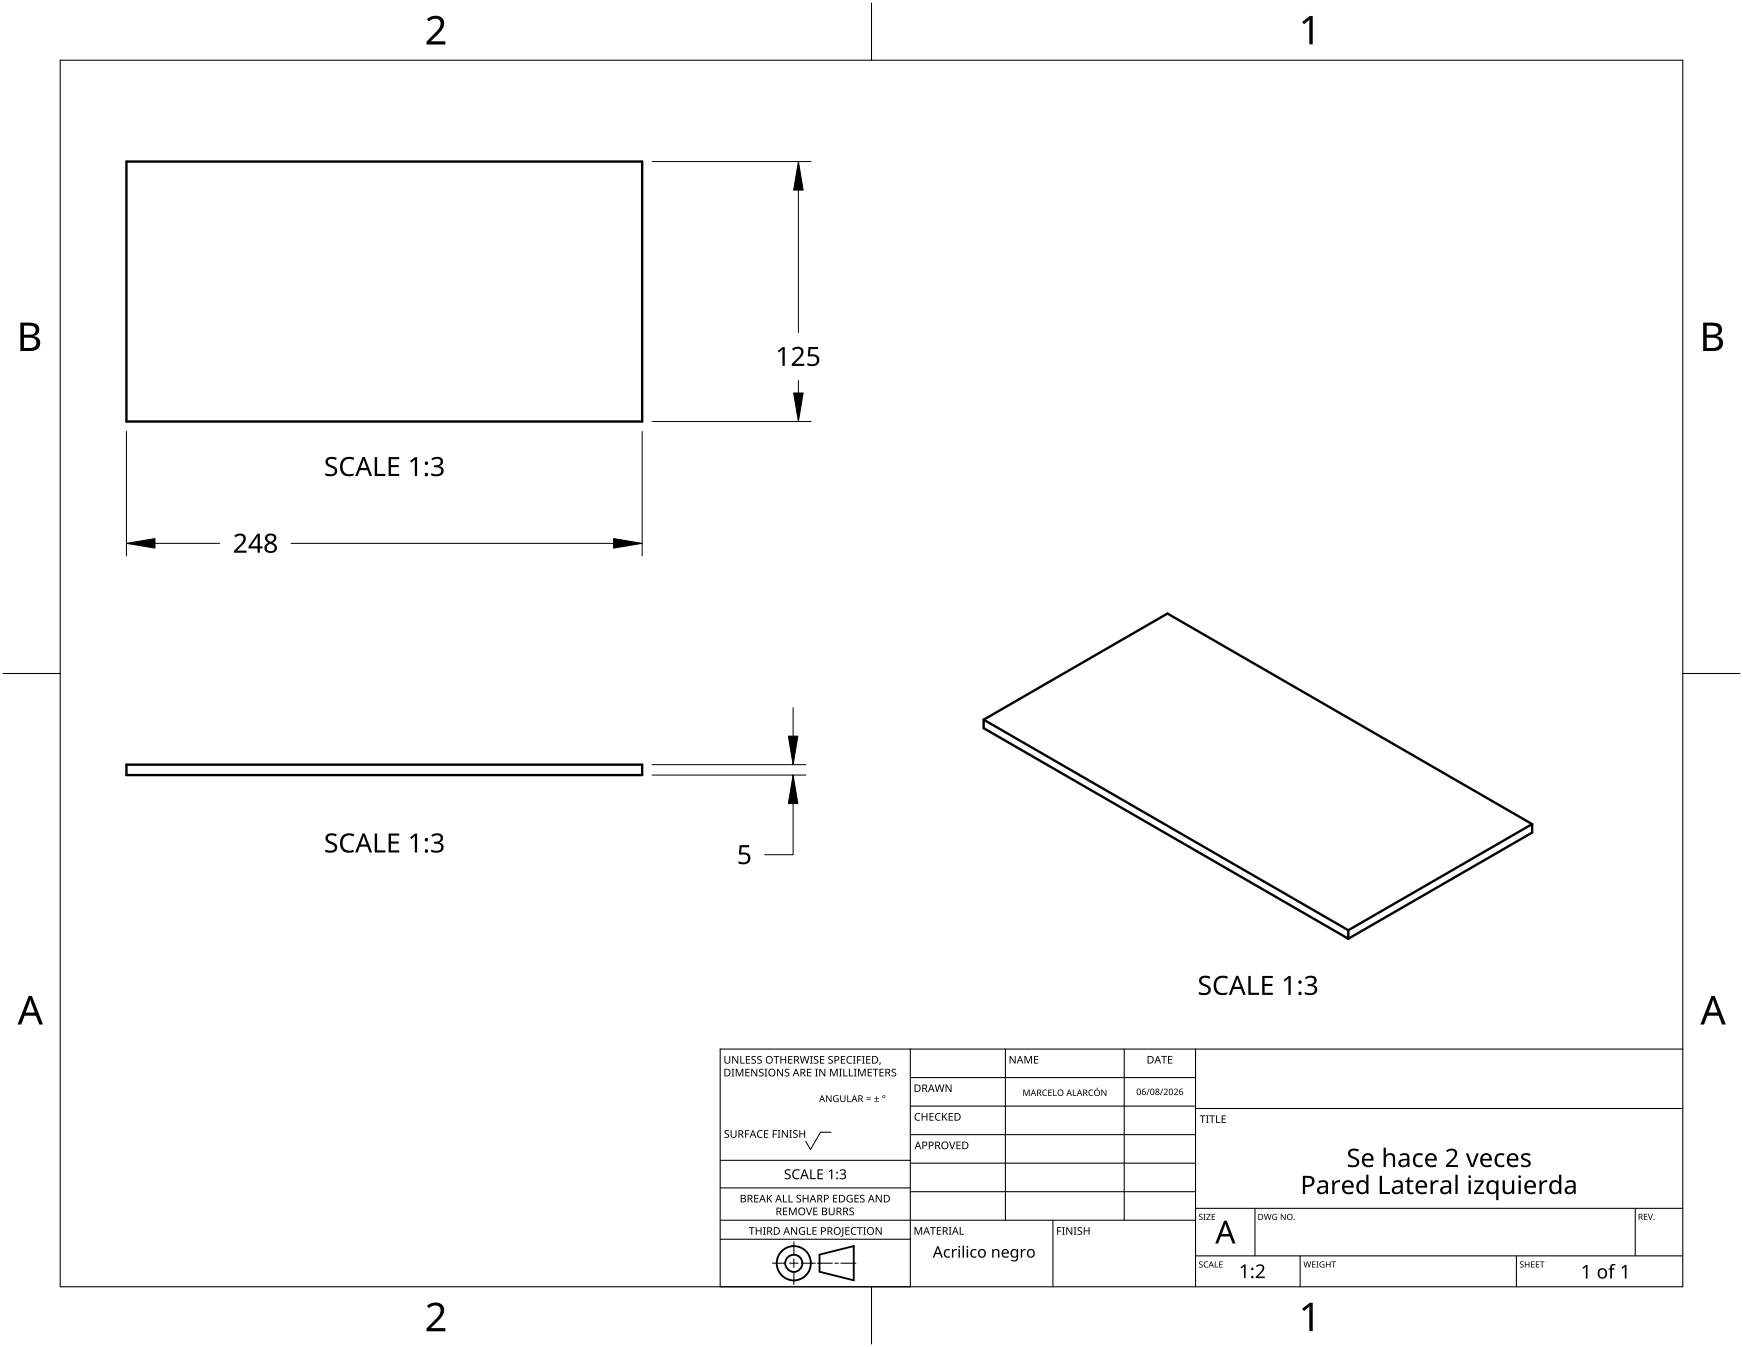
[picture p250: page 1]
