MRCDPLS/FdD_Equipo_07/Proyecto/MóduloMecánico/V3.0/Onshape/Planos/Puerta_inf_prin.pdf

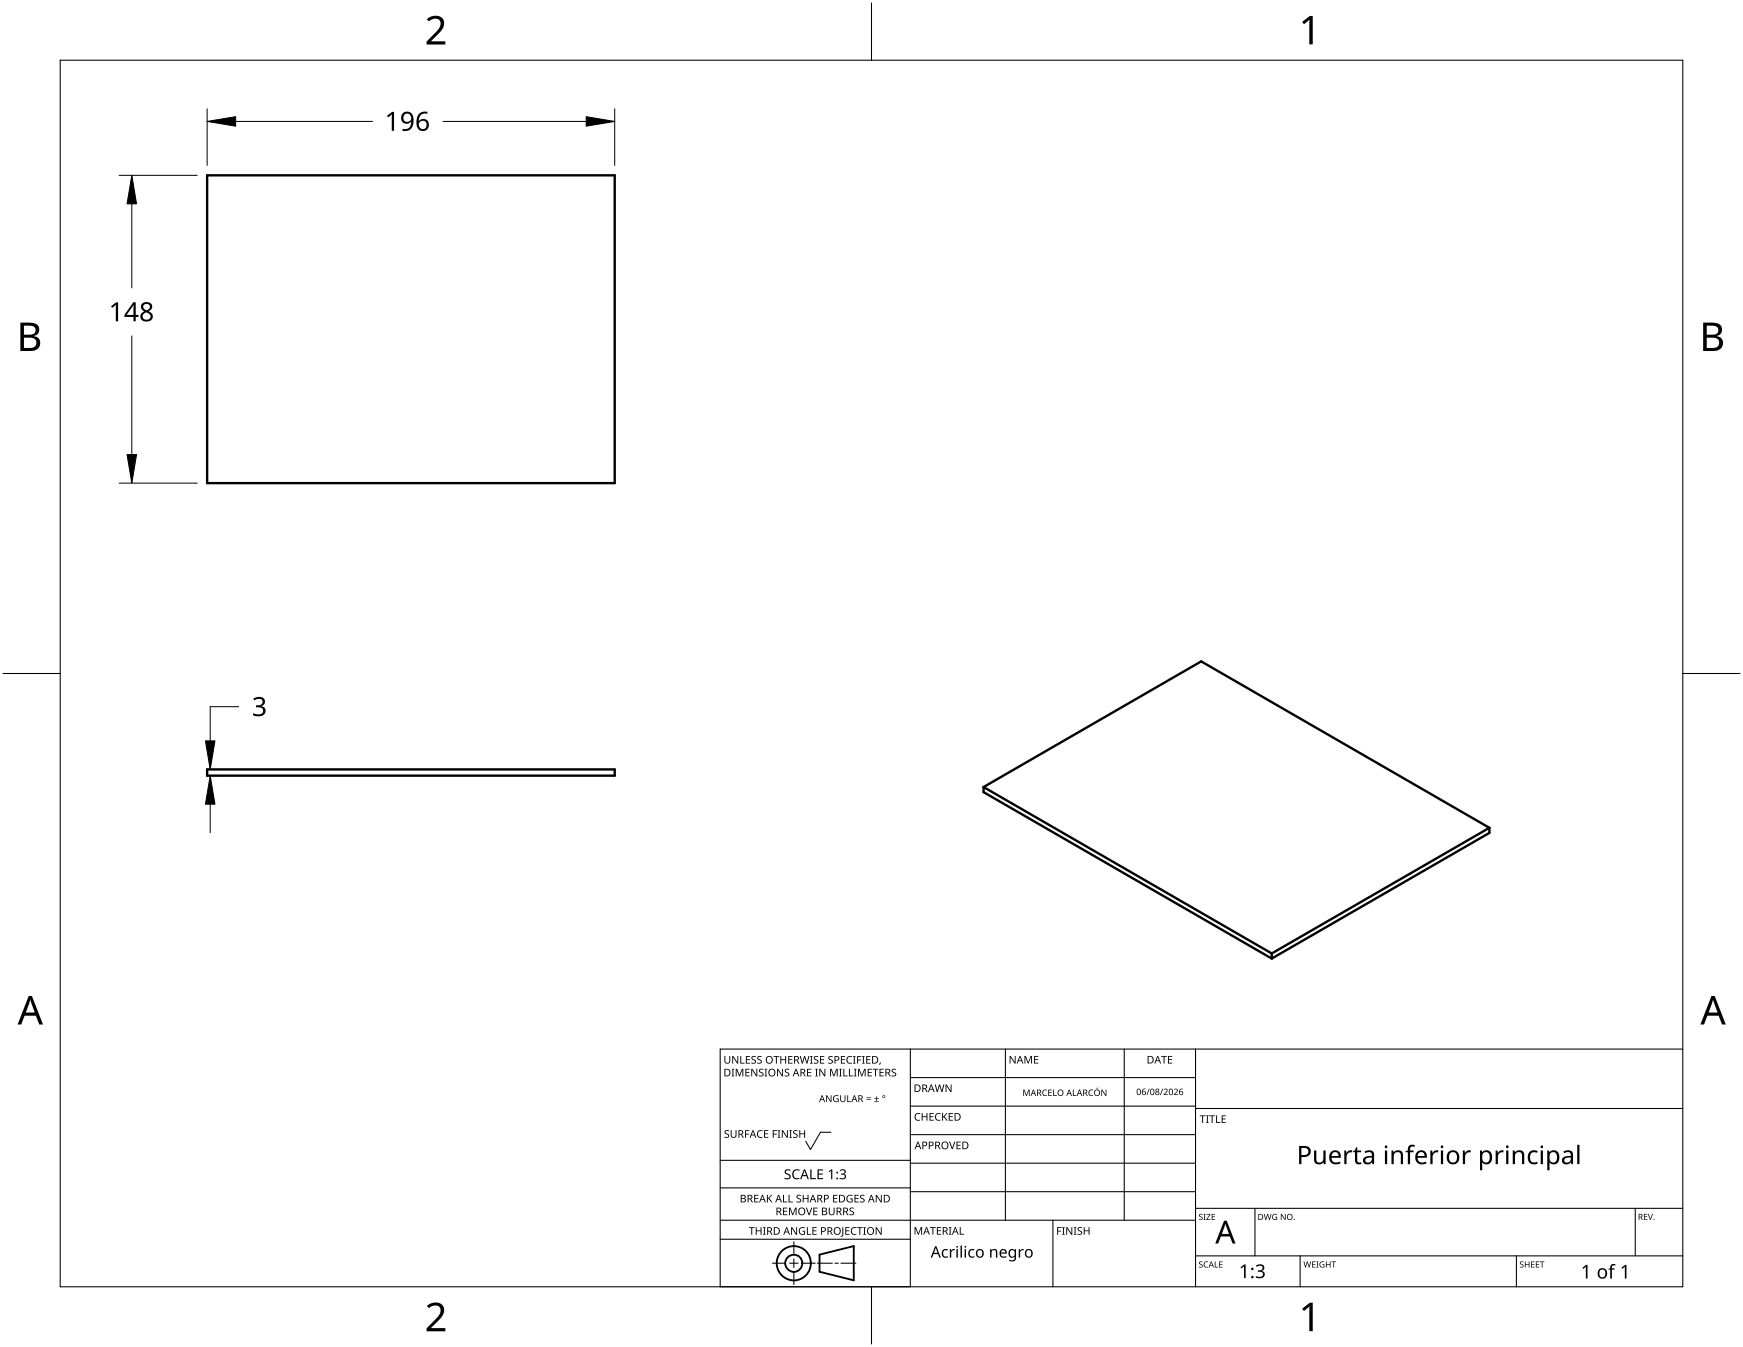
[picture p251: page 1]
