MRCDPLS/FdD_Equipo_07/Proyecto/MóduloMecánico/V3.0/Onshape/Planos/Puerta_sup_Princ.pdf

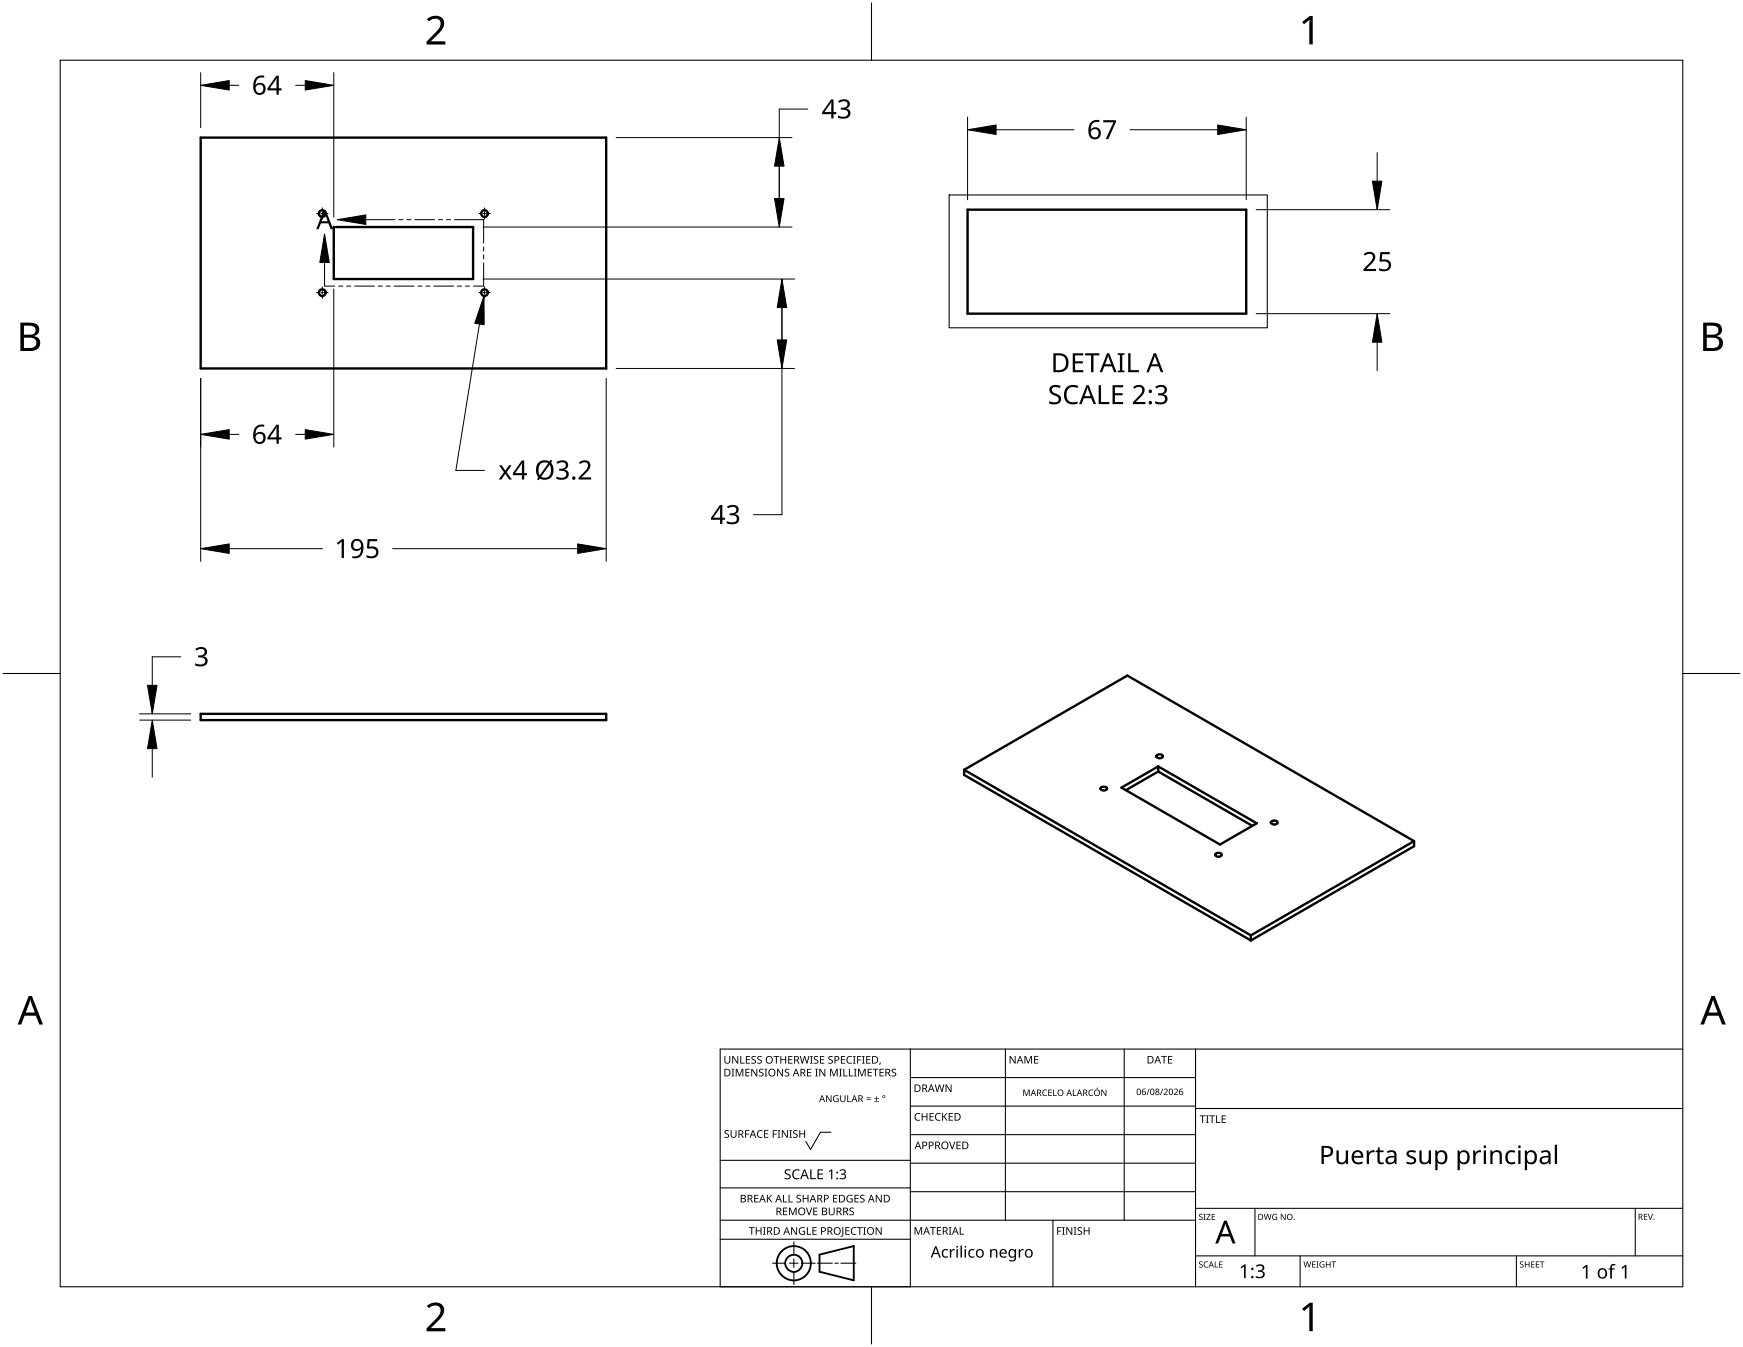
[picture p252: page 1]
