MRCDPLS/FdD_Equipo_07/Proyecto/MóduloMecánico/V2.0/Onshape/Planos/V2_Cubierta para camara.pdf

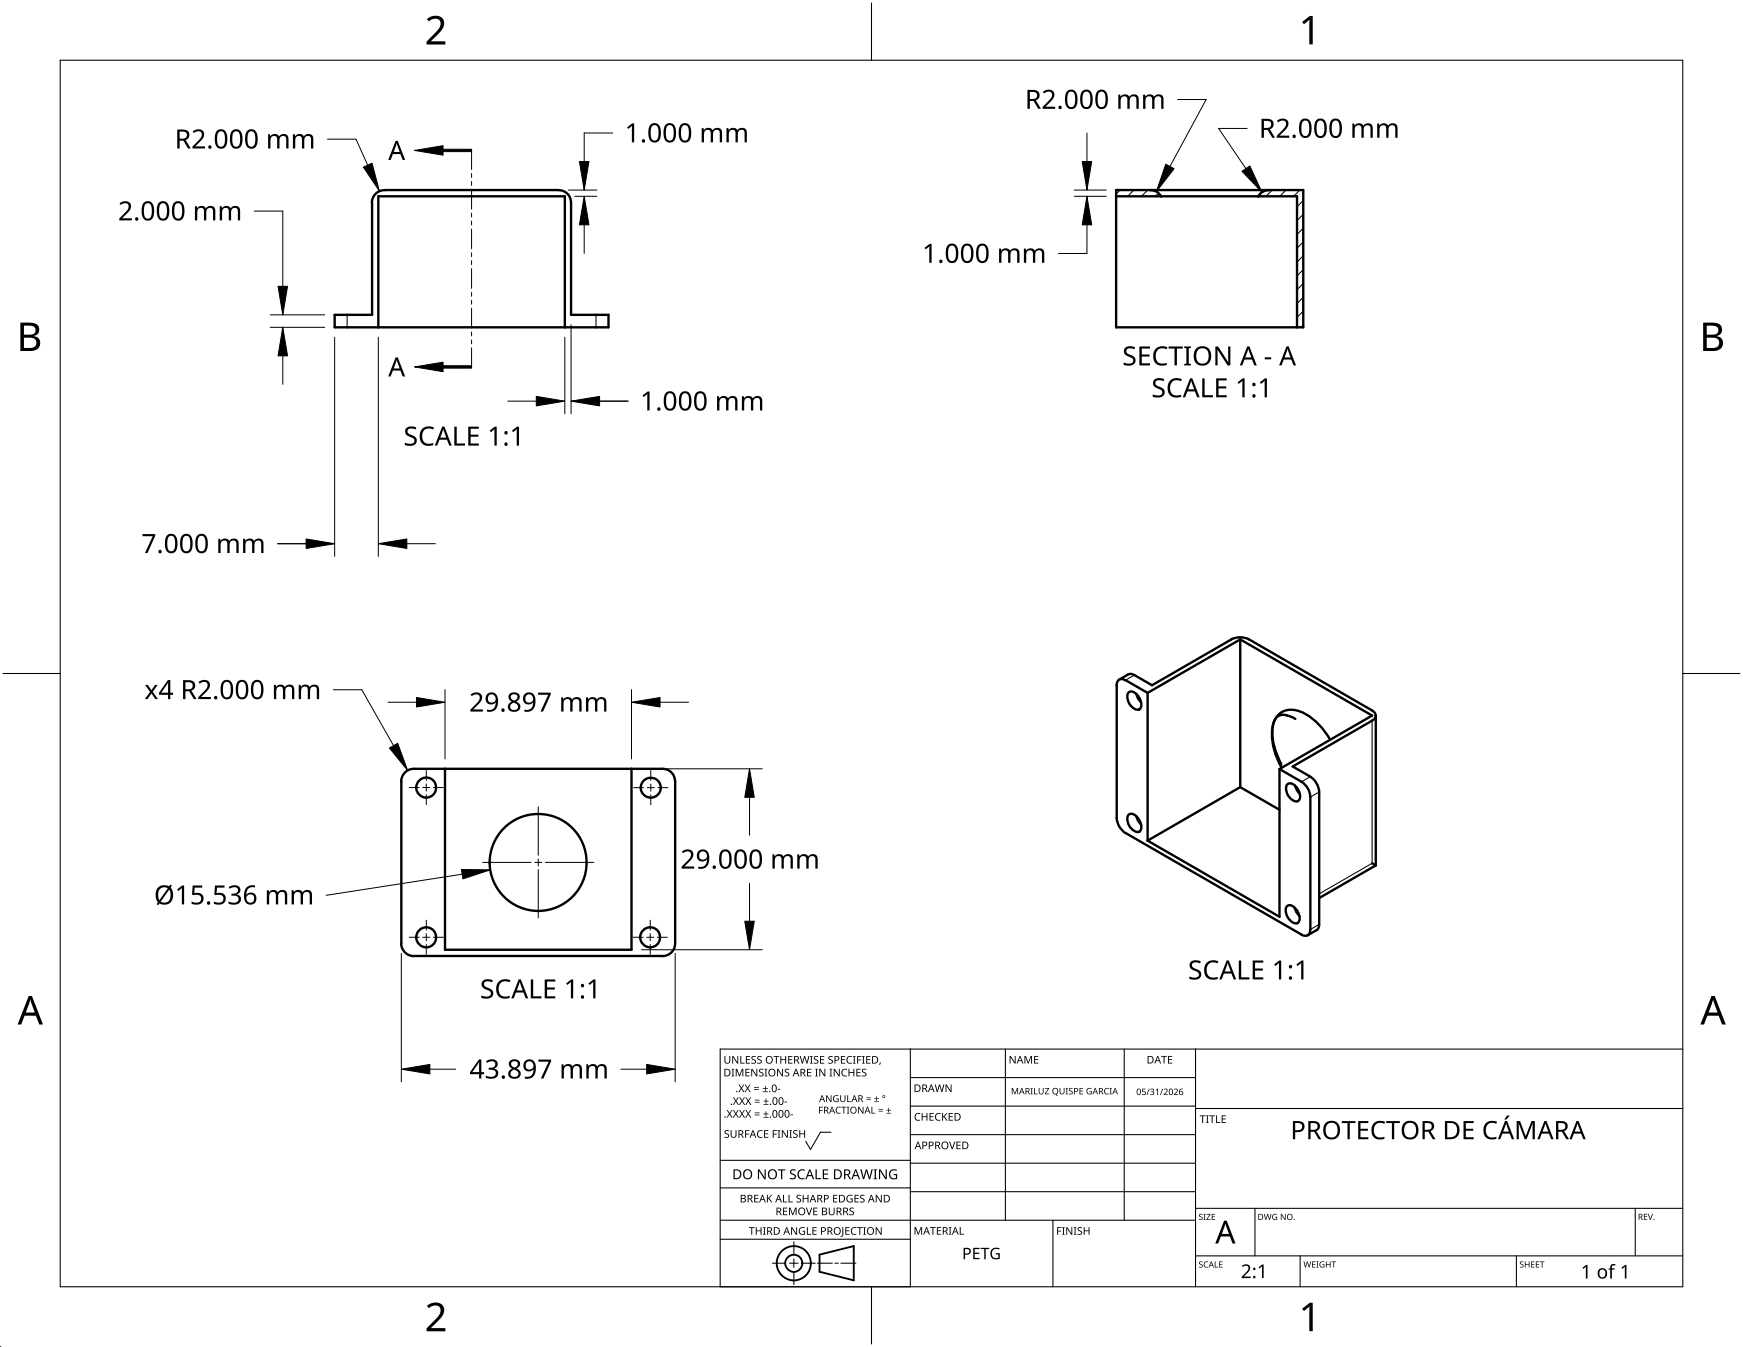
[picture p253: page 1]
