MRCDPLS/FdD_Equipo_07/Proyecto/MóduloSoftware/board_config.h

#ifndef BOARD_CONFIG_H
#define BOARD_CONFIG_H

//===================
// Select camera model
//===================

//#define CAMERA_MODEL_WROVER_KIT
//#define CAMERA_MODEL_ESP_EYE
//#define CAMERA_MODEL_ESP32S3_EYE
//#define CAMERA_MODEL_AI_THINKER

#define CAMERA_MODEL_XIAO_ESP32S3

#include "camera_pins.h"

#endif  // BOARD_CONFIG_H
